gbaHD/GBAHD-Shield/static/wiki/168p_w_fuses.png

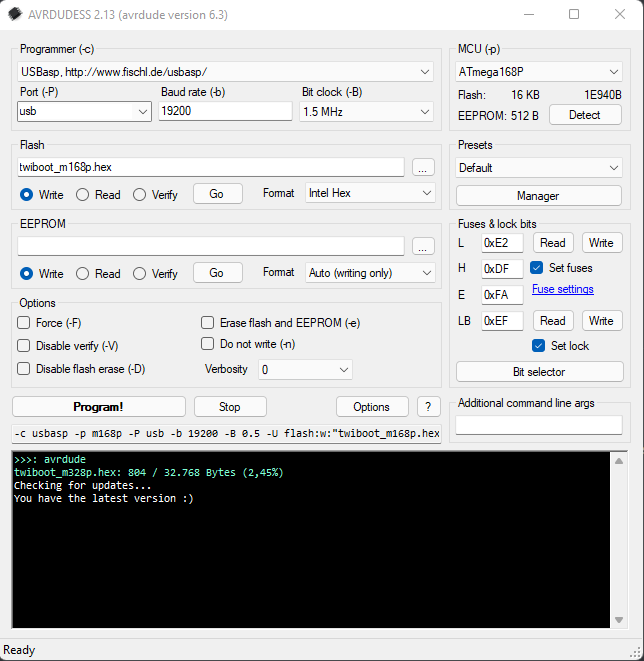
static/wiki/168p_w_fuses.png
