gbaHD/GBAHD-Shield/static/wiki/20210416_back.jpeg

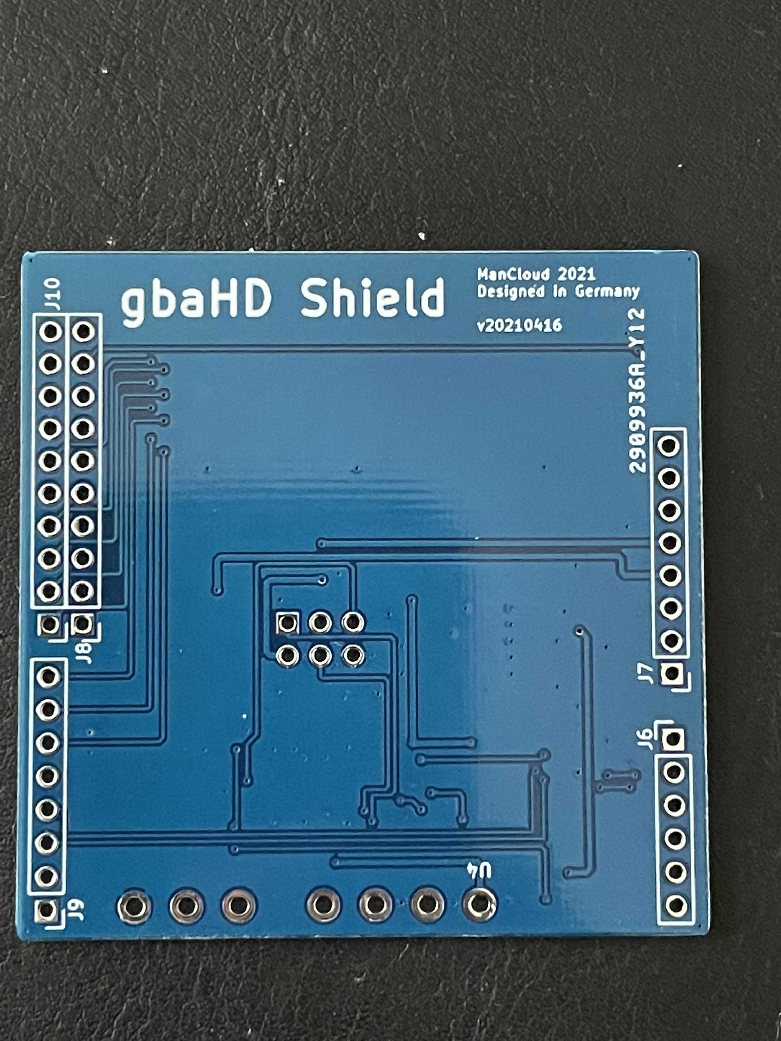
static/wiki/20210416_back.jpeg
