gbaHD/GBAHD-Shield/static/wiki/20210416_front.jpeg

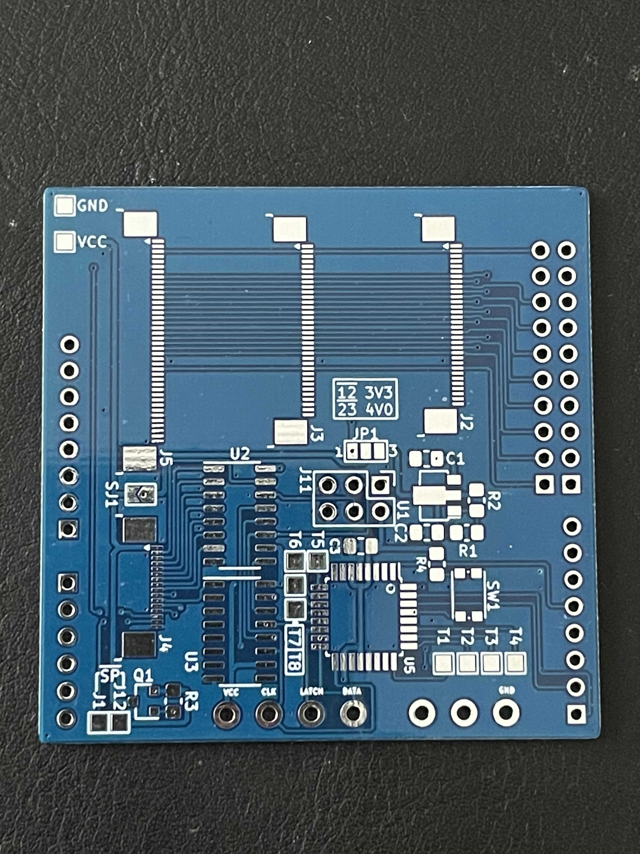
static/wiki/20210416_front.jpeg
