gbaHD/GBAHD-Shield/static/wiki/agb-cpu-03_power.jpg

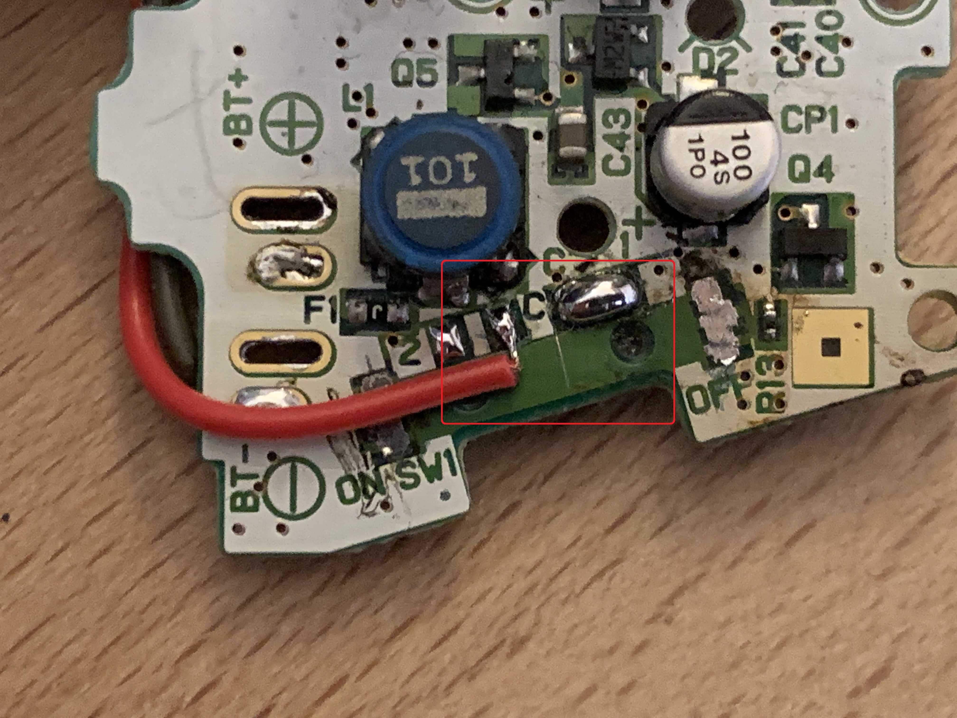
static/wiki/agb-cpu-03_power.jpg
