gbaHD/GBAHD-Shield/static/wiki/agb_cpu_03_clock-res.jpg

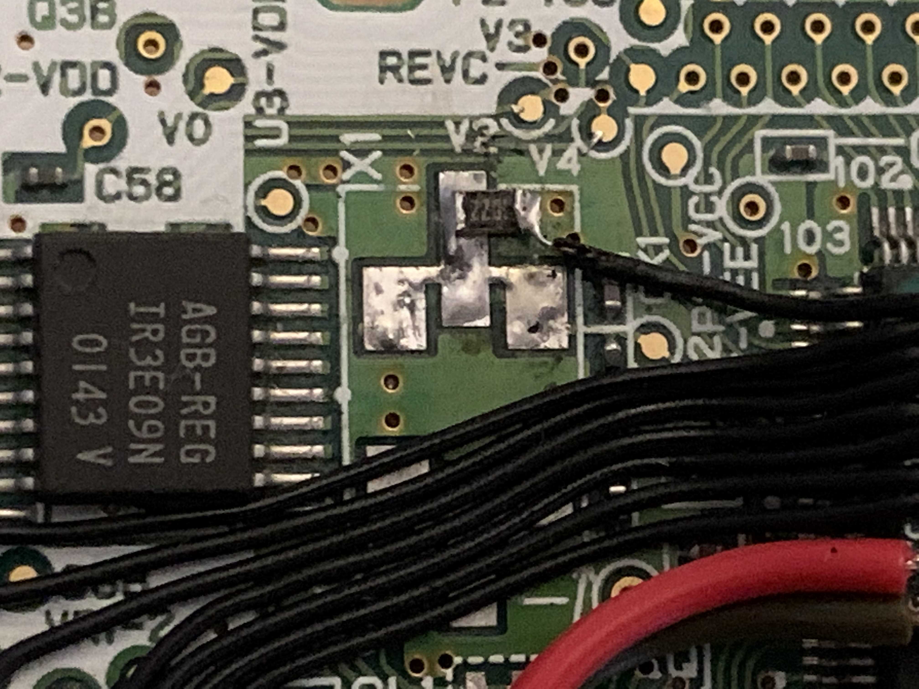
static/wiki/agb_cpu_03_clock-res.jpg
