gbaHD/GBAHD-Shield/static/wiki/arduino_nano_pins.jpg

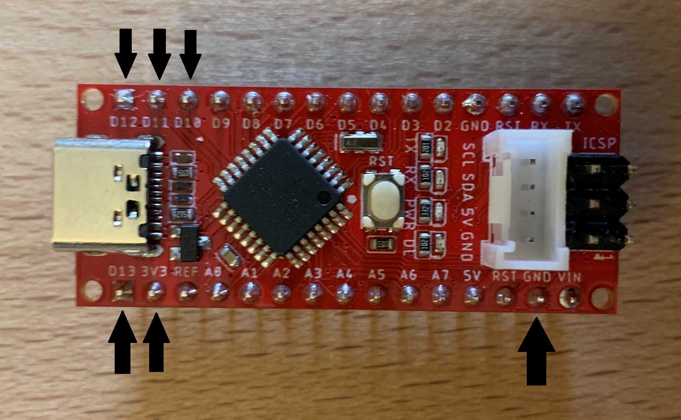
static/wiki/arduino_nano_pins.jpg
