gbaHD/GBAHD-Shield/static/wiki/arduinoide_isp_sketch2.jpg

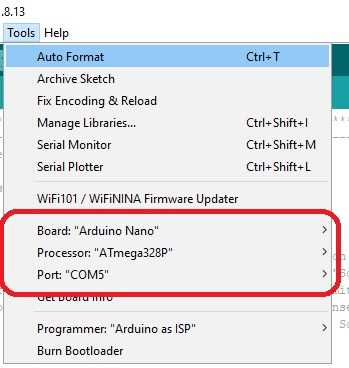
static/wiki/arduinoide_isp_sketch2.jpg
