gbaHD/GBAHD-Shield/static/wiki/arduinoide_isp_sketch.jpg

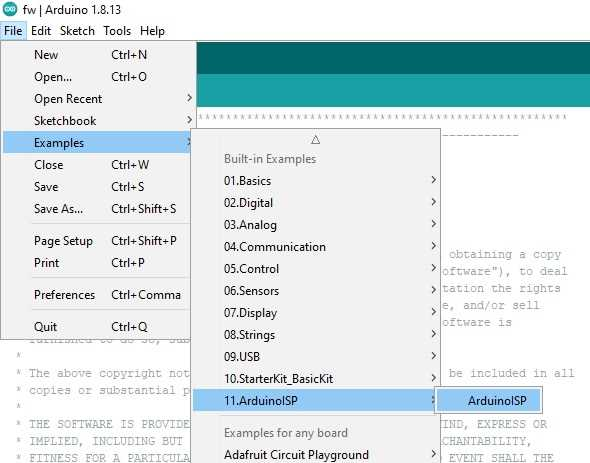
static/wiki/arduinoide_isp_sketch.jpg
