gbaHD/GBAHD-Shield/static/wiki/arduinoide_isp_sketch_upload.jpg

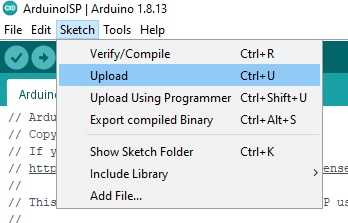
static/wiki/arduinoide_isp_sketch_upload.jpg
