gbaHD/GBAHD-Shield/static/wiki/arduinoide_shield.jpg

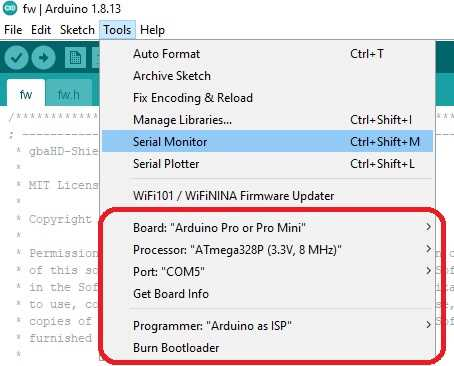
static/wiki/arduinoide_shield.jpg
