gbaHD/GBAHD-Shield/static/wiki/arduinoide_shield_upload_w_programmer.jpg

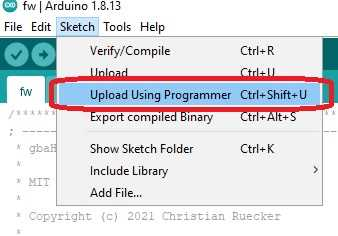
static/wiki/arduinoide_shield_upload_w_programmer.jpg
