gbaHD/GBAHD-Shield/static/wiki/arduinoideprefs.JPG

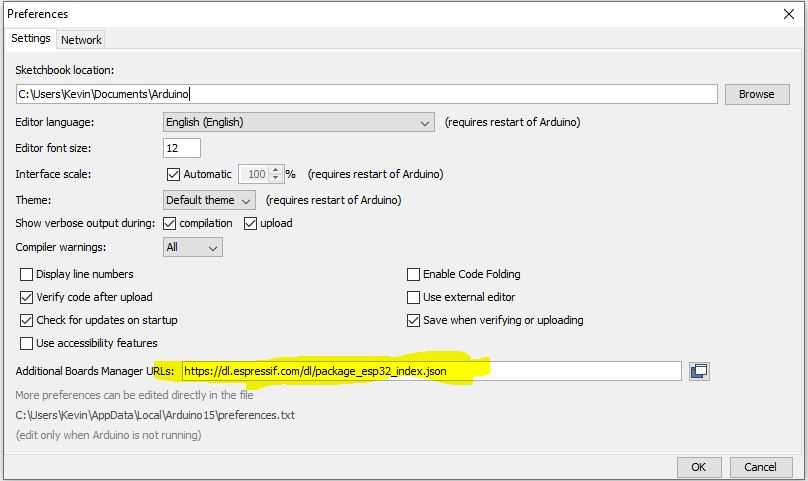
static/wiki/arduinoideprefs.JPG
