gbaHD/GBAHD-Shield/static/wiki/avrdude_fuses_w_website.JPG

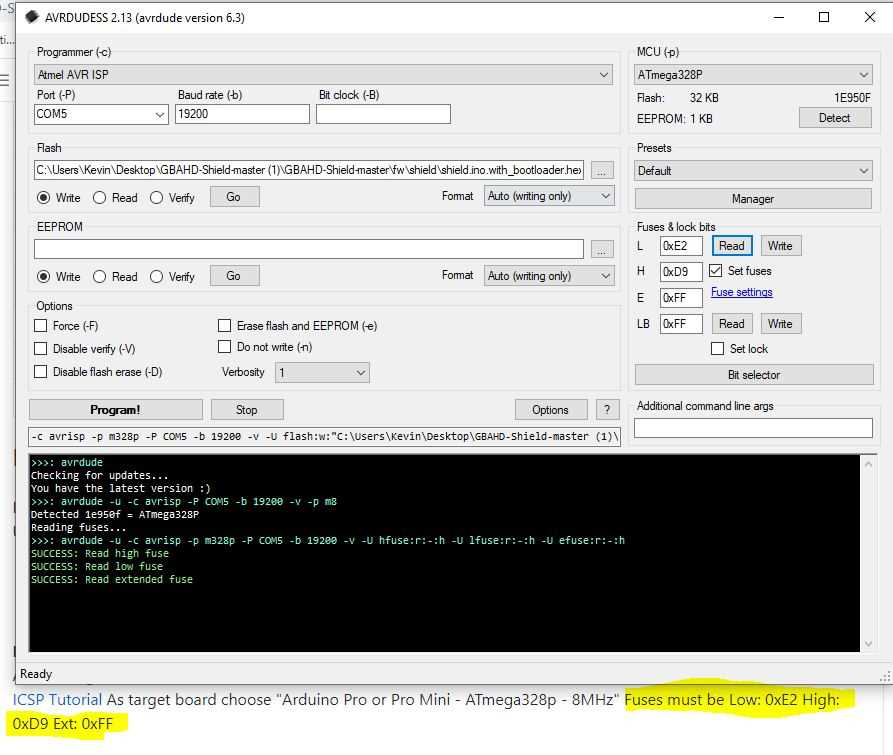
static/wiki/avrdude_fuses_w_website.JPG
