gbaHD/GBAHD-Shield/static/wiki/boardsmanager.JPG

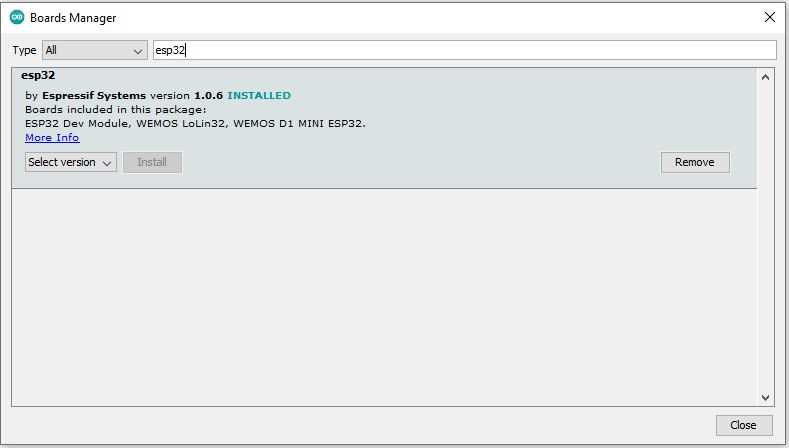
static/wiki/boardsmanager.JPG
