gbaHD/GBAHD-Shield/static/wiki/breadboard_programing.jpg

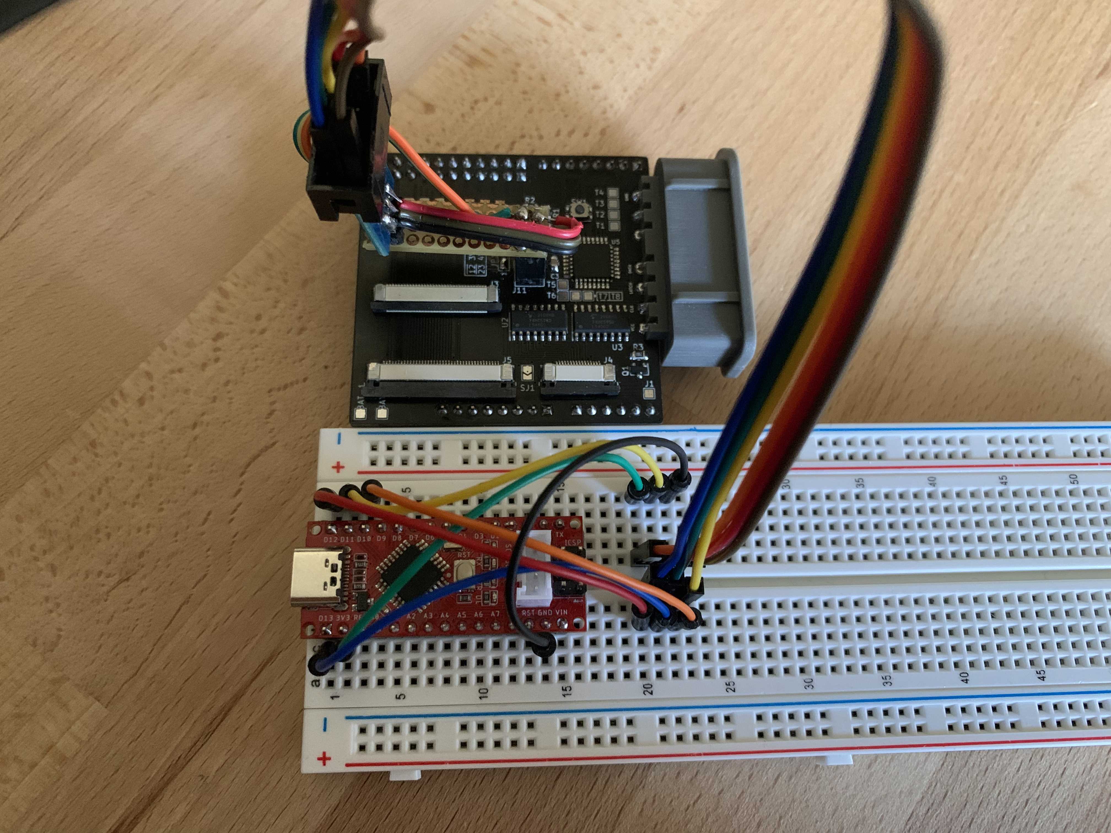
static/wiki/breadboard_programing.jpg
