gbaHD/GBAHD-Shield/static/wiki/case_ogba/35mm_jack.jpg

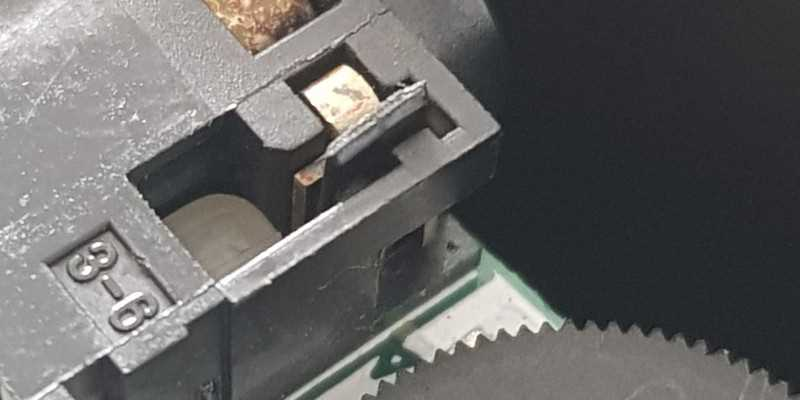
static/wiki/case_ogba/35mm_jack.jpg
