gbaHD/GBAHD-Shield/static/wiki/case_ogba/obga_top.jpg

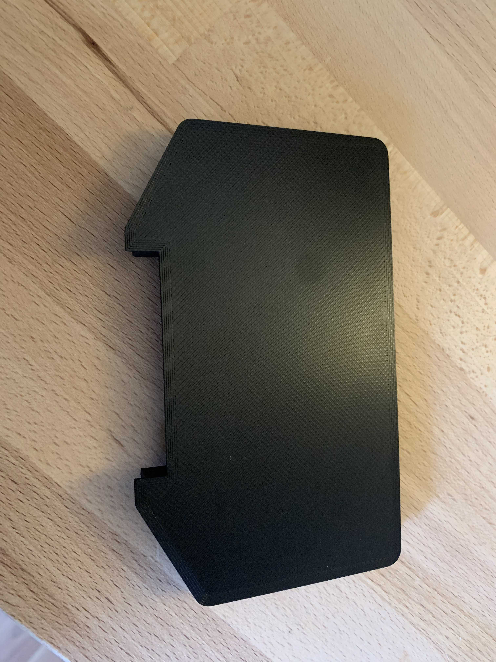
static/wiki/case_ogba/obga_top.jpg
