gbaHD/GBAHD-Shield/static/wiki/case_ogba/ogba_back.jpg

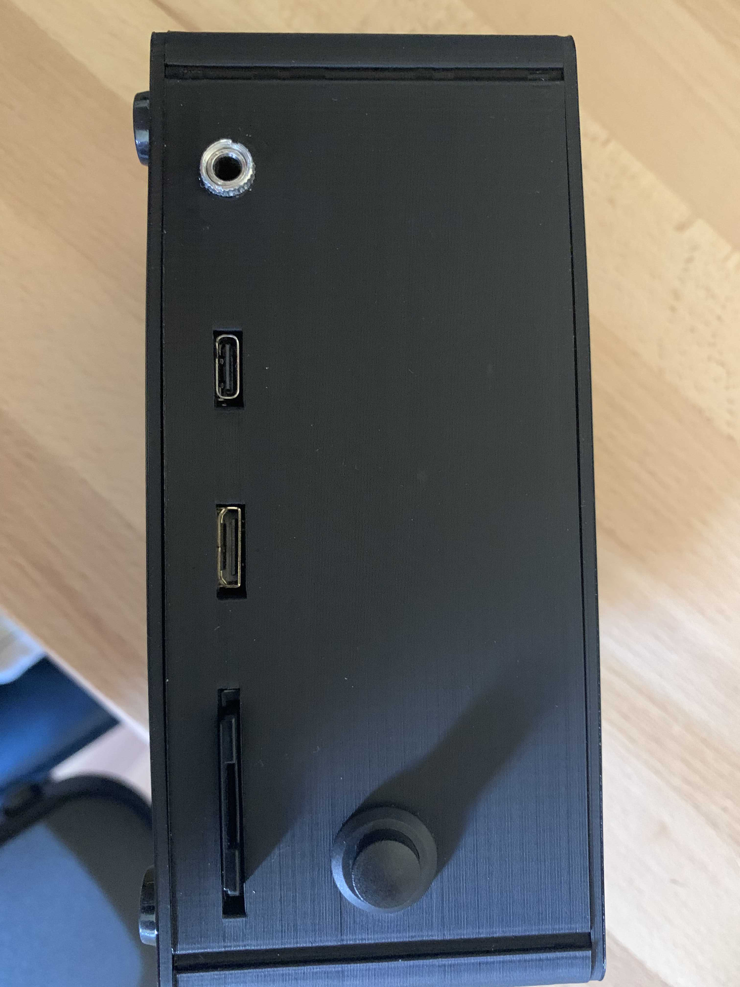
static/wiki/case_ogba/ogba_back.jpg
