gbaHD/GBAHD-Shield/static/wiki/case_ogba/ogba_bottom.jpg

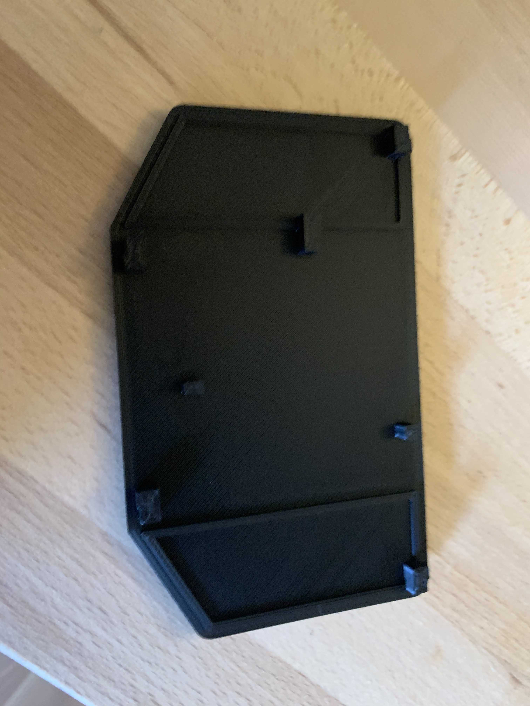
static/wiki/case_ogba/ogba_bottom.jpg
