gbaHD/GBAHD-Shield/static/wiki/case_ogba/ogba_bottom_finished.jpg

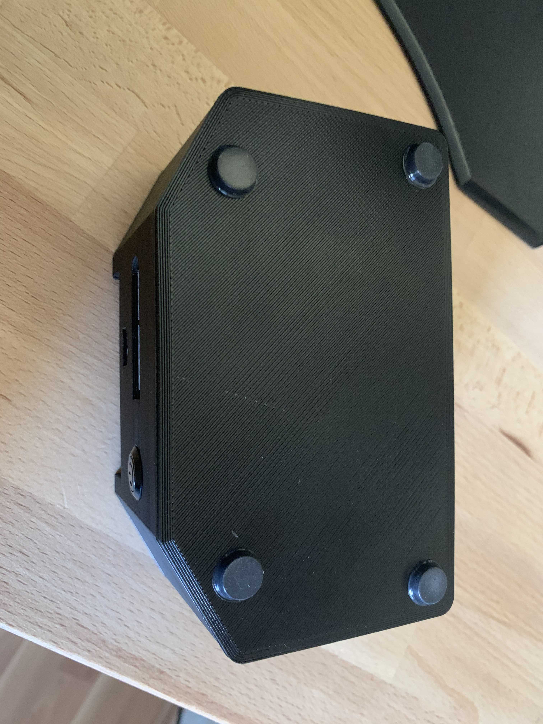
static/wiki/case_ogba/ogba_bottom_finished.jpg
