gbaHD/GBAHD-Shield/static/wiki/case_ogba/ogba_cartridgeflap.jpg

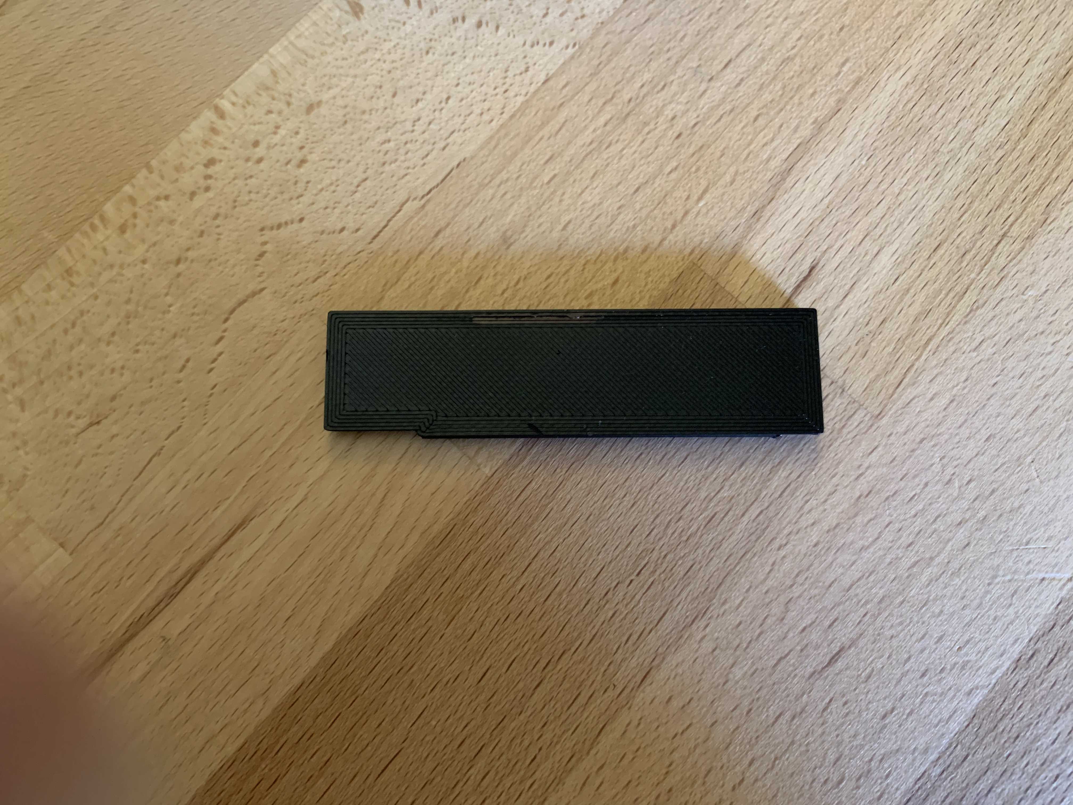
static/wiki/case_ogba/ogba_cartridgeflap.jpg
