gbaHD/GBAHD-Shield/static/wiki/case_ogba/ogba_case.jpg

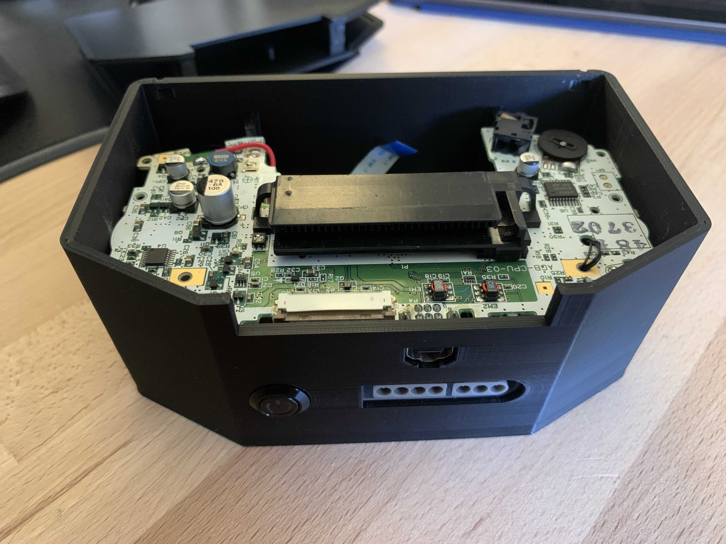
static/wiki/case_ogba/ogba_case.jpg
