gbaHD/GBAHD-Shield/static/wiki/case_ogba/ogba_case_angledspartan.jpg

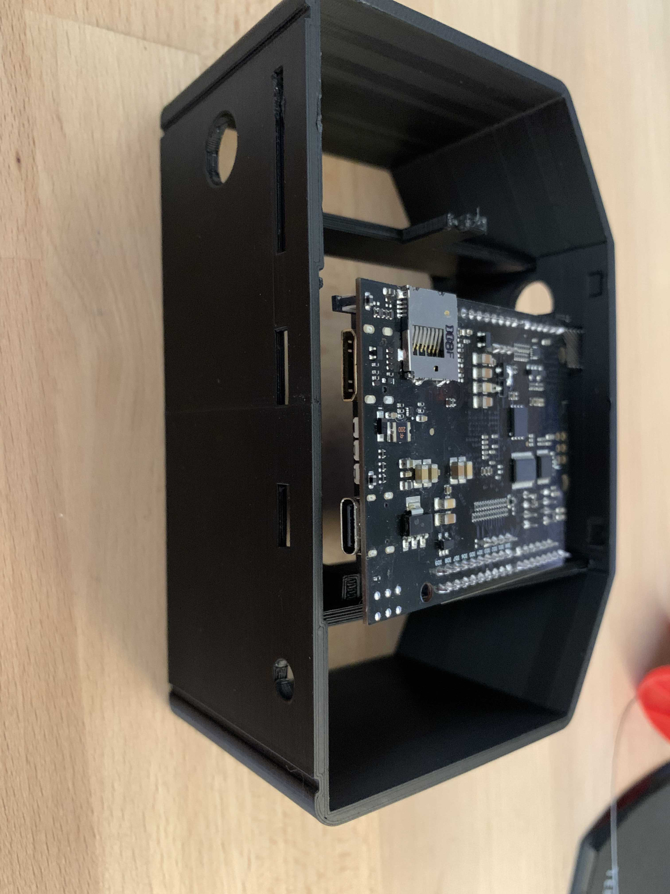
static/wiki/case_ogba/ogba_case_angledspartan.jpg
