gbaHD/GBAHD-Shield/static/wiki/case_ogba/ogba_case_bottom.jpg

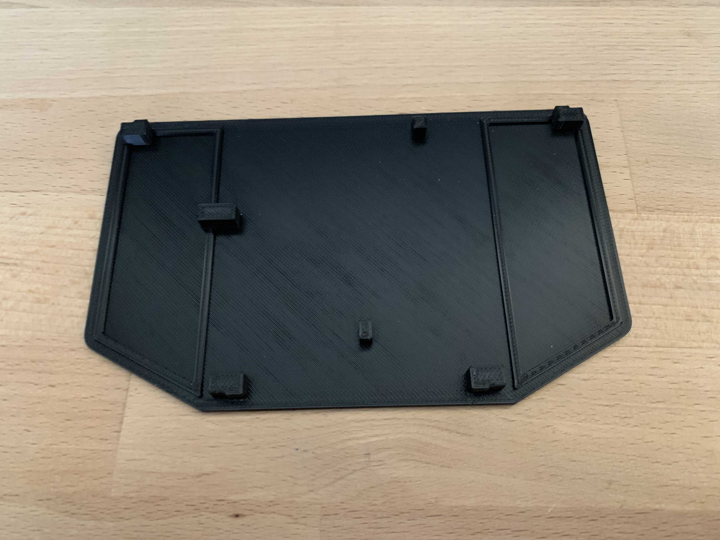
static/wiki/case_ogba/ogba_case_bottom.jpg
