gbaHD/GBAHD-Shield/static/wiki/case_ogba/ogba_case_cartflap.jpg

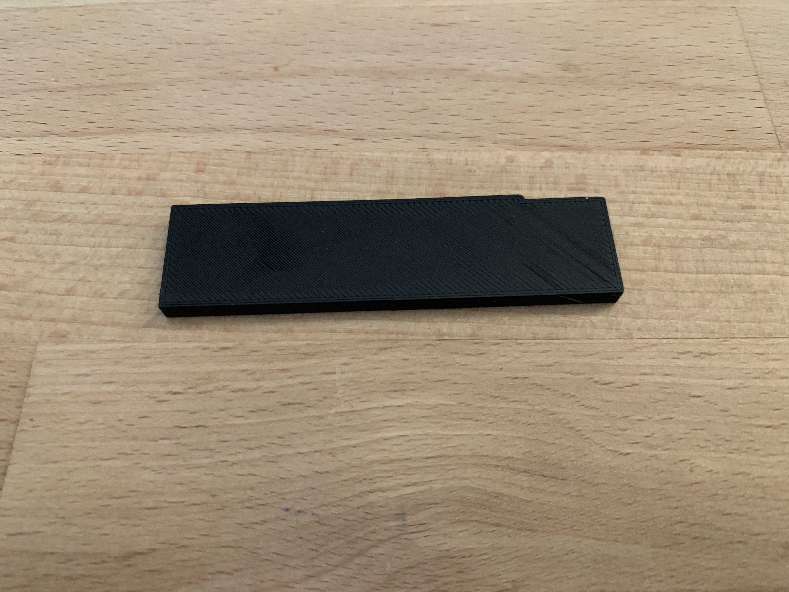
static/wiki/case_ogba/ogba_case_cartflap.jpg
