gbaHD/GBAHD-Shield/static/wiki/case_ogba/ogba_case_empty.jpg

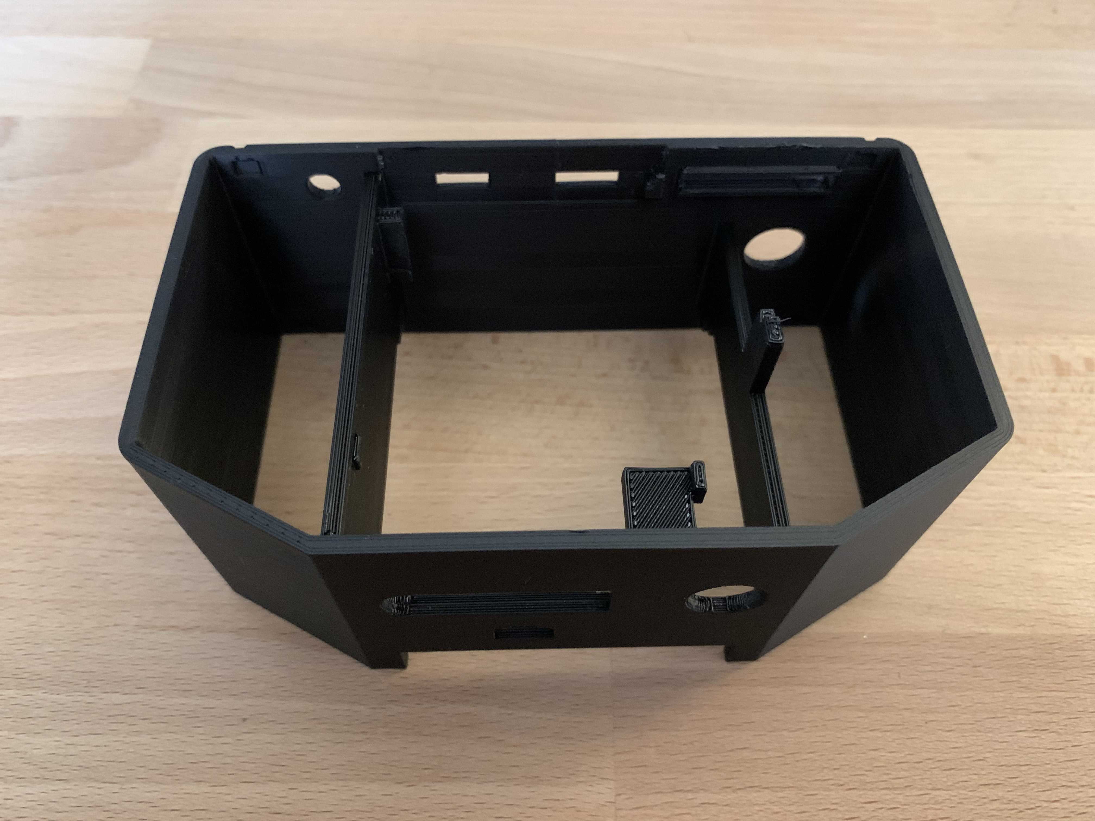
static/wiki/case_ogba/ogba_case_empty.jpg
