gbaHD/GBAHD-Shield/static/wiki/case_ogba/ogba_case_finished.jpg

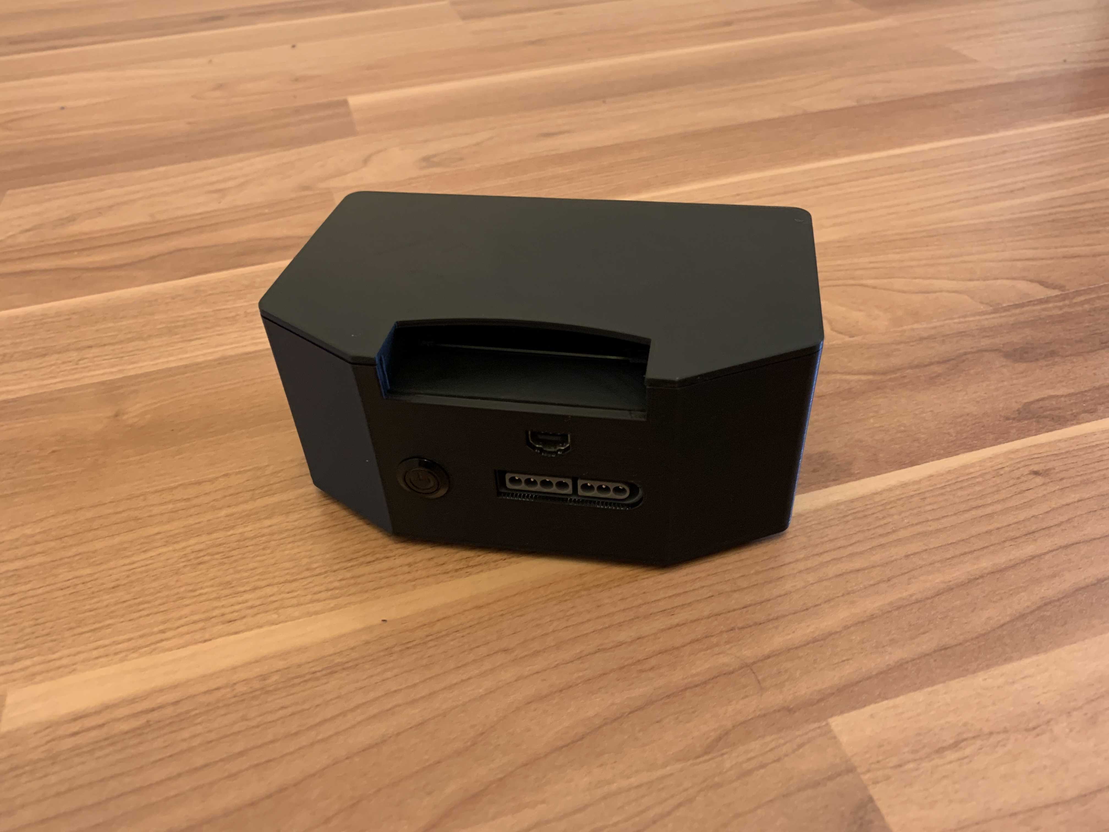
static/wiki/case_ogba/ogba_case_finished.jpg
