gbaHD/GBAHD-Shield/static/wiki/case_ogba/ogba_case_finished_wo_top2.jpg

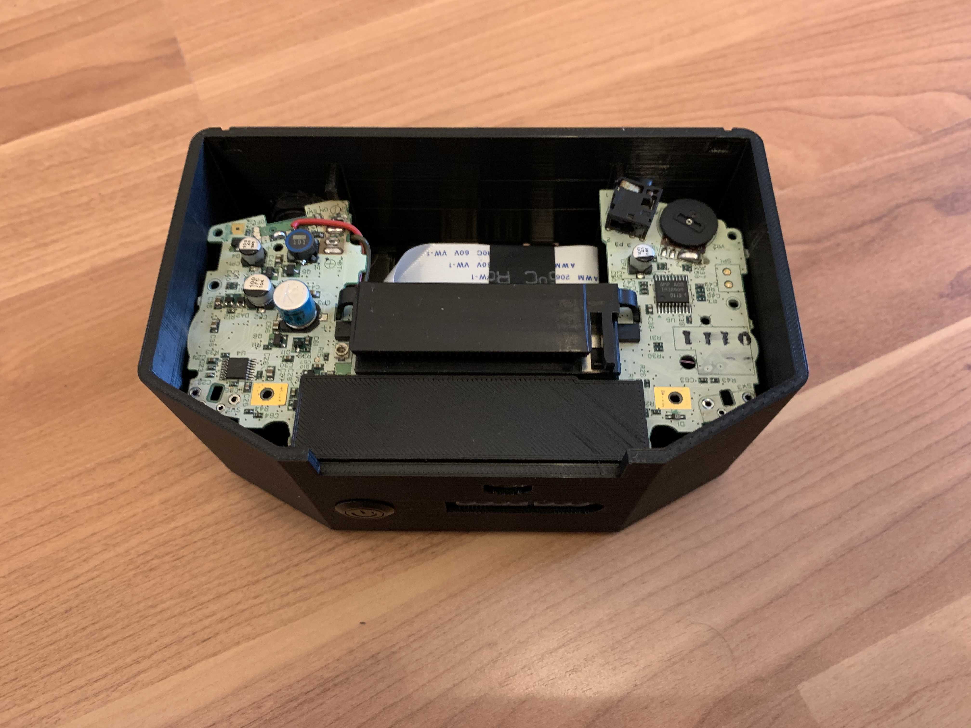
static/wiki/case_ogba/ogba_case_finished_wo_top2.jpg
