gbaHD/GBAHD-Shield/static/wiki/case_ogba/ogba_case_finished_wo_top.jpg

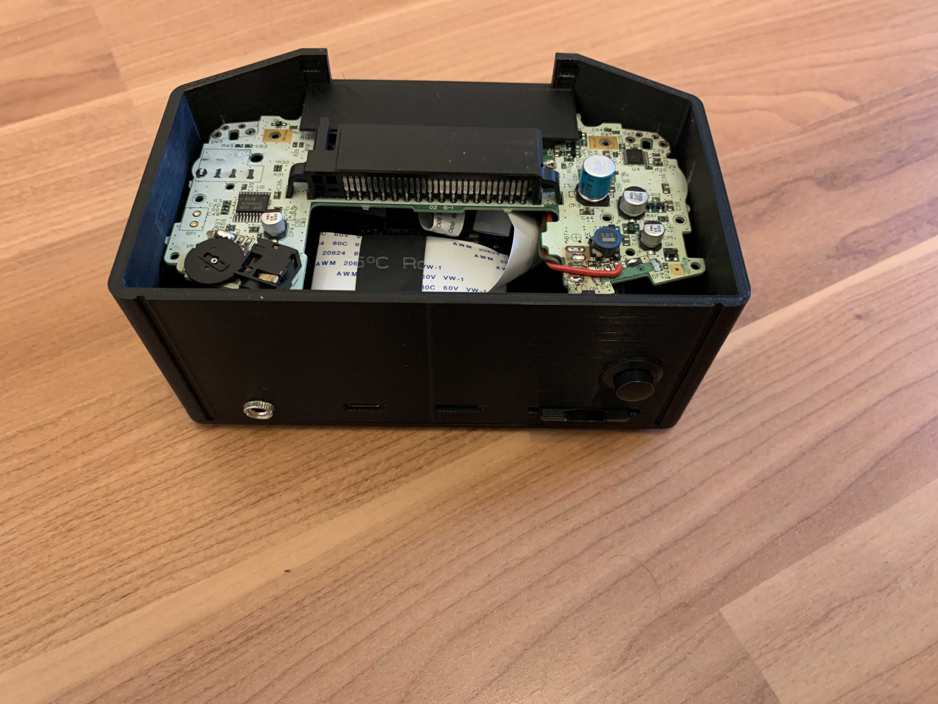
static/wiki/case_ogba/ogba_case_finished_wo_top.jpg
