gbaHD/GBAHD-Shield/static/wiki/case_ogba/ogba_case_gba_w_flex.jpg

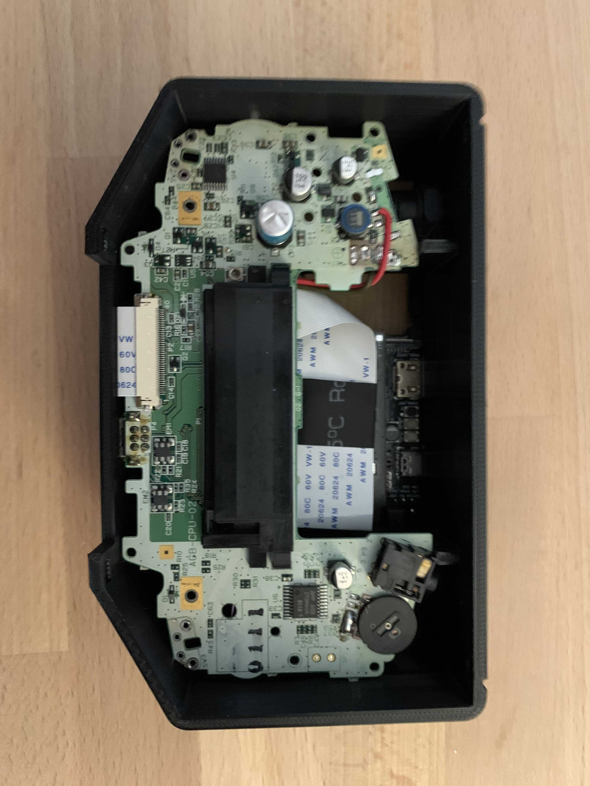
static/wiki/case_ogba/ogba_case_gba_w_flex.jpg
