gbaHD/GBAHD-Shield/static/wiki/case_ogba/ogba_case_gba_wired.jpg

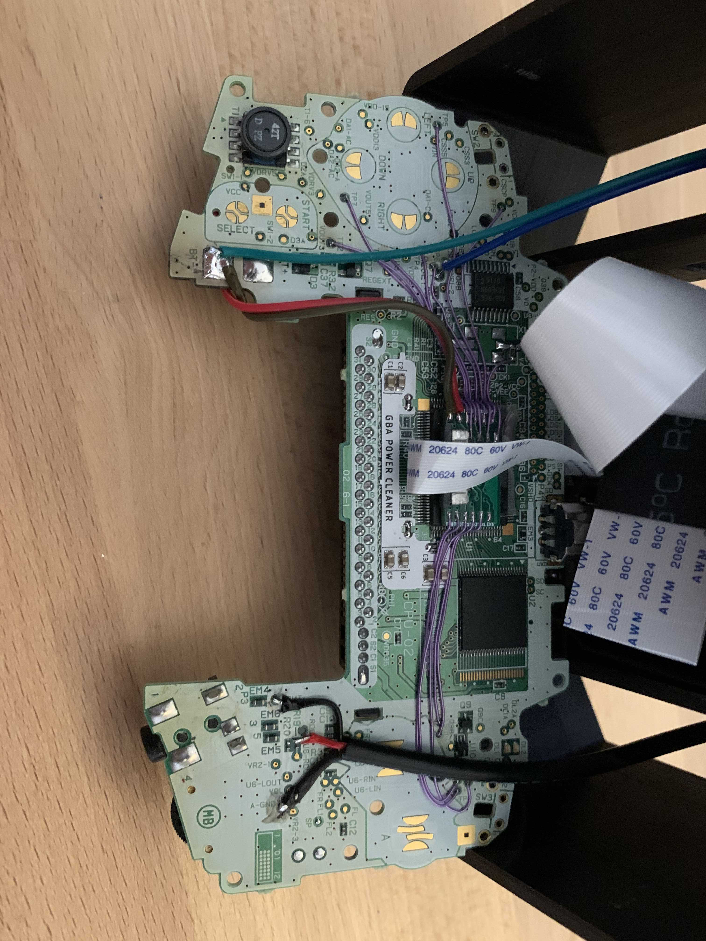
static/wiki/case_ogba/ogba_case_gba_wired.jpg
