gbaHD/GBAHD-Shield/static/wiki/case_ogba/ogba_case_spartan_in2.jpg

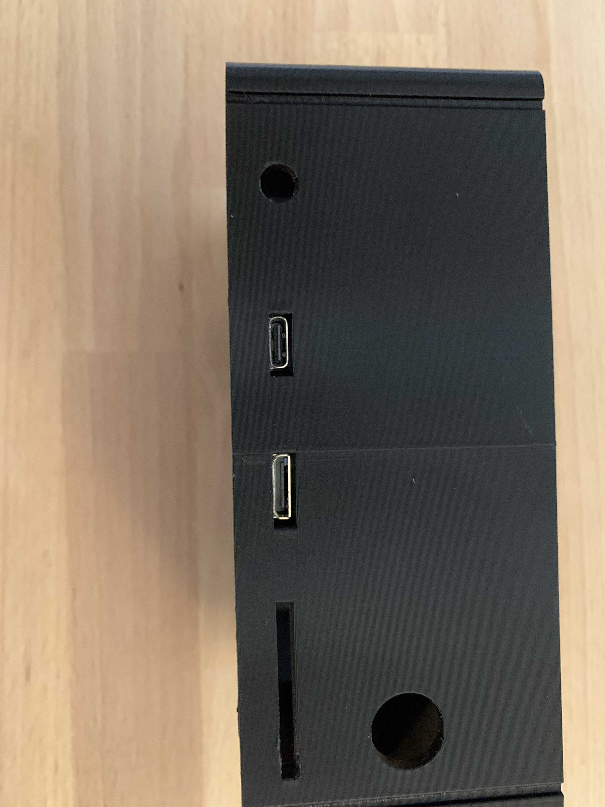
static/wiki/case_ogba/ogba_case_spartan_in2.jpg
