gbaHD/GBAHD-Shield/static/wiki/case_ogba/ogba_case_spartan_in.jpg

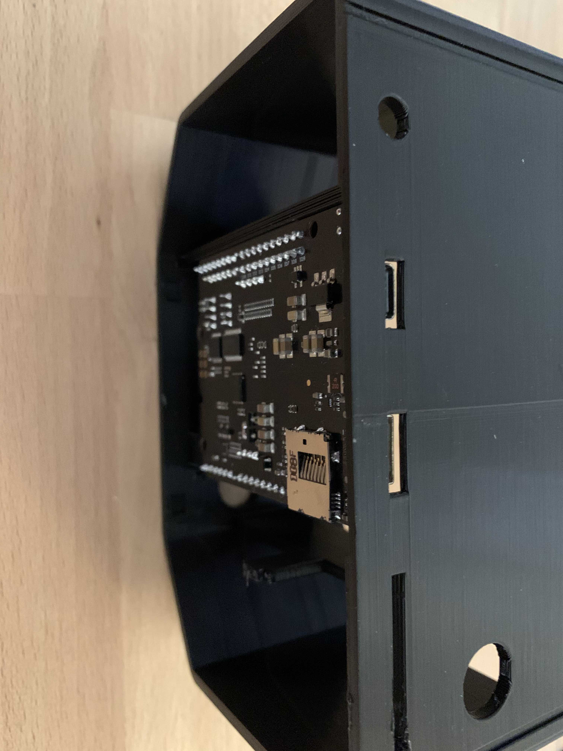
static/wiki/case_ogba/ogba_case_spartan_in.jpg
