gbaHD/GBAHD-Shield/static/wiki/case_ogba/ogba_case_spartan_switches.jpg

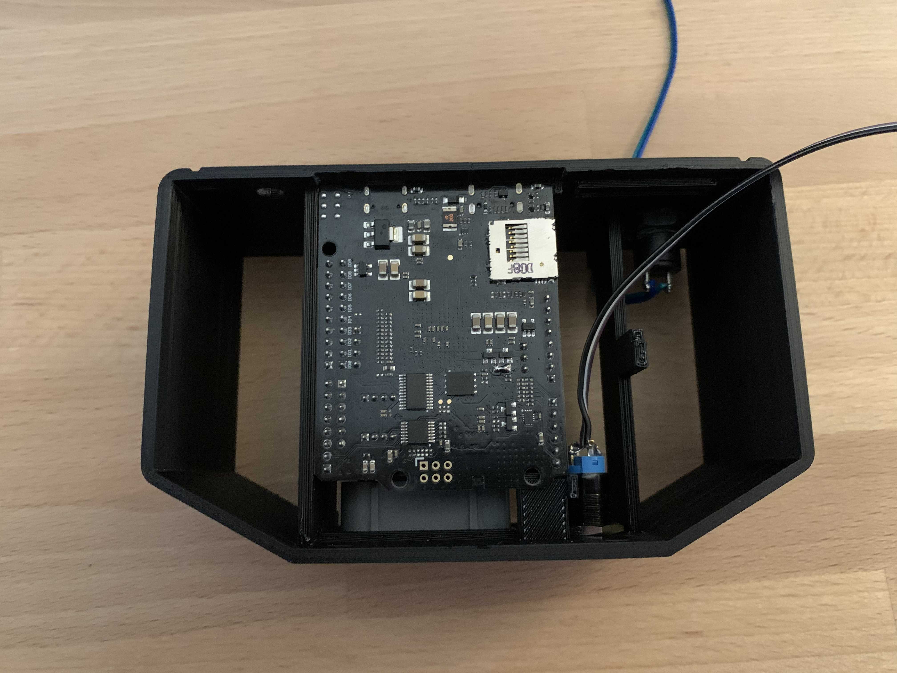
static/wiki/case_ogba/ogba_case_spartan_switches.jpg
