gbaHD/GBAHD-Shield/static/wiki/case_ogba/ogba_case_top.jpg

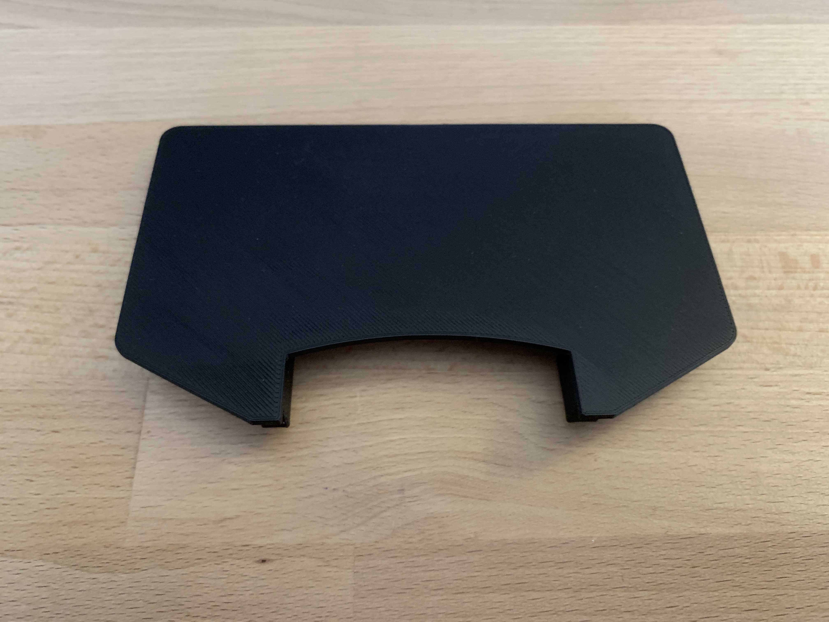
static/wiki/case_ogba/ogba_case_top.jpg
