gbaHD/GBAHD-Shield/static/wiki/case_ogba/ogba_finished-bottom.jpg

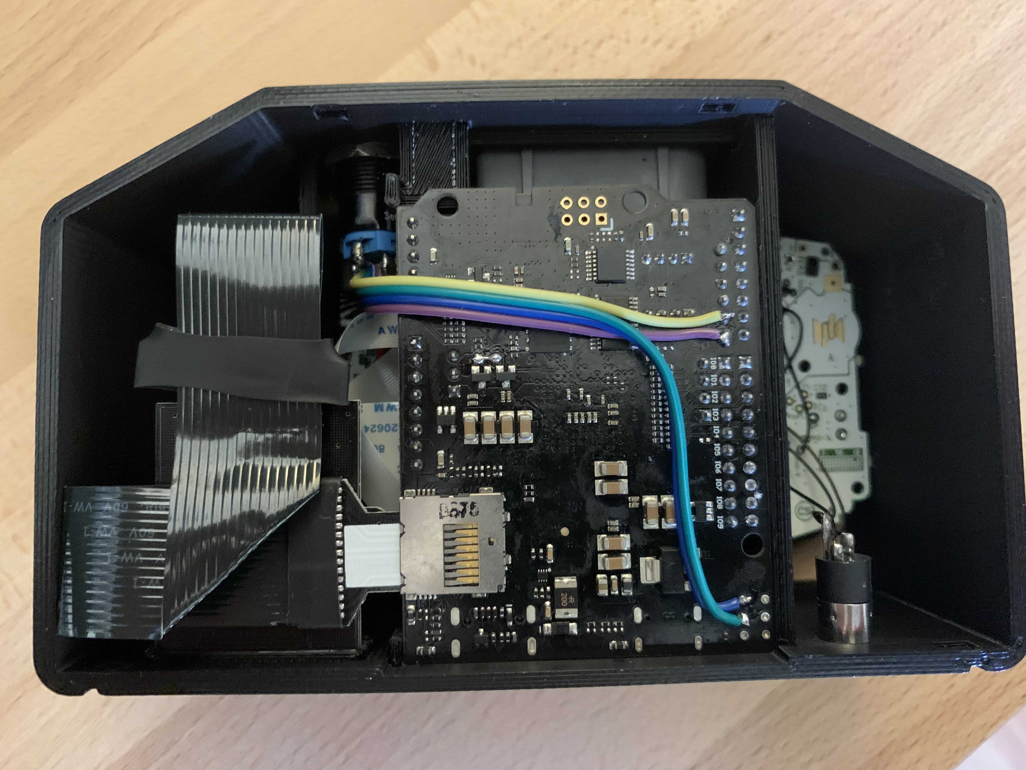
static/wiki/case_ogba/ogba_finished-bottom.jpg
