gbaHD/GBAHD-Shield/static/wiki/case_ogba/ogba_mainboard-seated.jpg

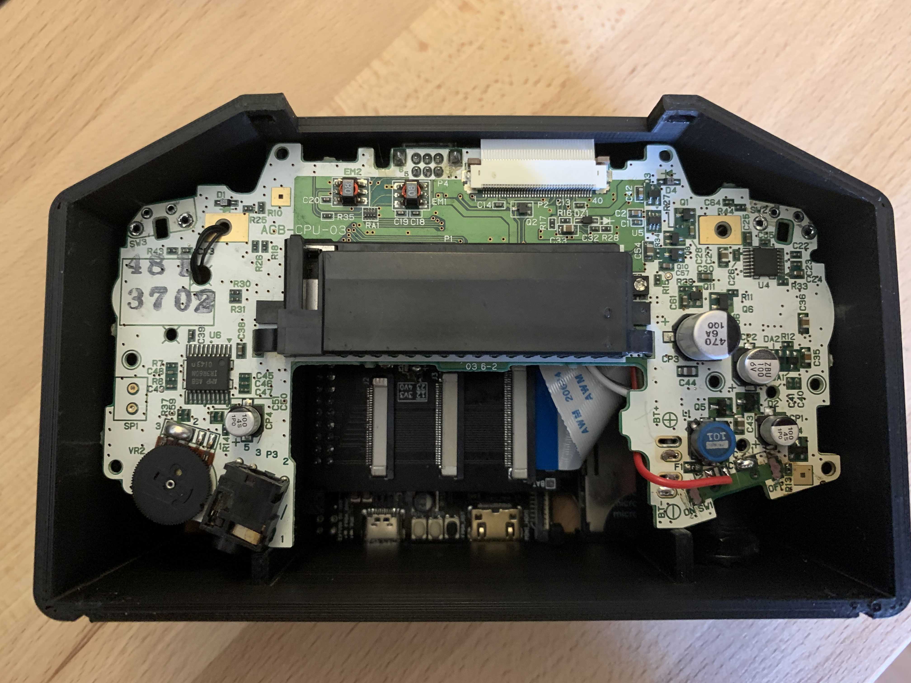
static/wiki/case_ogba/ogba_mainboard-seated.jpg
