gbaHD/GBAHD-Shield/static/wiki/case_ogba/ogba_mainboard.jpg

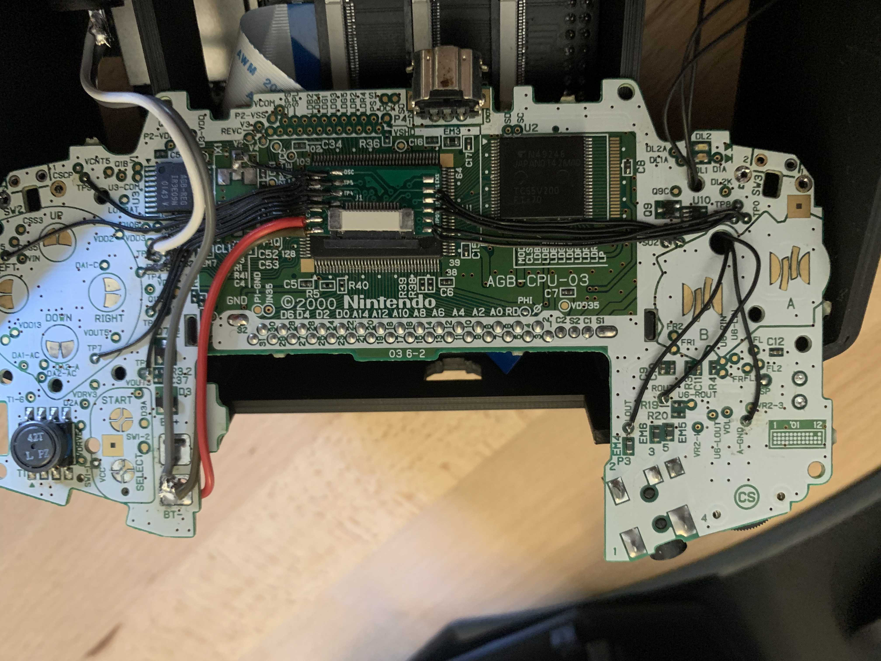
static/wiki/case_ogba/ogba_mainboard.jpg
