gbaHD/GBAHD-Shield/static/wiki/case_ogba/ogba_top_finished.jpg

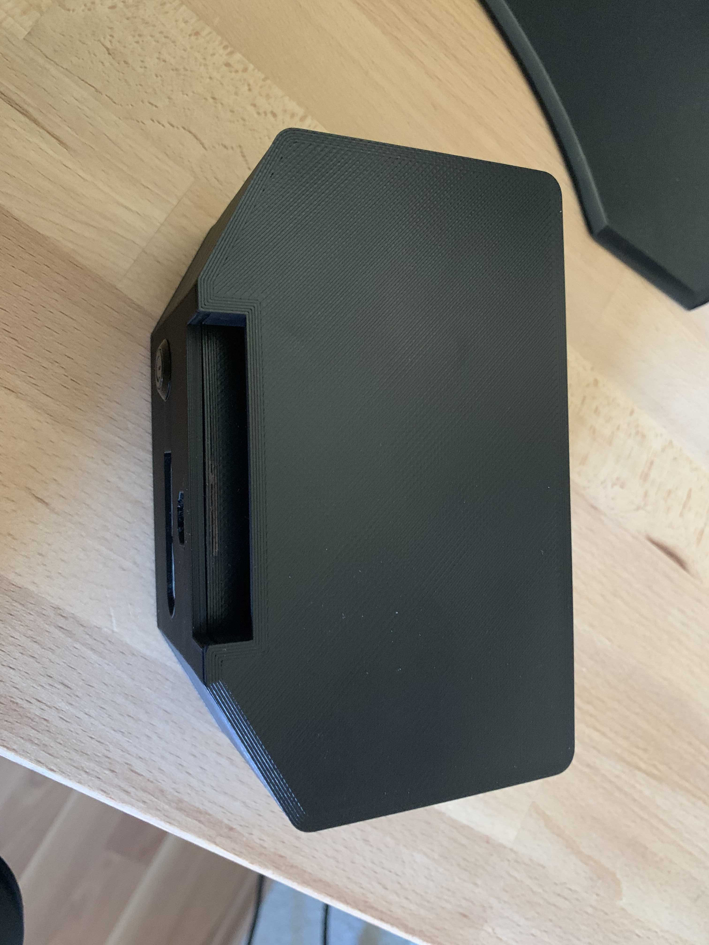
static/wiki/case_ogba/ogba_top_finished.jpg
