gbaHD/GBAHD-Shield/static/wiki/case_ogba/ogba_top_w_flap.jpg

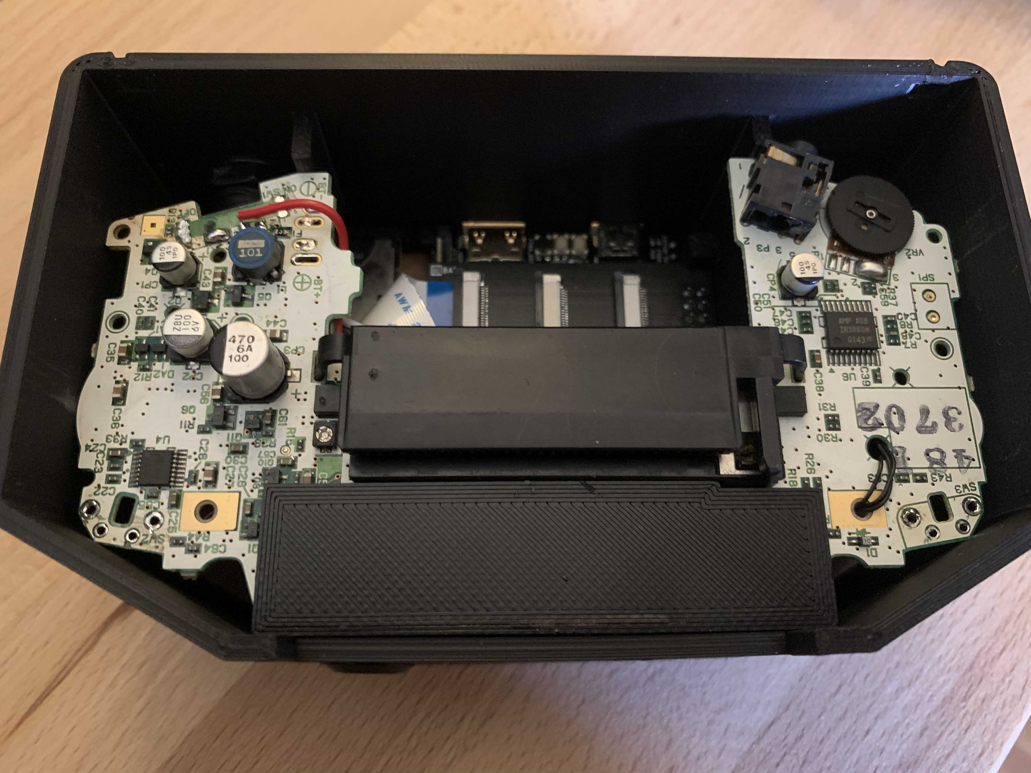
static/wiki/case_ogba/ogba_top_w_flap.jpg
