gbaHD/GBAHD-Shield/static/wiki/case_ogba/resetbutton.jpg

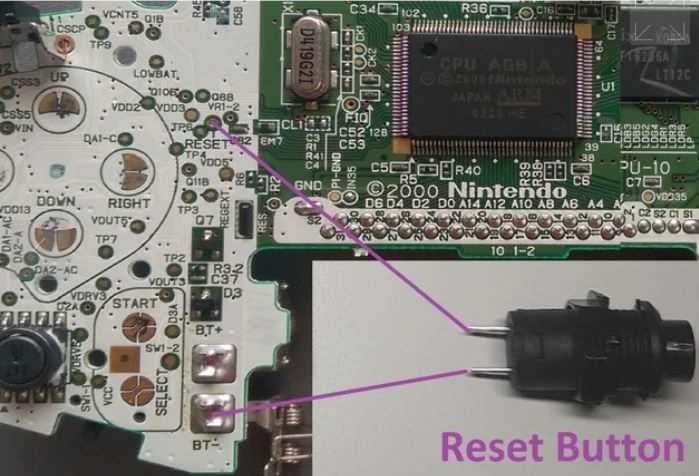
static/wiki/case_ogba/resetbutton.jpg
