gbaHD/GBAHD-Shield/static/wiki/case_ogba/sd-card-fold.jpg

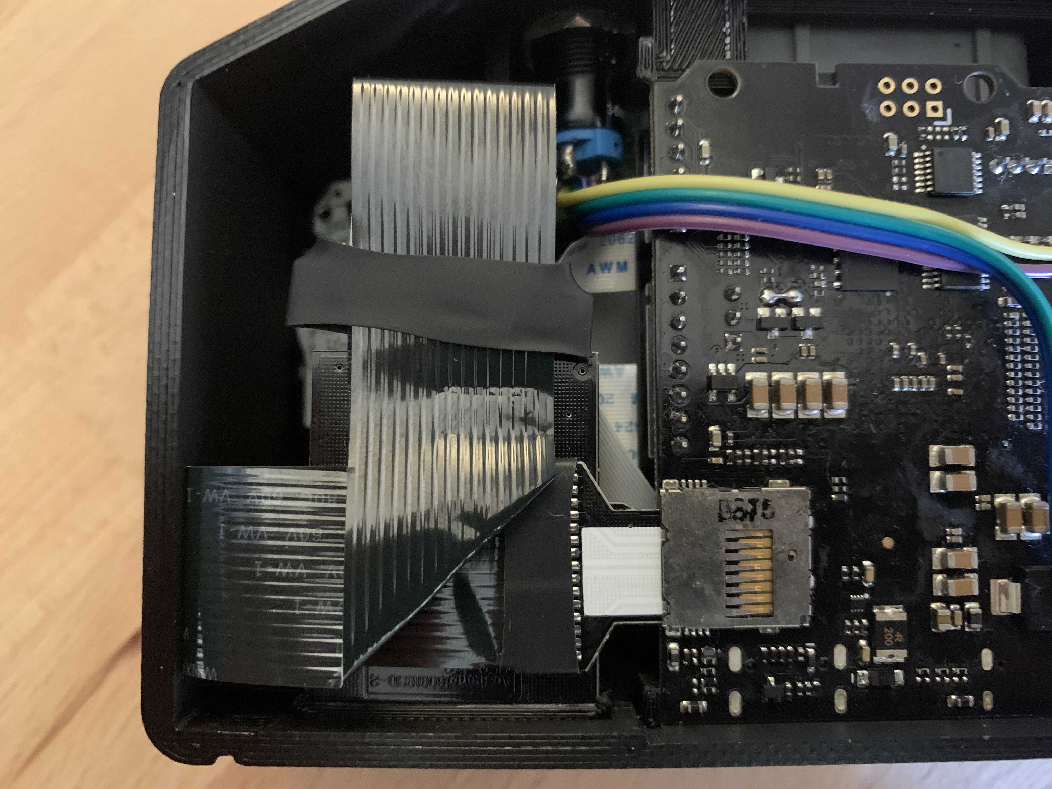
static/wiki/case_ogba/sd-card-fold.jpg
