gbaHD/GBAHD-Shield/static/wiki/case_ogba/sd-card.jpg

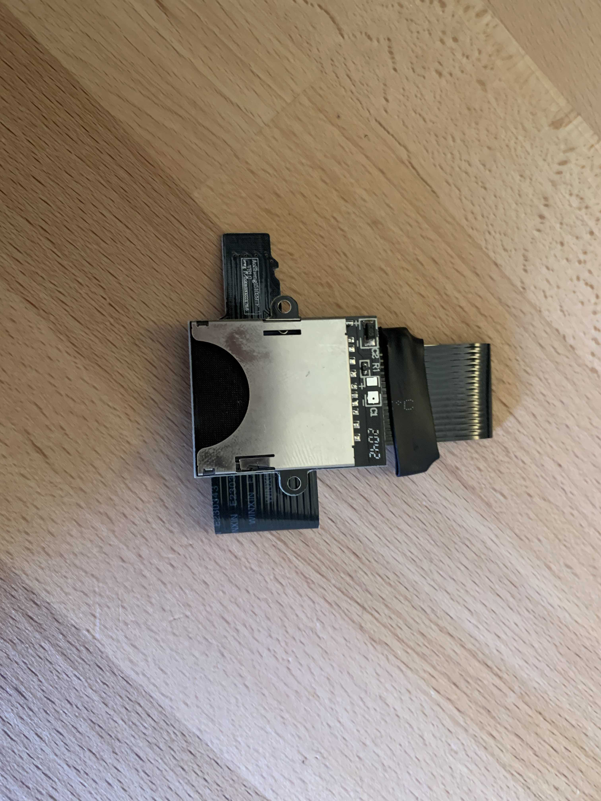
static/wiki/case_ogba/sd-card.jpg
