gbaHD/GBAHD-Shield/static/wiki/case_sp/case0_flap.jpg

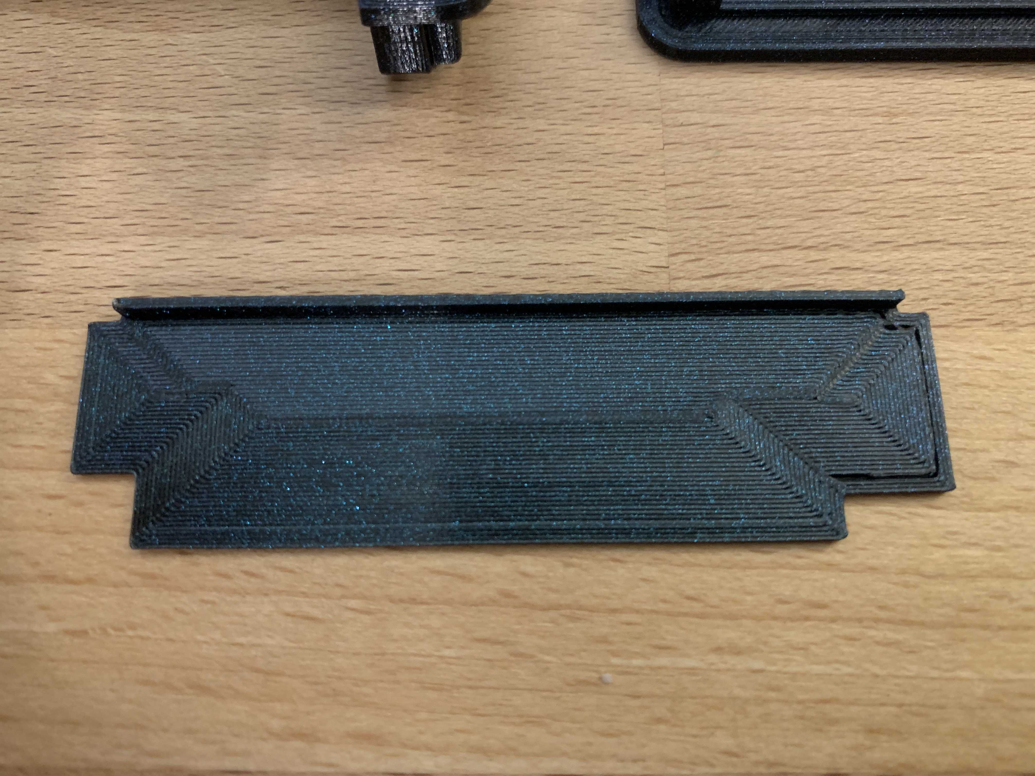
static/wiki/case_sp/case0_flap.jpg
