gbaHD/GBAHD-Shield/static/wiki/case_sp/case0_top.jpg

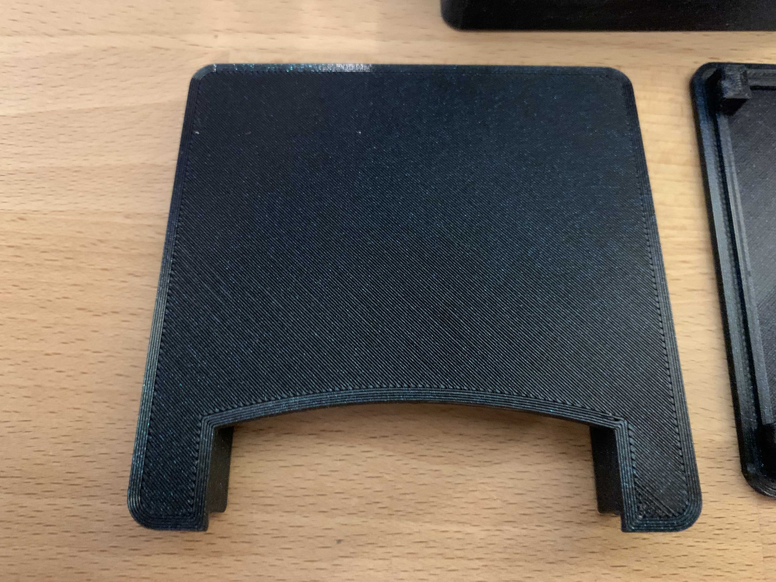
static/wiki/case_sp/case0_top.jpg
