gbaHD/GBAHD-Shield/static/wiki/case_sp/case_finished_back.jpg

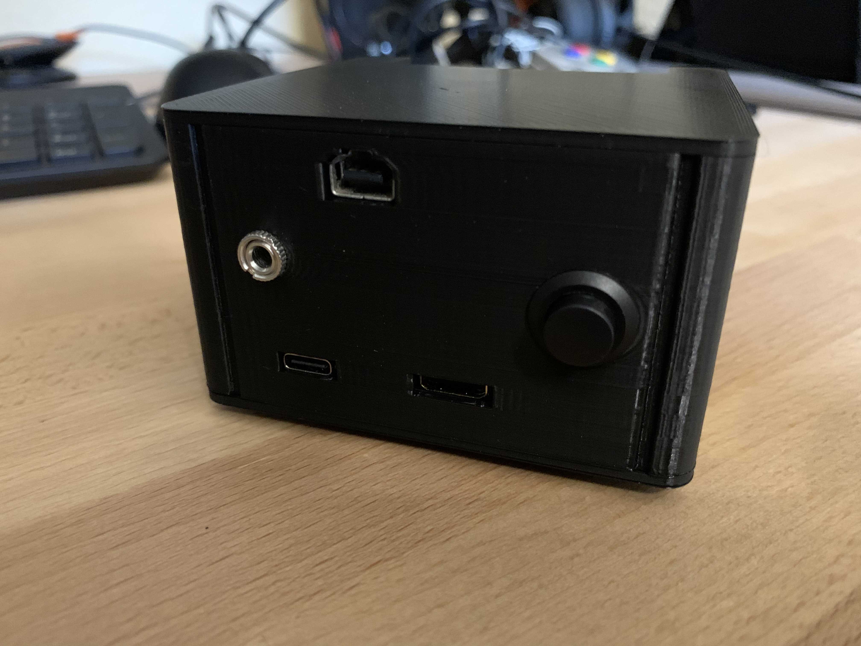
static/wiki/case_sp/case_finished_back.jpg
