gbaHD/GBAHD-Shield/static/wiki/case_sp/case_finished_bottim.jpg

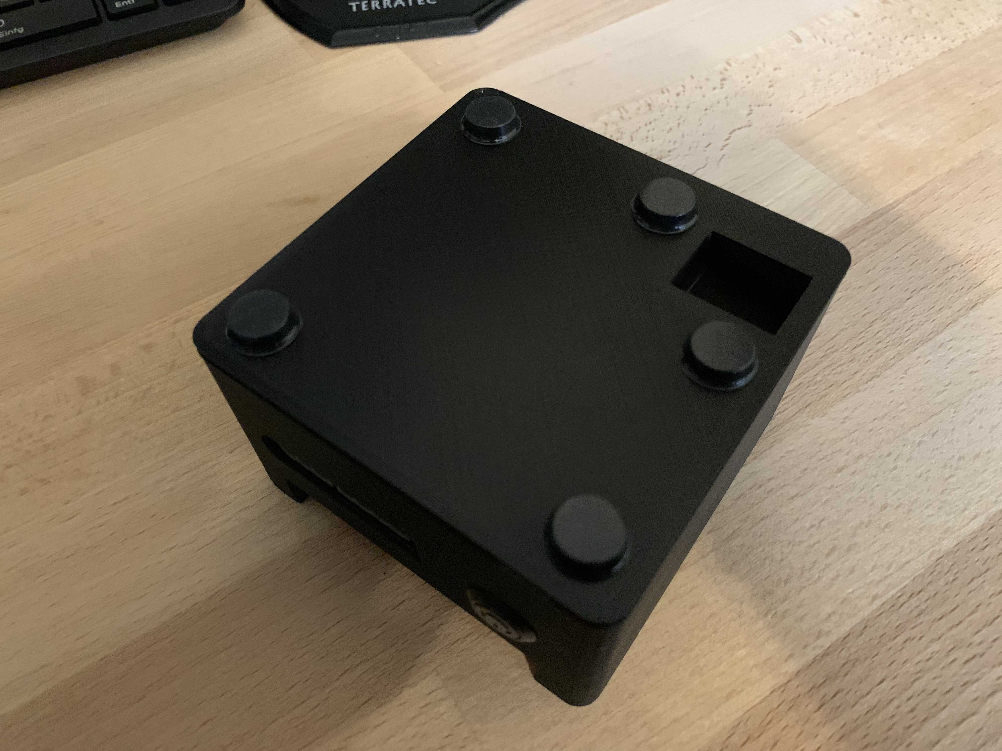
static/wiki/case_sp/case_finished_bottim.jpg
