gbaHD/GBAHD-Shield/static/wiki/case_sp/case_finished_top.jpg

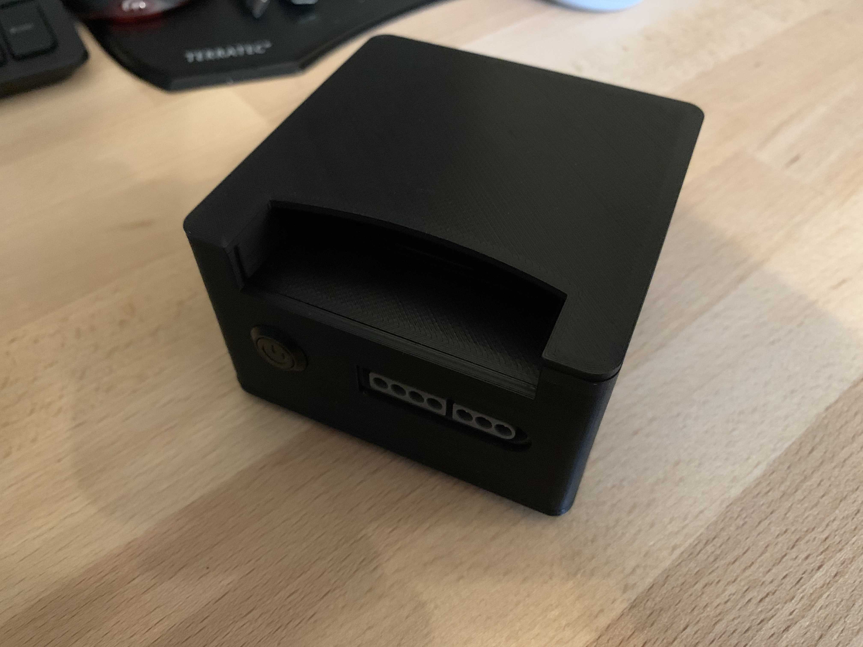
static/wiki/case_sp/case_finished_top.jpg
