gbaHD/GBAHD-Shield/static/wiki/case_sp/case_flap.jpg

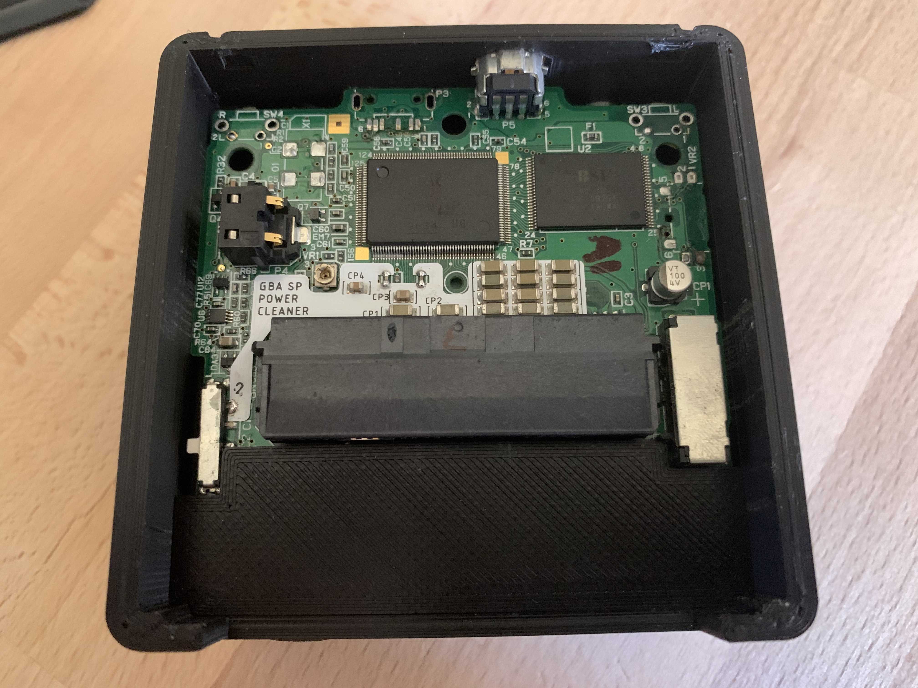
static/wiki/case_sp/case_flap.jpg
