gbaHD/GBAHD-Shield/static/wiki/case_sp/case_flexcabled.jpg

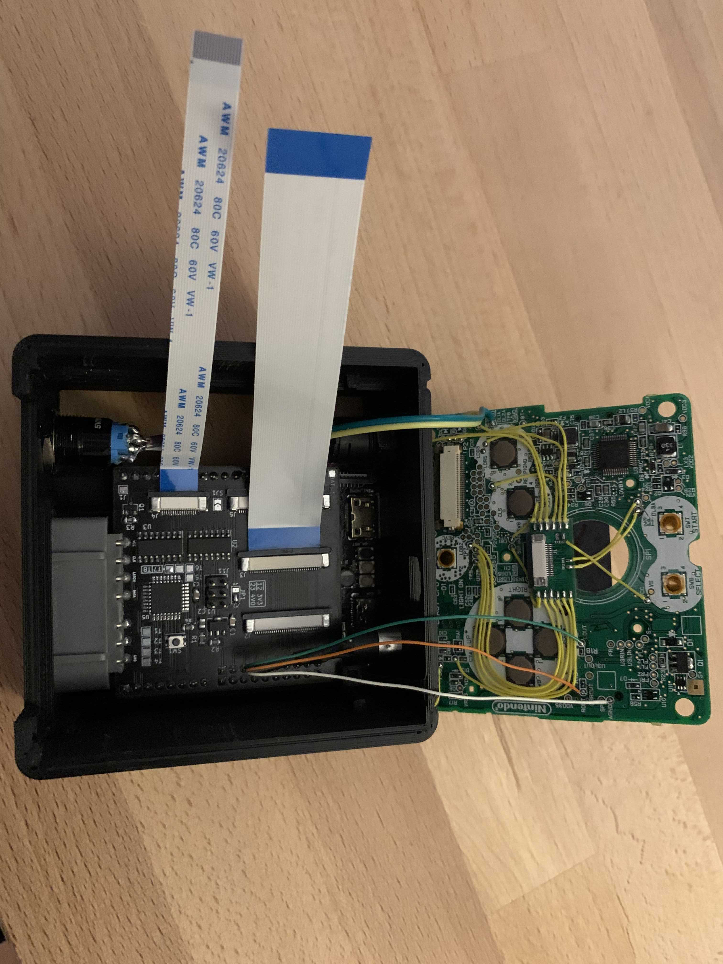
static/wiki/case_sp/case_flexcabled.jpg
