gbaHD/GBAHD-Shield/static/wiki/case_sp/case_shield2.jpg

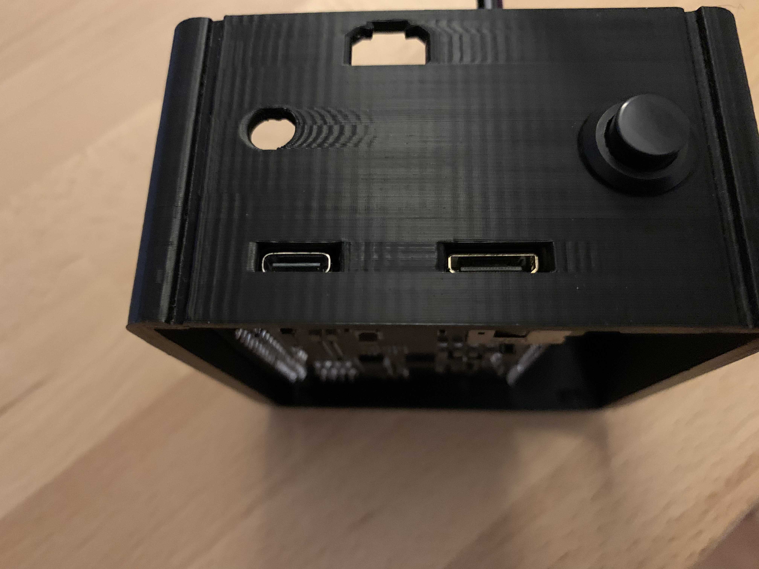
static/wiki/case_sp/case_shield2.jpg
