gbaHD/GBAHD-Shield/static/wiki/case_sp/case_shield3.jpg

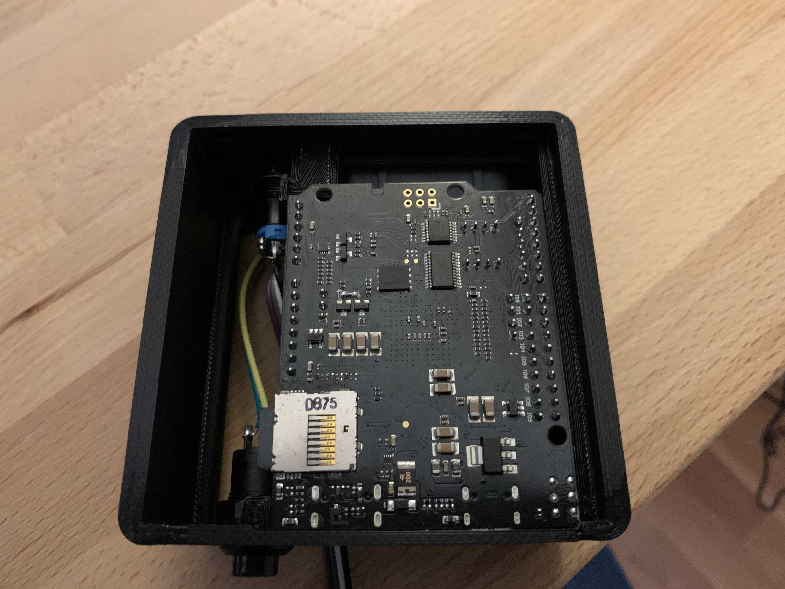
static/wiki/case_sp/case_shield3.jpg
