gbaHD/GBAHD-Shield/static/wiki/case_sp/case_shield4.jpg

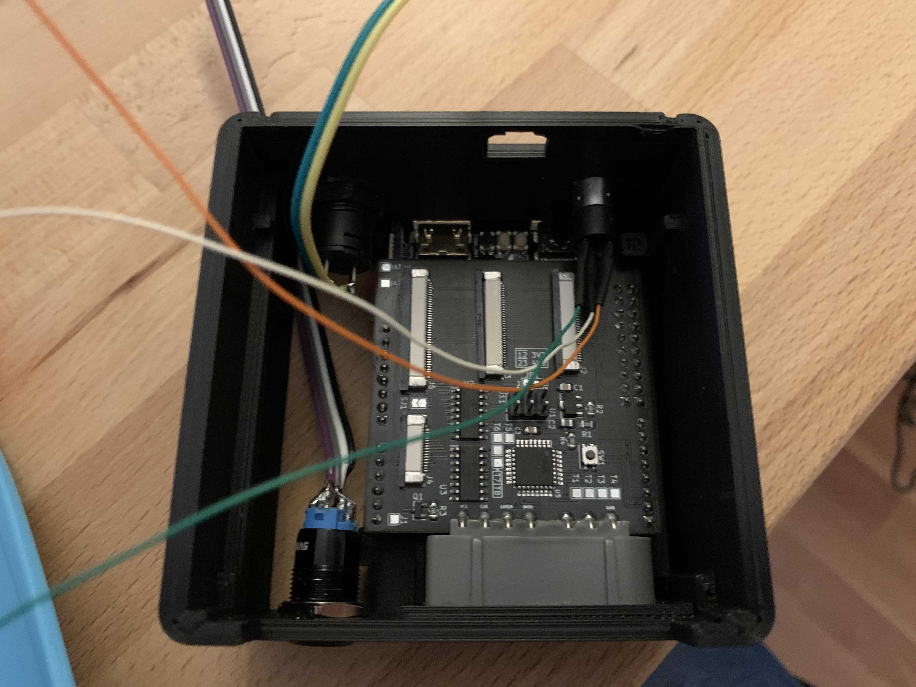
static/wiki/case_sp/case_shield4.jpg
