gbaHD/GBAHD-Shield/static/wiki/case_sp/case_shield_0.jpg

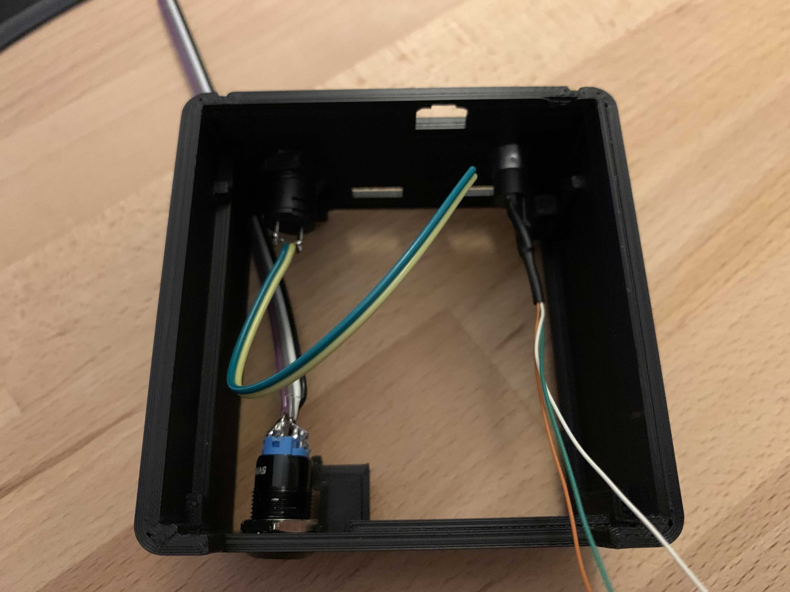
static/wiki/case_sp/case_shield_0.jpg
