gbaHD/GBAHD-Shield/static/wiki/case_sp/case_shield_1.jpg

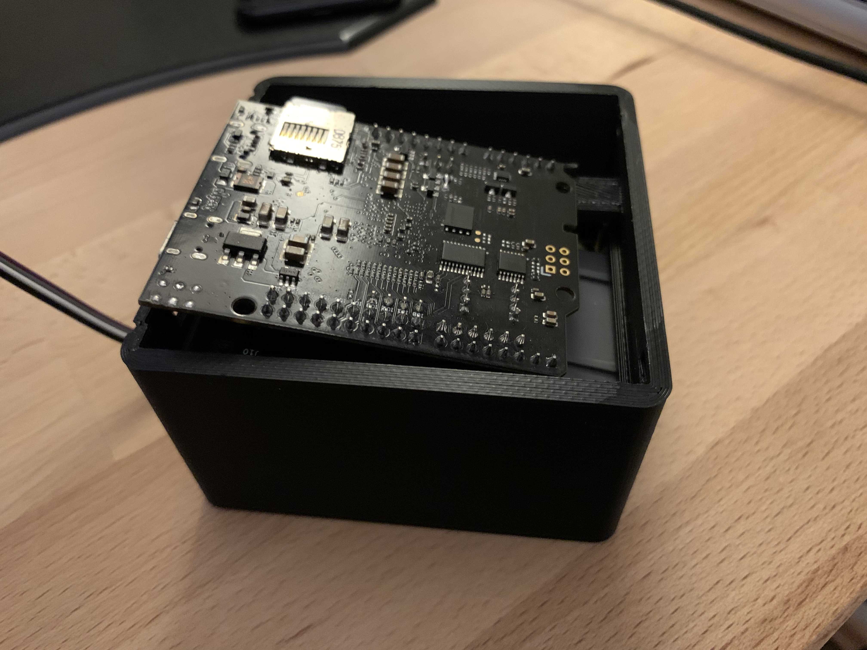
static/wiki/case_sp/case_shield_1.jpg
