gbaHD/GBAHD-Shield/static/wiki/case_sp/case_sp_seated.jpg

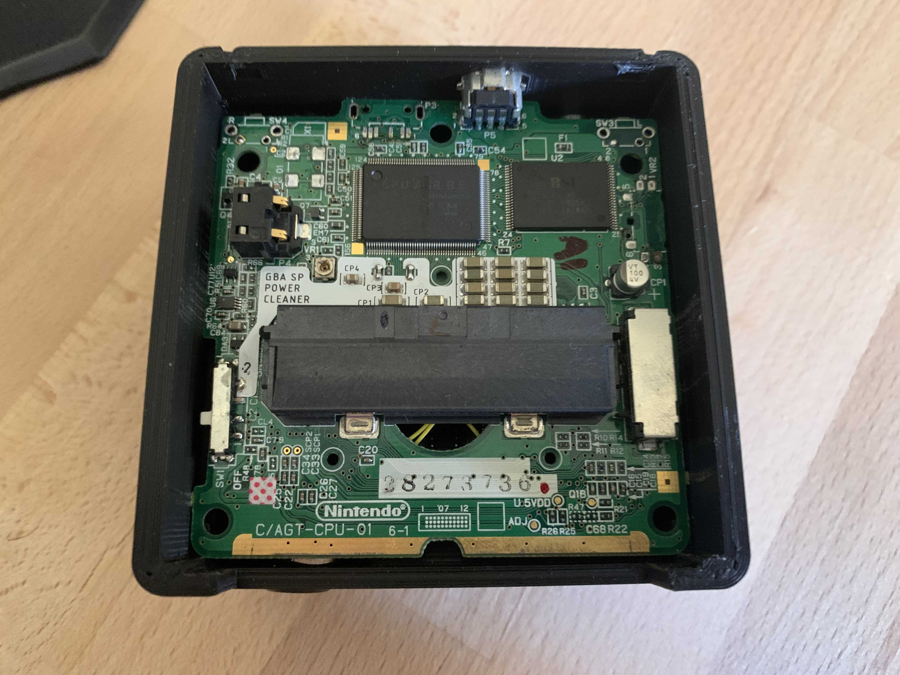
static/wiki/case_sp/case_sp_seated.jpg
