gbaHD/GBAHD-Shield/static/wiki/case_sp/p35-gnd-audio.jpg

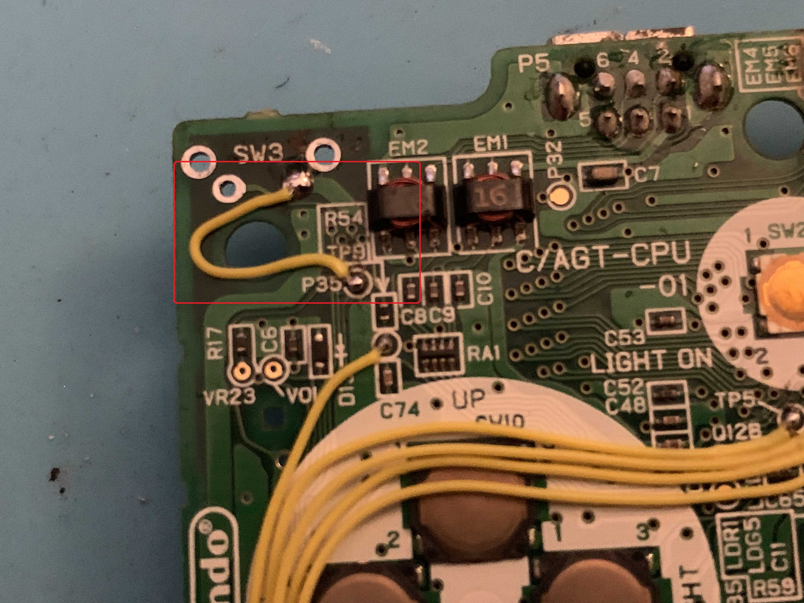
static/wiki/case_sp/p35-gnd-audio.jpg
