gbaHD/GBAHD-Shield/static/wiki/case_sp/sp_audio35.jpg

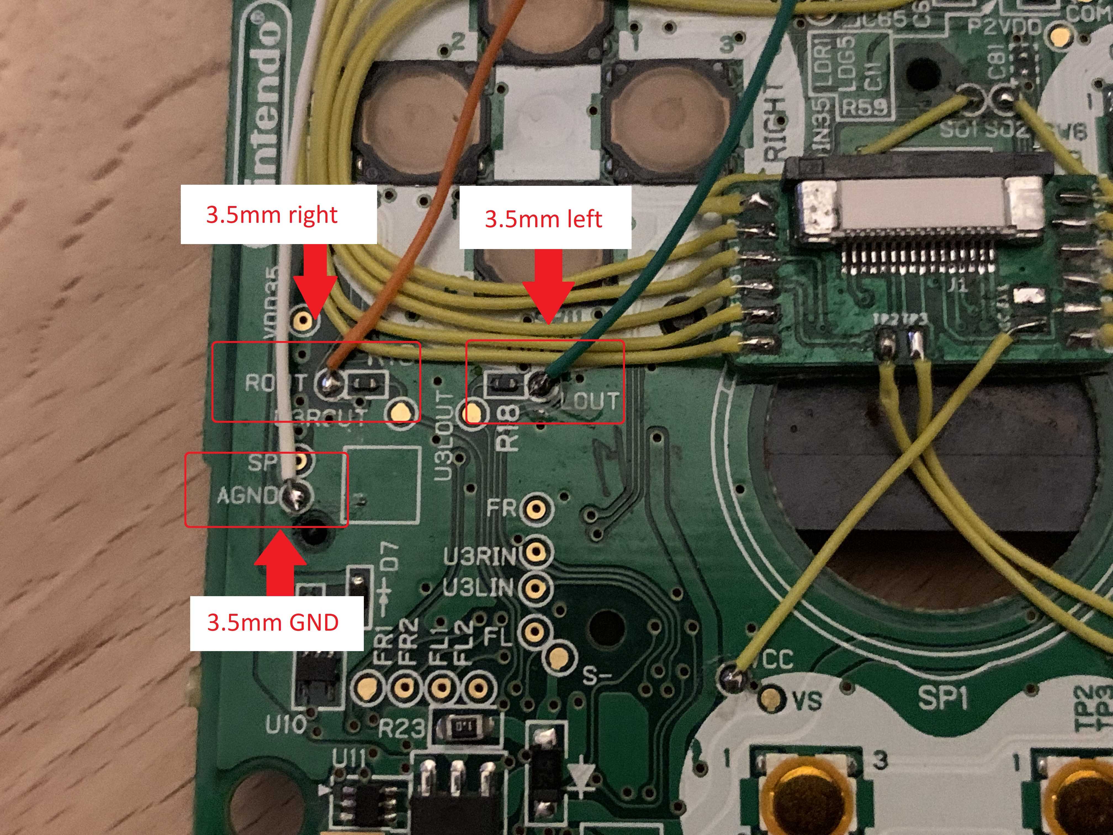
static/wiki/case_sp/sp_audio35.jpg
