gbaHD/GBAHD-Shield/static/wiki/case_sp/sp_charging-port-removed.jpg

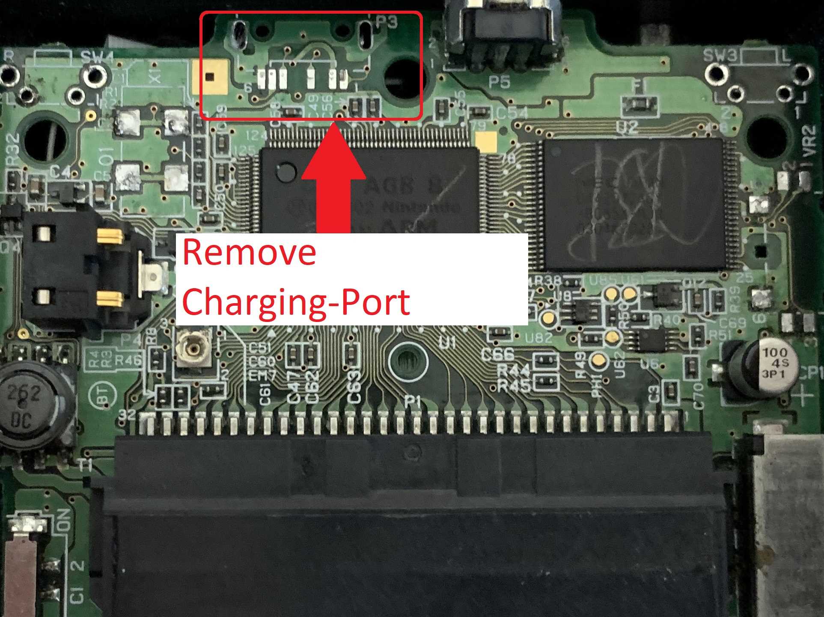
static/wiki/case_sp/sp_charging-port-removed.jpg
