gbaHD/GBAHD-Shield/static/wiki/case_sp/sp_power-cleaner.jpg

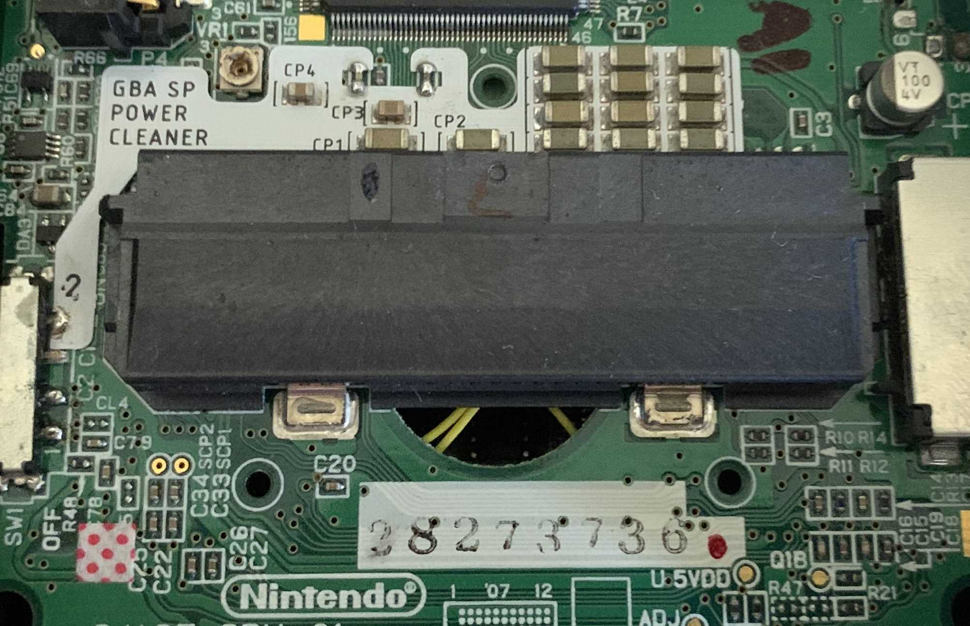
static/wiki/case_sp/sp_power-cleaner.jpg
