gbaHD/GBAHD-Shield/static/wiki/case_sp/sp_volumeslider_removed.jpg

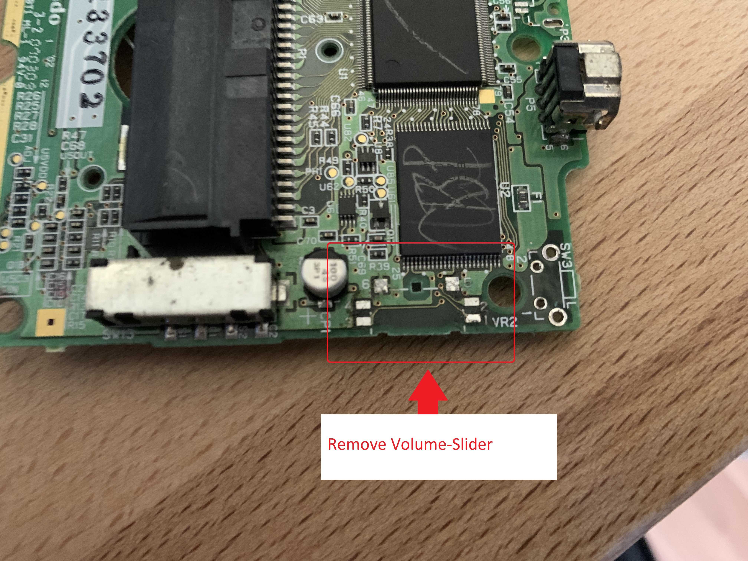
static/wiki/case_sp/sp_volumeslider_removed.jpg
