gbaHD/GBAHD-Shield/static/wiki/case_sp/spartan_wires_switch.jpg

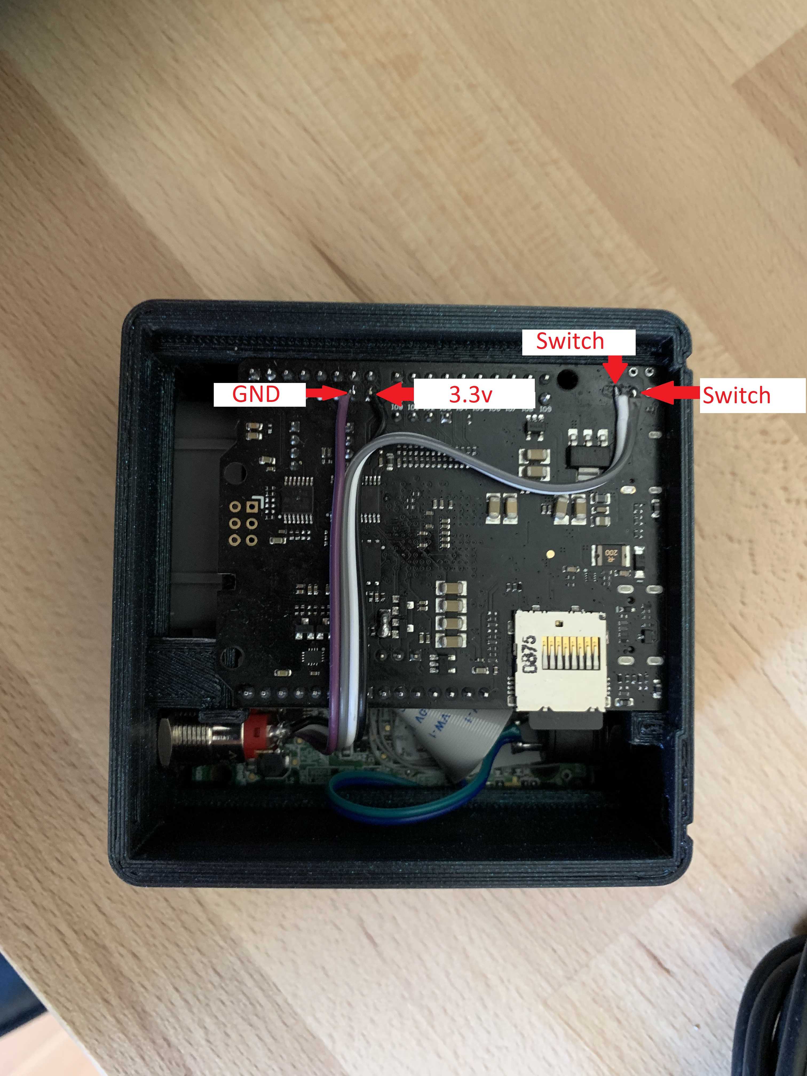
static/wiki/case_sp/spartan_wires_switch.jpg
