gbaHD/GBAHD-Shield/static/wiki/case_sp/switch-reset.jpg

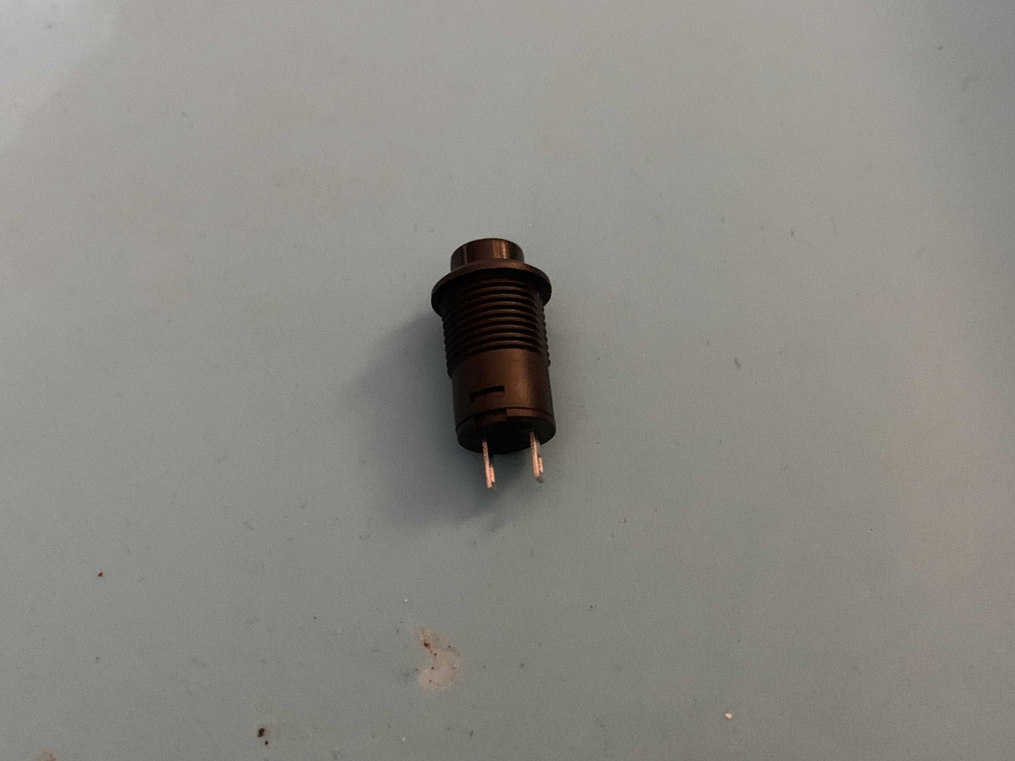
static/wiki/case_sp/switch-reset.jpg
