gbaHD/GBAHD-Shield/static/wiki/case_sp/switch_connections.jpg

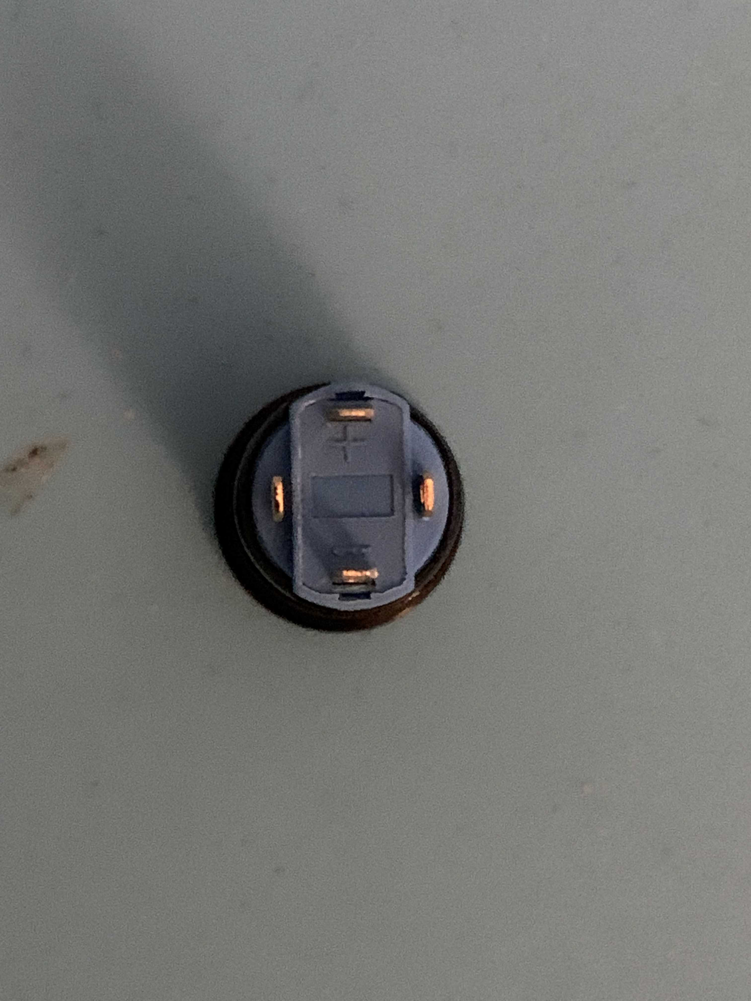
static/wiki/case_sp/switch_connections.jpg
