gbaHD/GBAHD-Shield/static/wiki/case_sp/switch_led.jpg

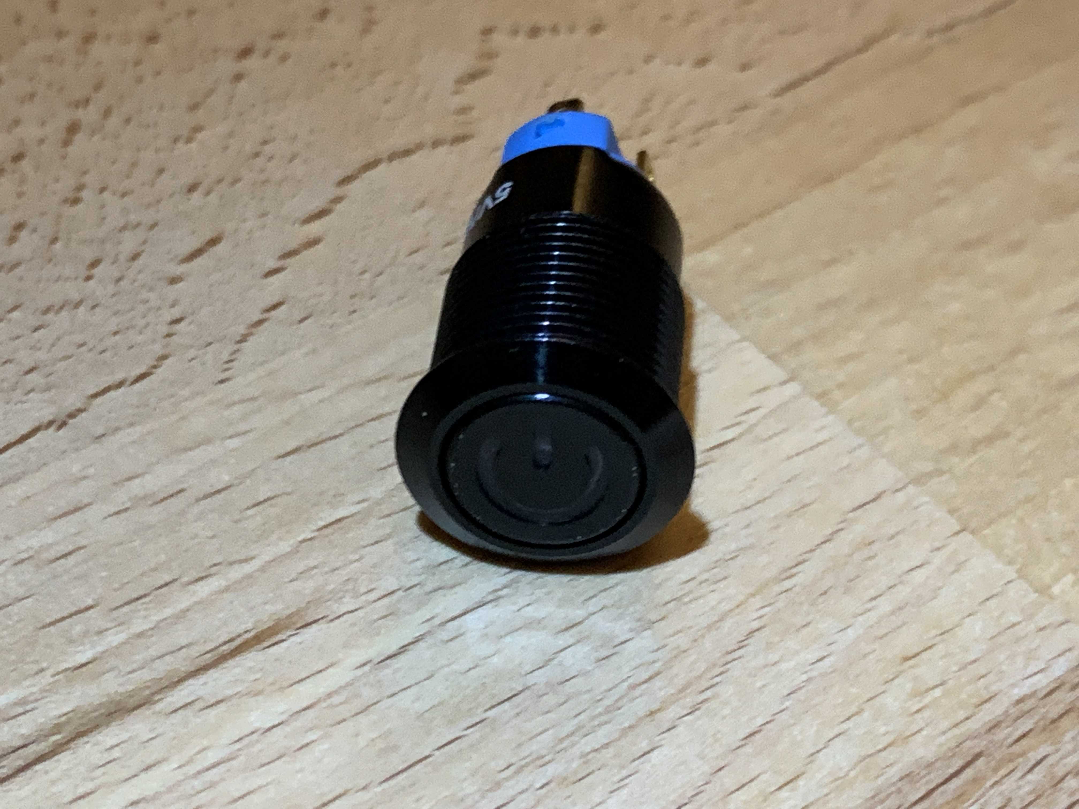
static/wiki/case_sp/switch_led.jpg
