gbaHD/GBAHD-Shield/static/wiki/cases/ogba/obga-case_2.jpg

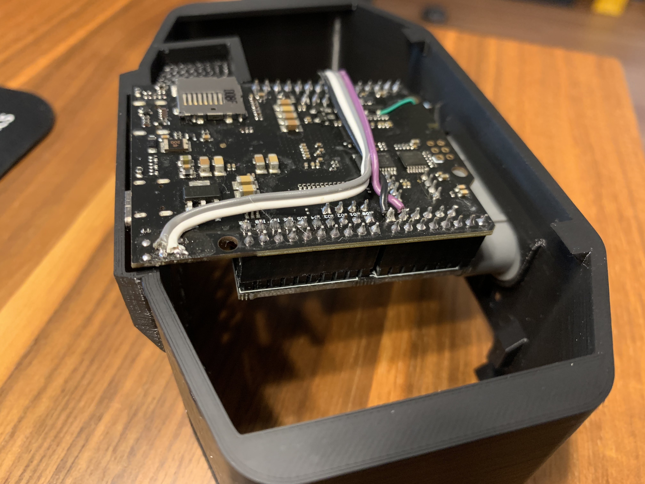
static/wiki/cases/ogba/obga-case_2.jpg
