gbaHD/GBAHD-Shield/static/wiki/cases/ogba/obga-case_3.jpg

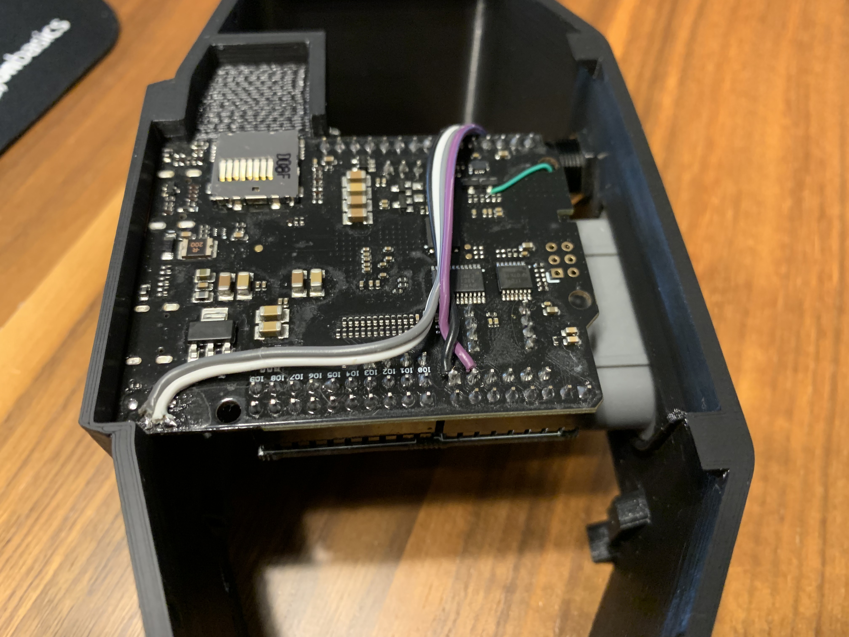
static/wiki/cases/ogba/obga-case_3.jpg
