gbaHD/GBAHD-Shield/static/wiki/cases/ogba/obga-case_4.jpg

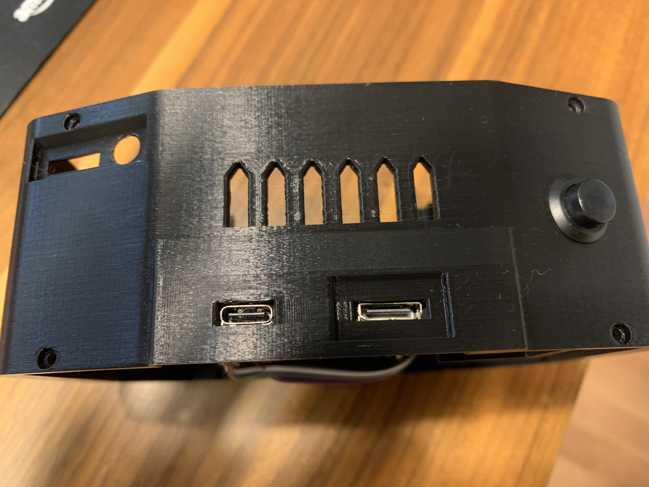
static/wiki/cases/ogba/obga-case_4.jpg
