gbaHD/GBAHD-Shield/static/wiki/cases/ogba/obga-case_5.jpg

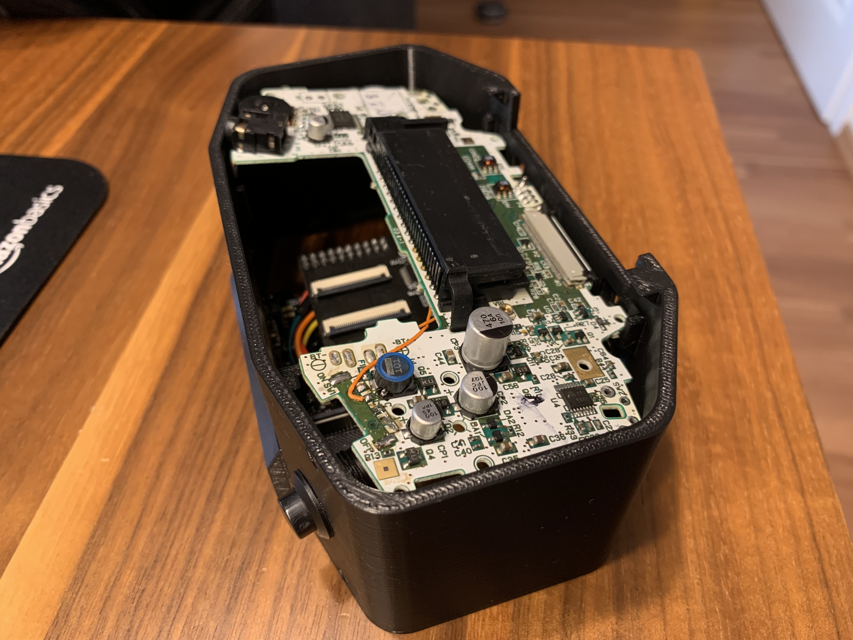
static/wiki/cases/ogba/obga-case_5.jpg
