gbaHD/GBAHD-Shield/static/wiki/cases/ogba/obga-case_6.jpg

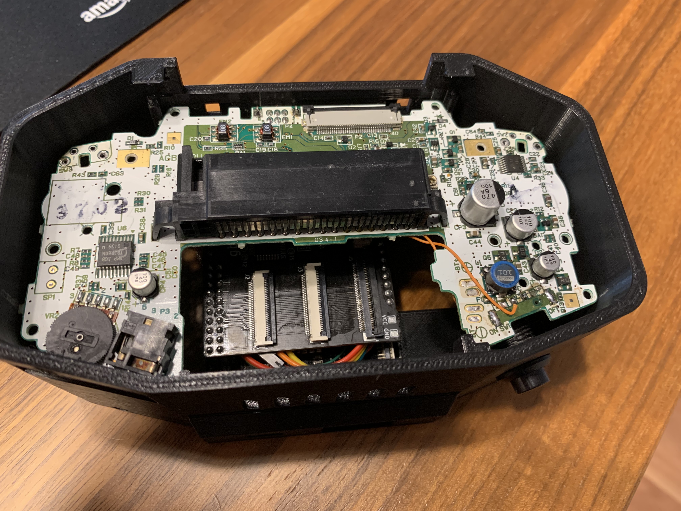
static/wiki/cases/ogba/obga-case_6.jpg
