gbaHD/GBAHD-Shield/static/wiki/cases/ogba/obga-case_7.jpg

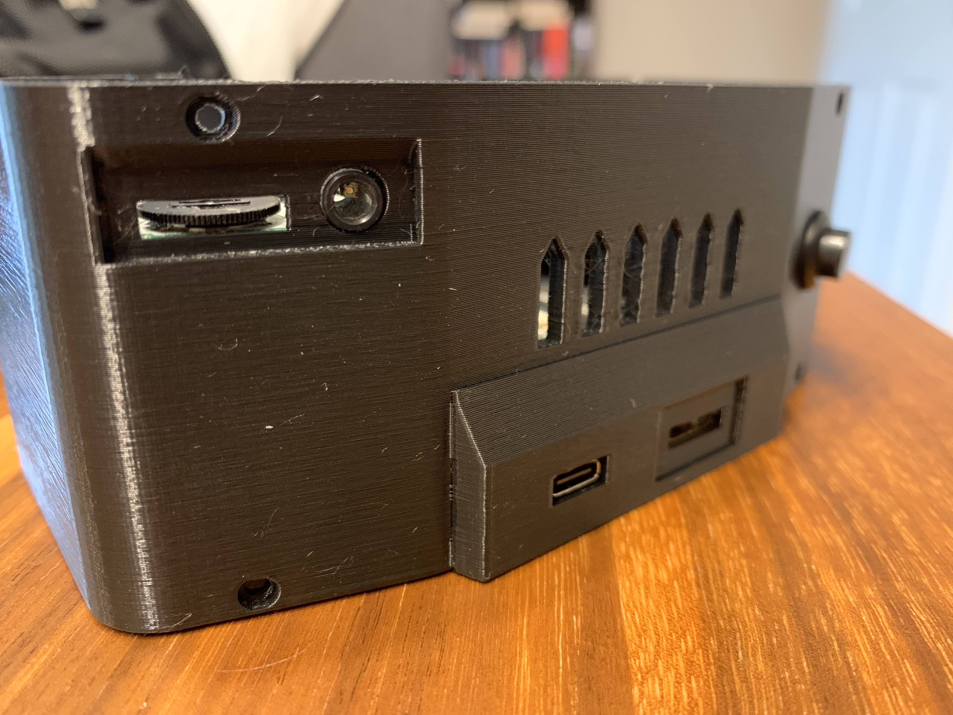
static/wiki/cases/ogba/obga-case_7.jpg
