gbaHD/GBAHD-Shield/static/wiki/cases/ogba/obga-case_8.jpg

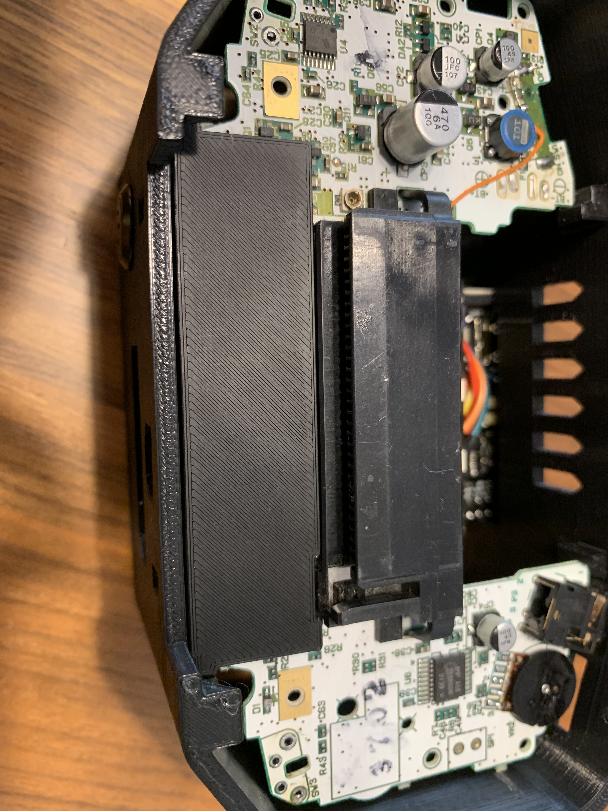
static/wiki/cases/ogba/obga-case_8.jpg
