gbaHD/GBAHD-Shield/static/wiki/cases/ogba/obga-case_9.jpg

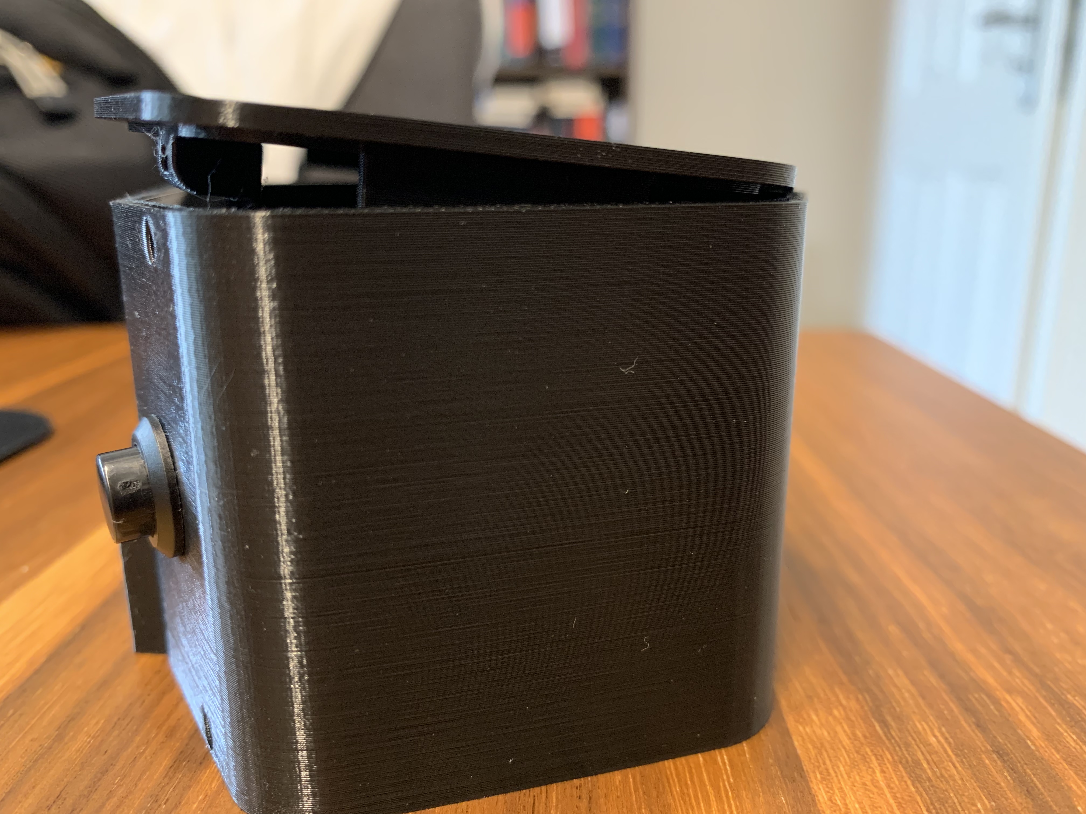
static/wiki/cases/ogba/obga-case_9.jpg
