gbaHD/GBAHD-Shield/static/wiki/cases/ogba/obga-case_10.jpg

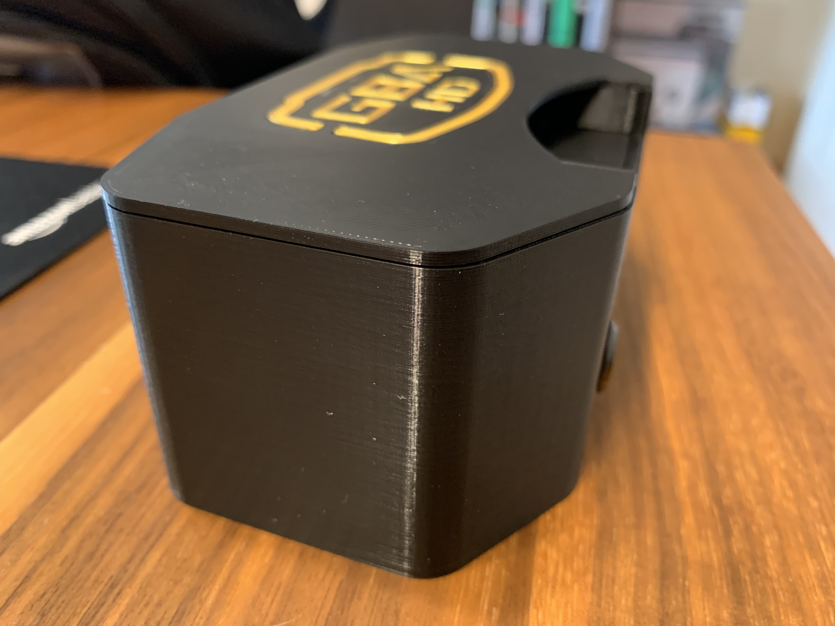
static/wiki/cases/ogba/obga-case_10.jpg
