gbaHD/GBAHD-Shield/static/wiki/cases/ogba/obga-case_11.jpg

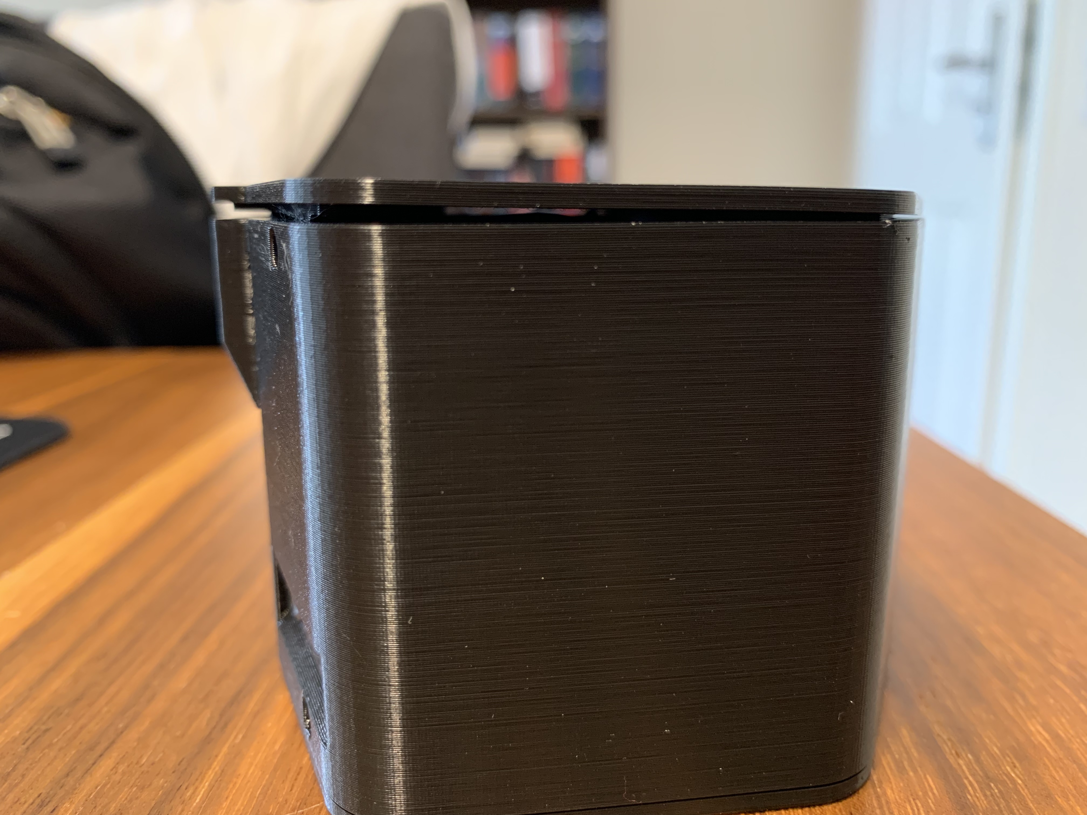
static/wiki/cases/ogba/obga-case_11.jpg
