gbaHD/GBAHD-Shield/static/wiki/cases/sp/sp-case_1.jpg

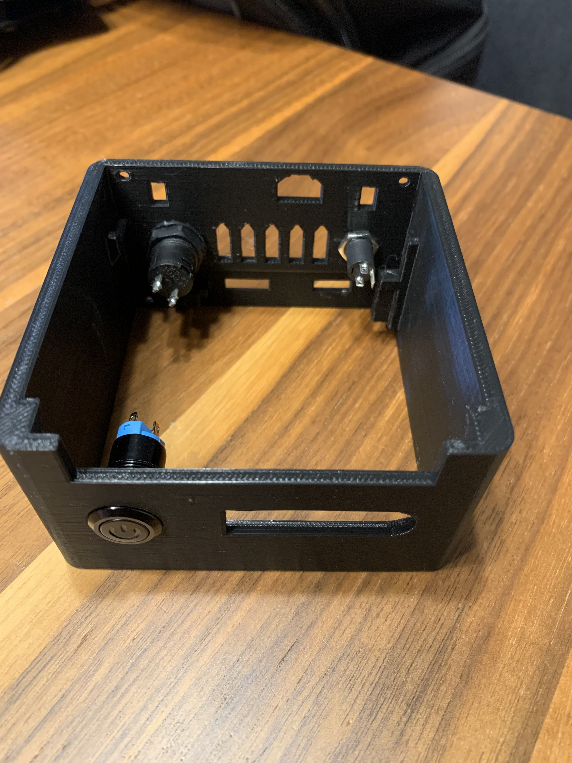
static/wiki/cases/sp/sp-case_1.jpg
