gbaHD/GBAHD-Shield/static/wiki/cases/sp/sp-case_1_2.jpg

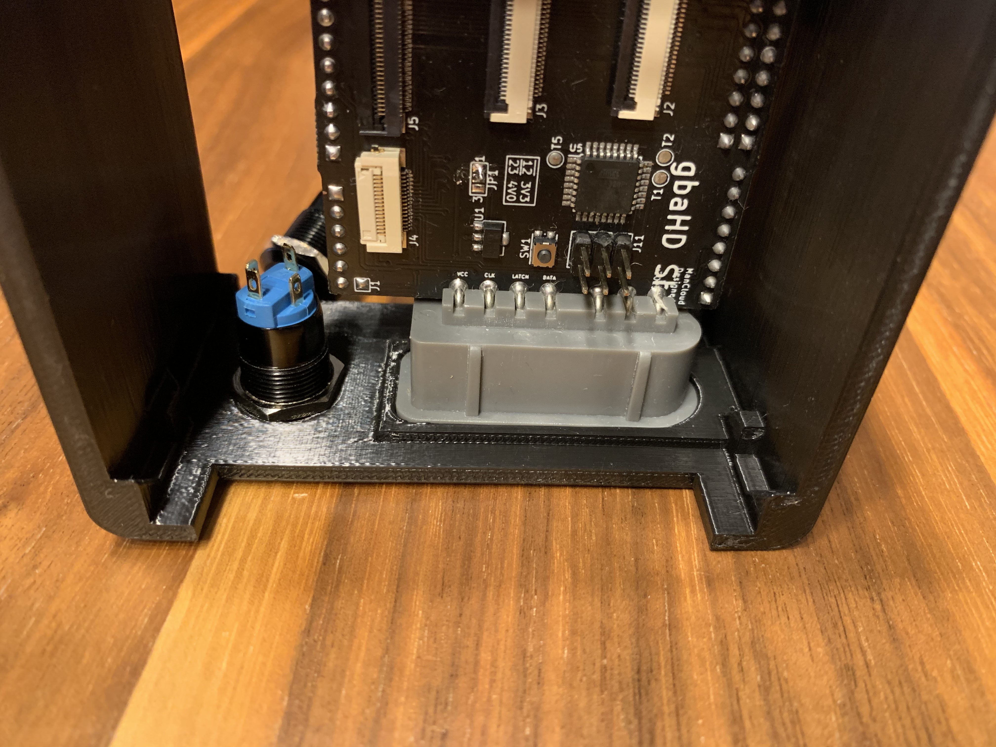
static/wiki/cases/sp/sp-case_1_2.jpg
