gbaHD/GBAHD-Shield/static/wiki/cases/sp/sp-case_2.jpg

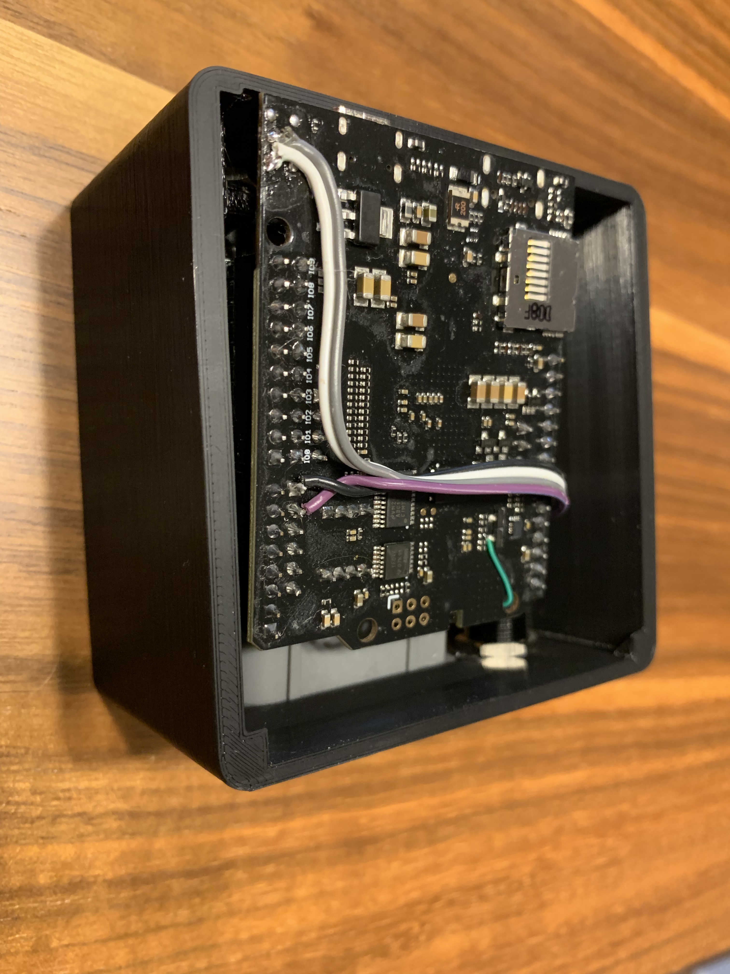
static/wiki/cases/sp/sp-case_2.jpg
