gbaHD/GBAHD-Shield/static/wiki/cases/sp/sp-case_3.jpg

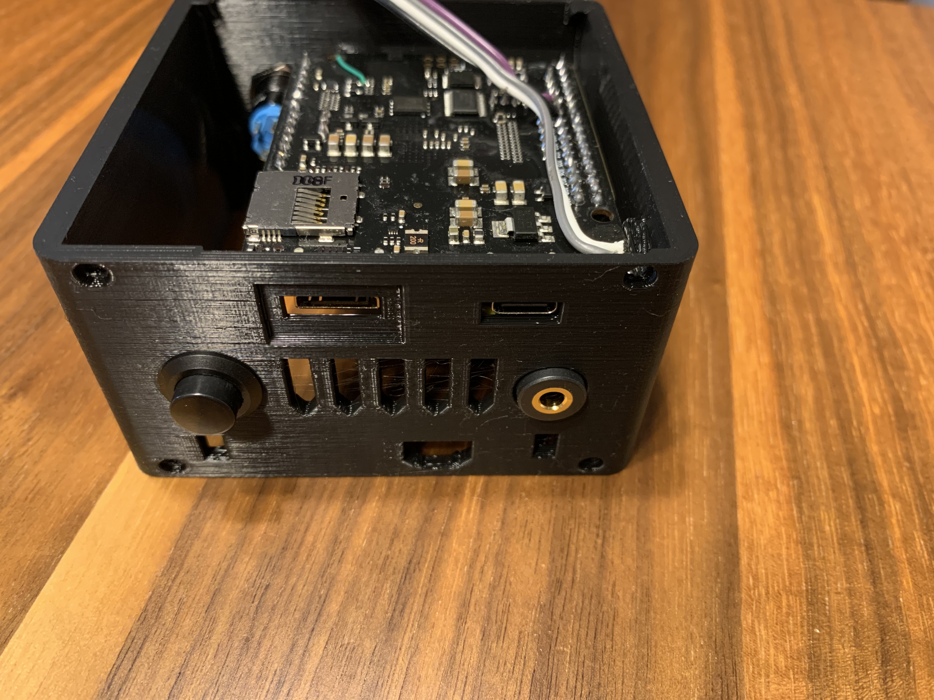
static/wiki/cases/sp/sp-case_3.jpg
