gbaHD/GBAHD-Shield/static/wiki/cases/sp/sp-case_4.jpg

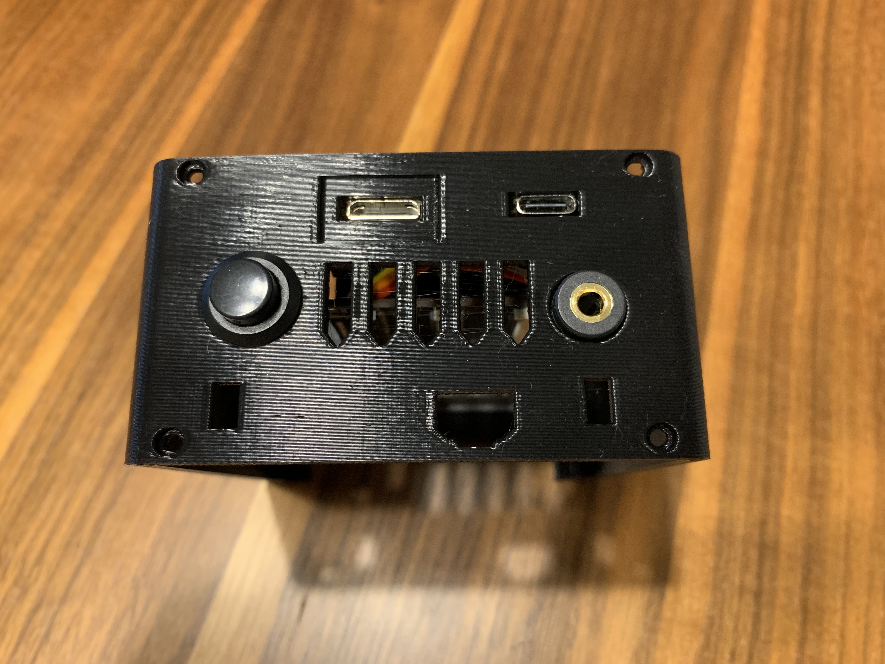
static/wiki/cases/sp/sp-case_4.jpg
