gbaHD/GBAHD-Shield/static/wiki/cases/sp/sp-case_6.jpg

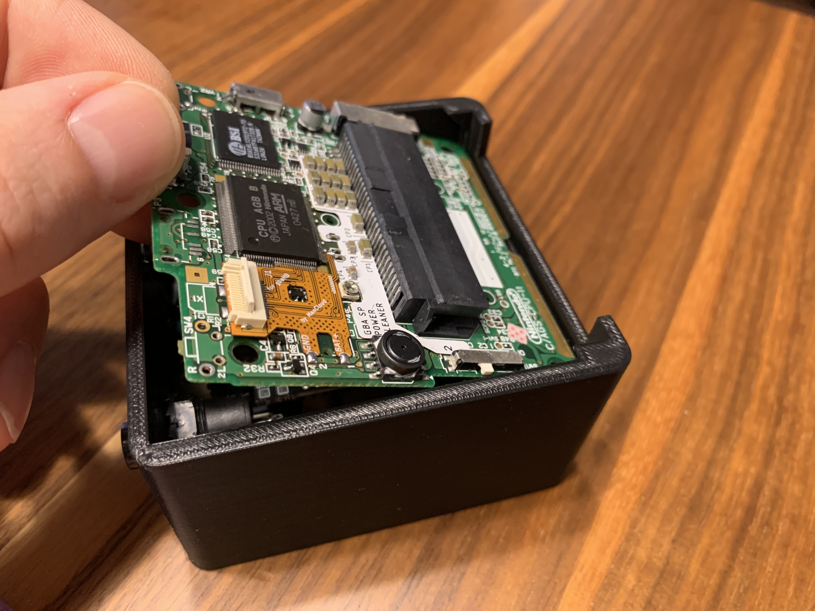
static/wiki/cases/sp/sp-case_6.jpg
