gbaHD/GBAHD-Shield/static/wiki/cases/sp/sp-case_7.jpg

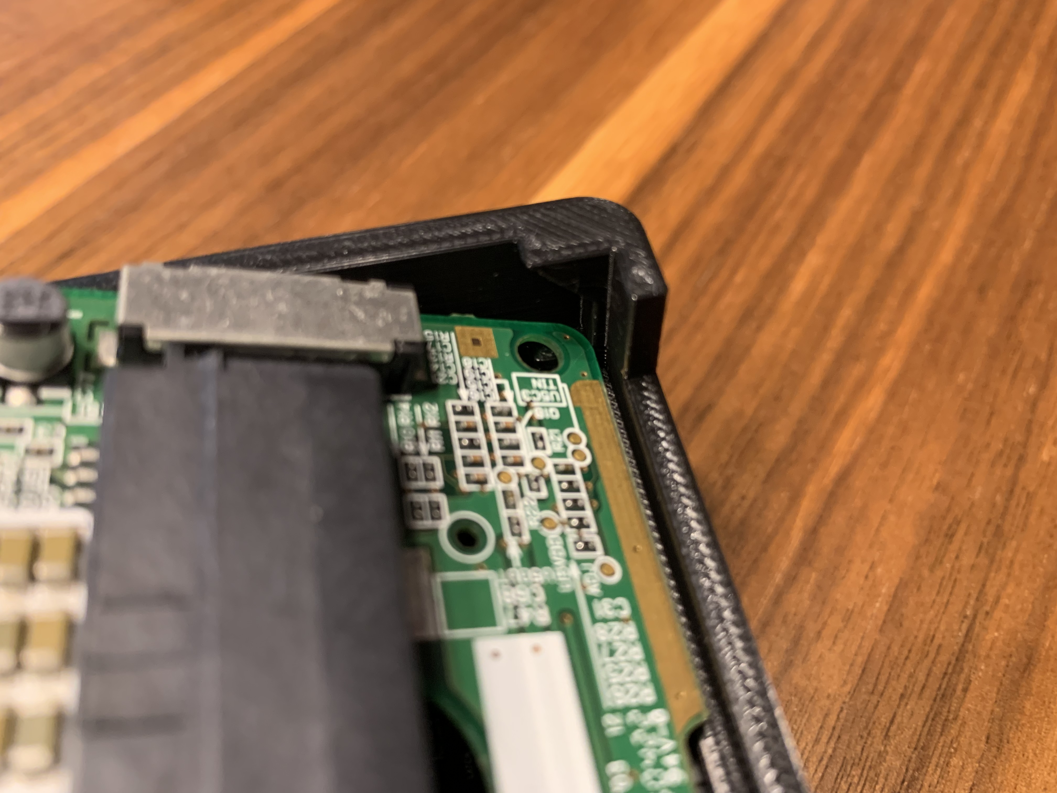
static/wiki/cases/sp/sp-case_7.jpg
