gbaHD/GBAHD-Shield/static/wiki/cases/sp/sp-case_8.jpg

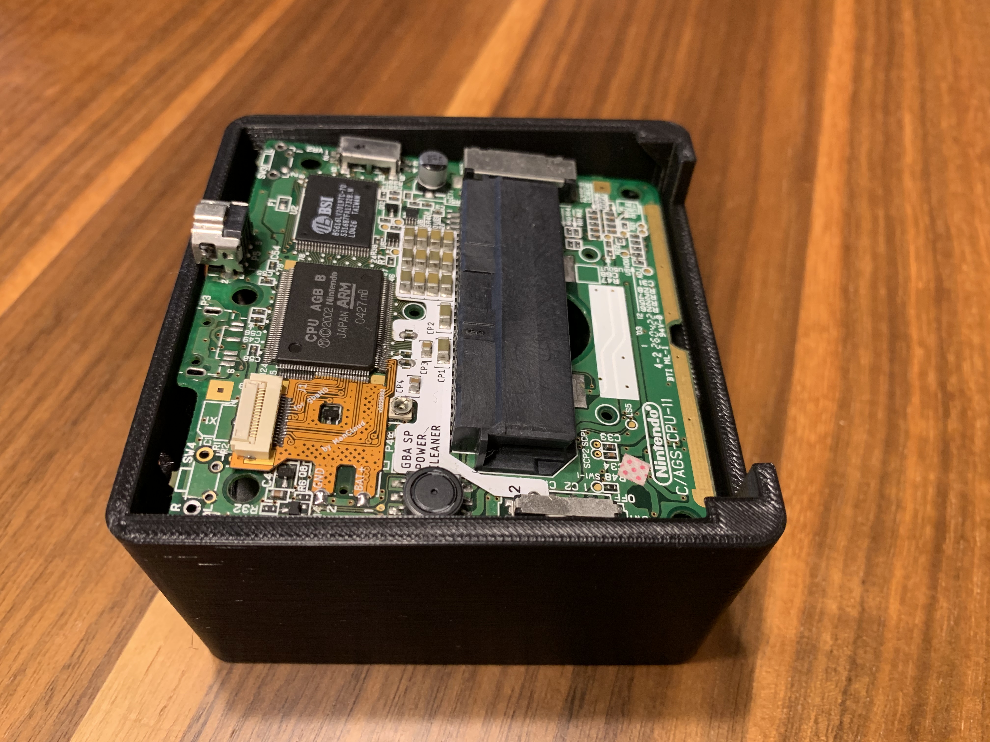
static/wiki/cases/sp/sp-case_8.jpg
