gbaHD/GBAHD-Shield/static/wiki/cases/sp/sp-case_9.jpg

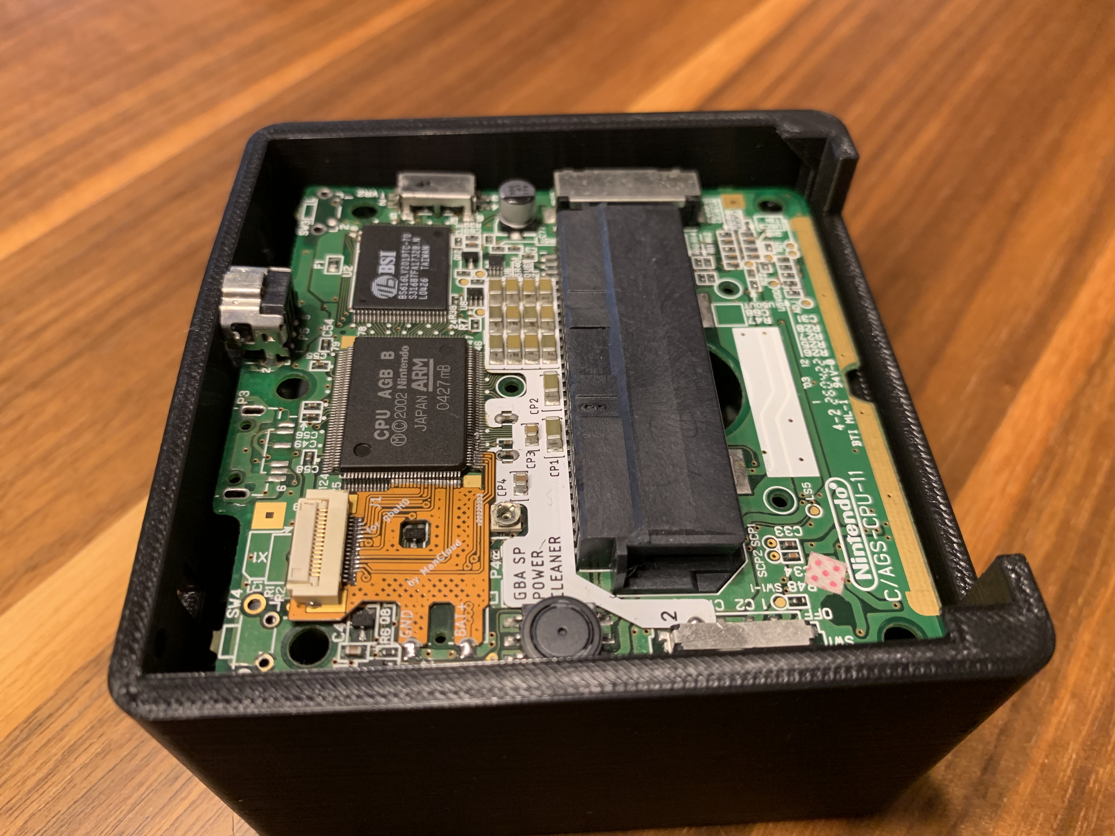
static/wiki/cases/sp/sp-case_9.jpg
