gbaHD/GBAHD-Shield/static/wiki/cases/sp/sp-case_10.jpg

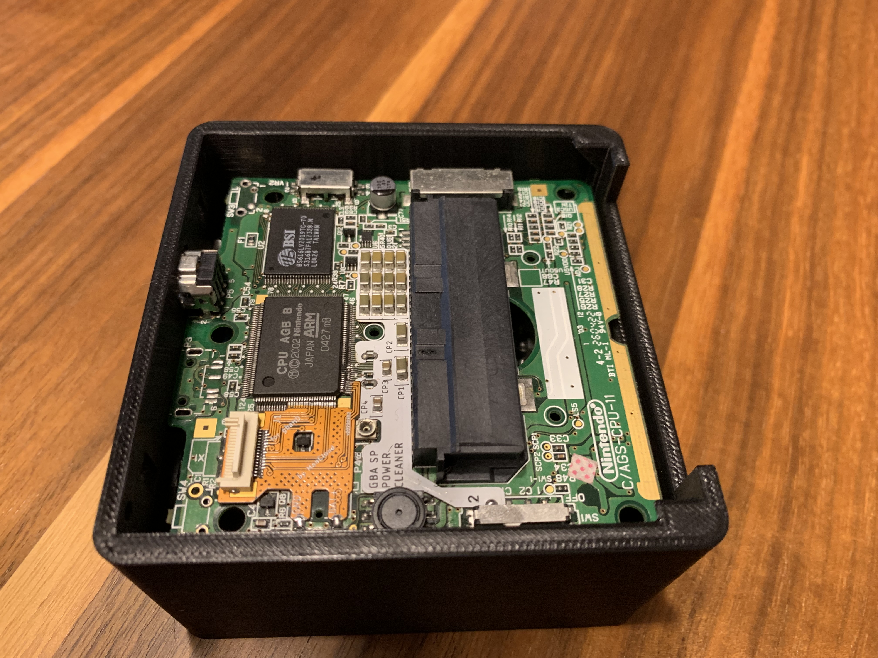
static/wiki/cases/sp/sp-case_10.jpg
