gbaHD/GBAHD-Shield/static/wiki/cases/sp/sp-case_11.jpg

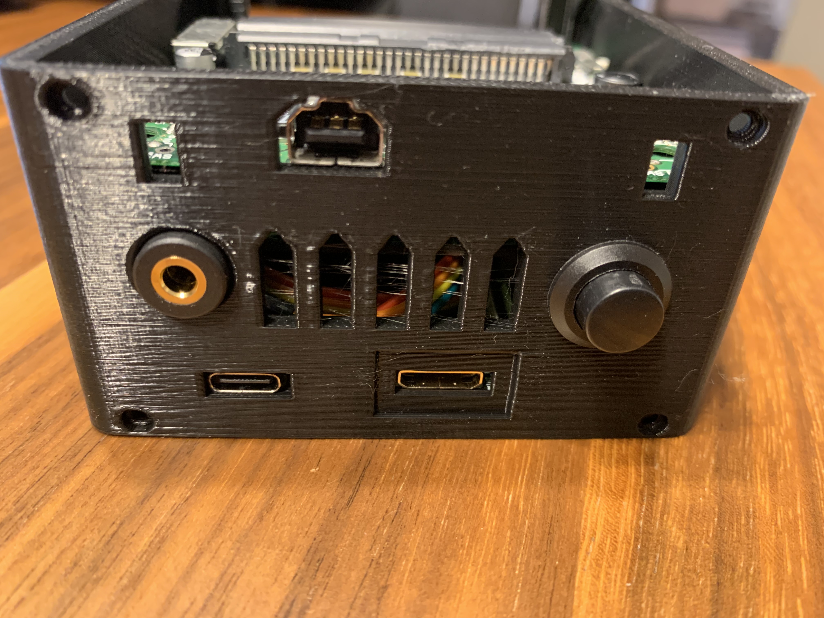
static/wiki/cases/sp/sp-case_11.jpg
