gbaHD/GBAHD-Shield/static/wiki/cases/sp/sp-case_12.jpg

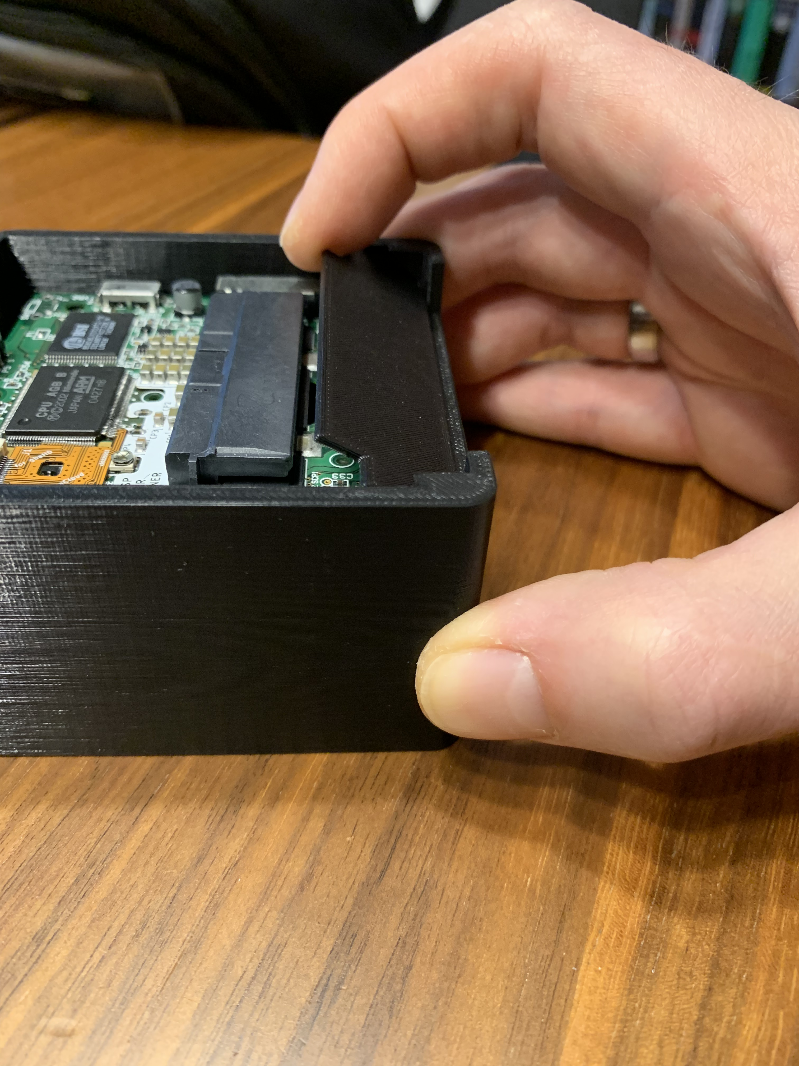
static/wiki/cases/sp/sp-case_12.jpg
