gbaHD/GBAHD-Shield/static/wiki/cases/sp/sp-case_13.jpg

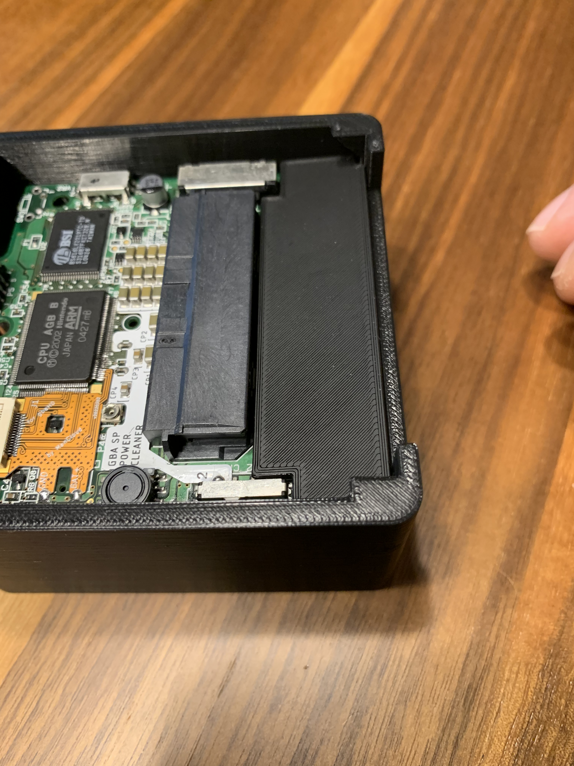
static/wiki/cases/sp/sp-case_13.jpg
