gbaHD/GBAHD-Shield/static/wiki/cases/sp/sp-case_14.jpg

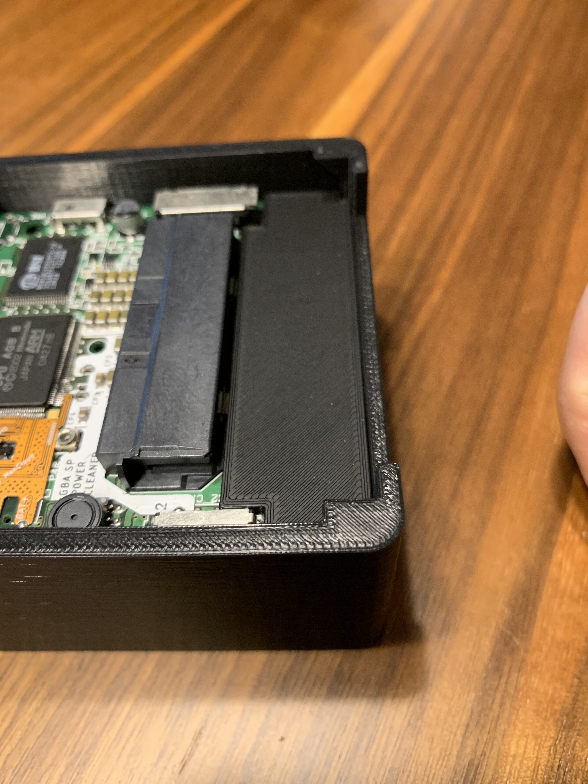
static/wiki/cases/sp/sp-case_14.jpg
