gbaHD/GBAHD-Shield/static/wiki/cases/sp/sp-case_15.jpg

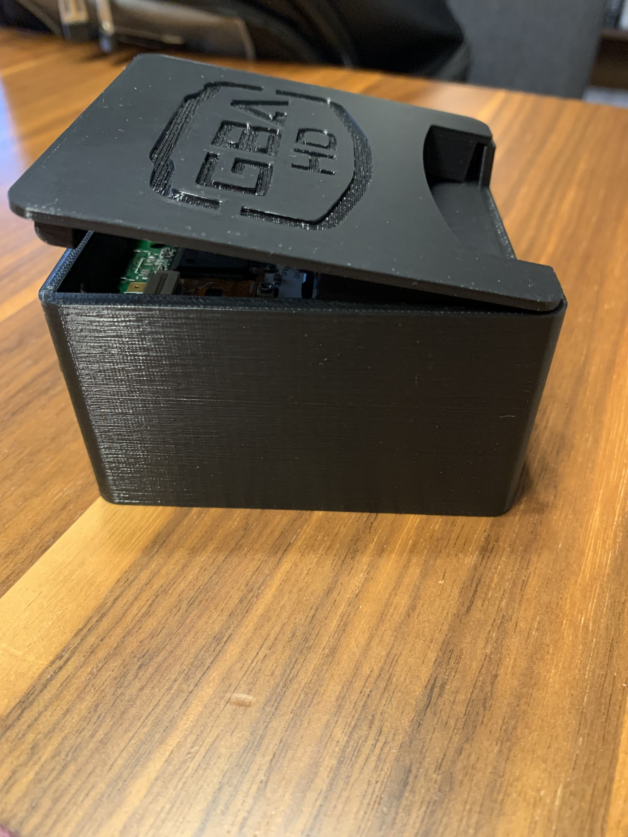
static/wiki/cases/sp/sp-case_15.jpg
