gbaHD/GBAHD-Shield/static/wiki/cases/sp/sp-case_16.jpg

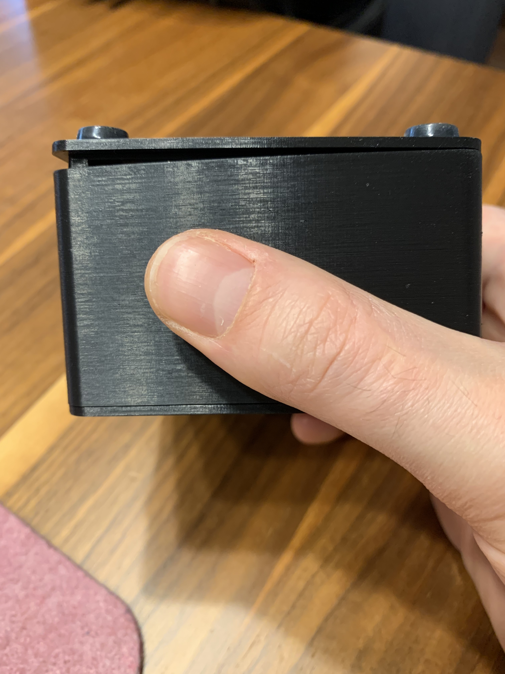
static/wiki/cases/sp/sp-case_16.jpg
