gbaHD/GBAHD-Shield/static/wiki/cases/sp/sp-case_17.jpg

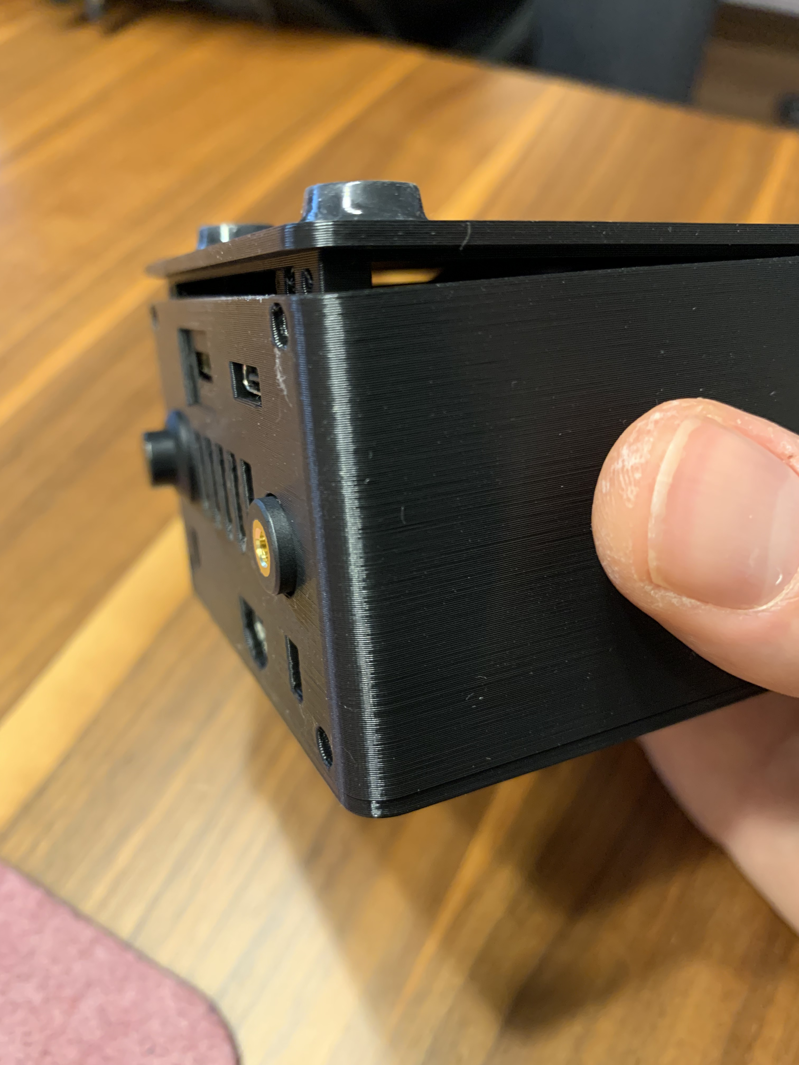
static/wiki/cases/sp/sp-case_17.jpg
