gbaHD/GBAHD-Shield/static/wiki/cases/sp/sp-case_18.jpg

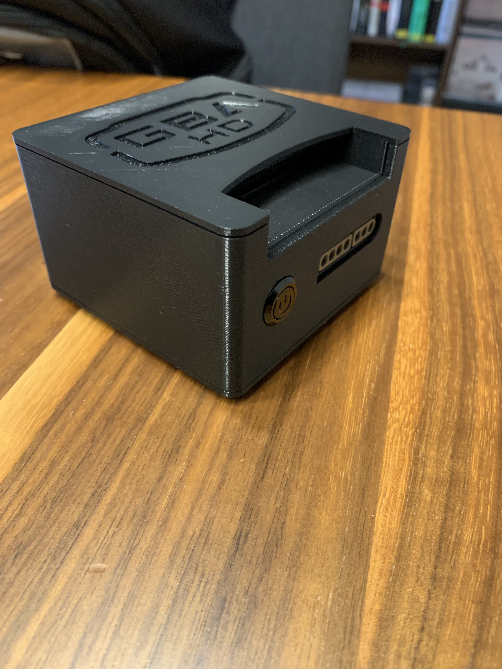
static/wiki/cases/sp/sp-case_18.jpg
