gbaHD/GBAHD-Shield/static/wiki/cp2101-programmer.jpg

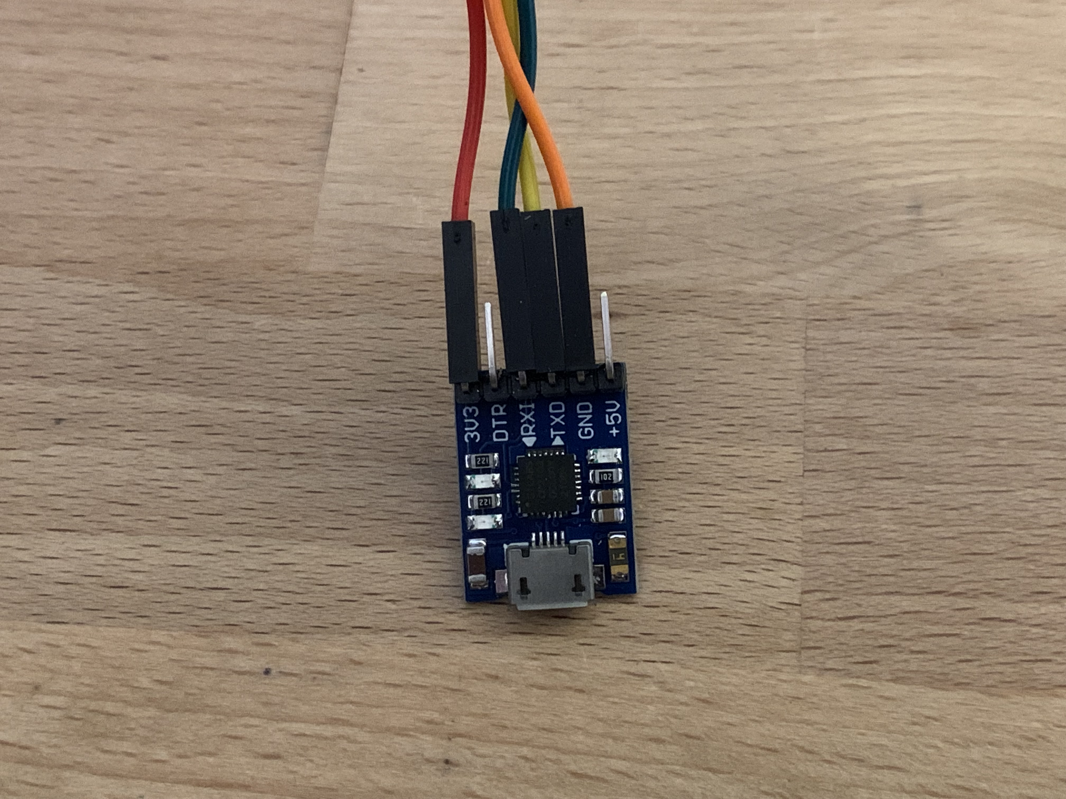
static/wiki/cp2101-programmer.jpg
