gbaHD/GBAHD-Shield/static/wiki/cp2102_RXD.png

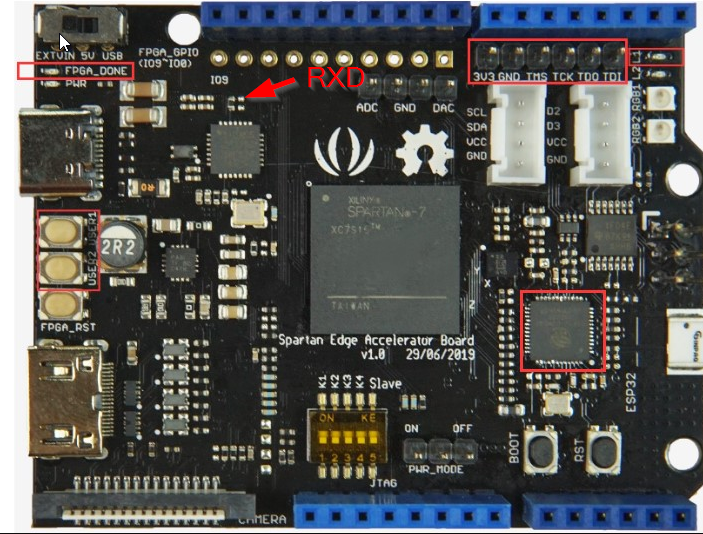
static/wiki/cp2102_RXD.png
