gbaHD/GBAHD-Shield/static/wiki/cp2102_TXD.png

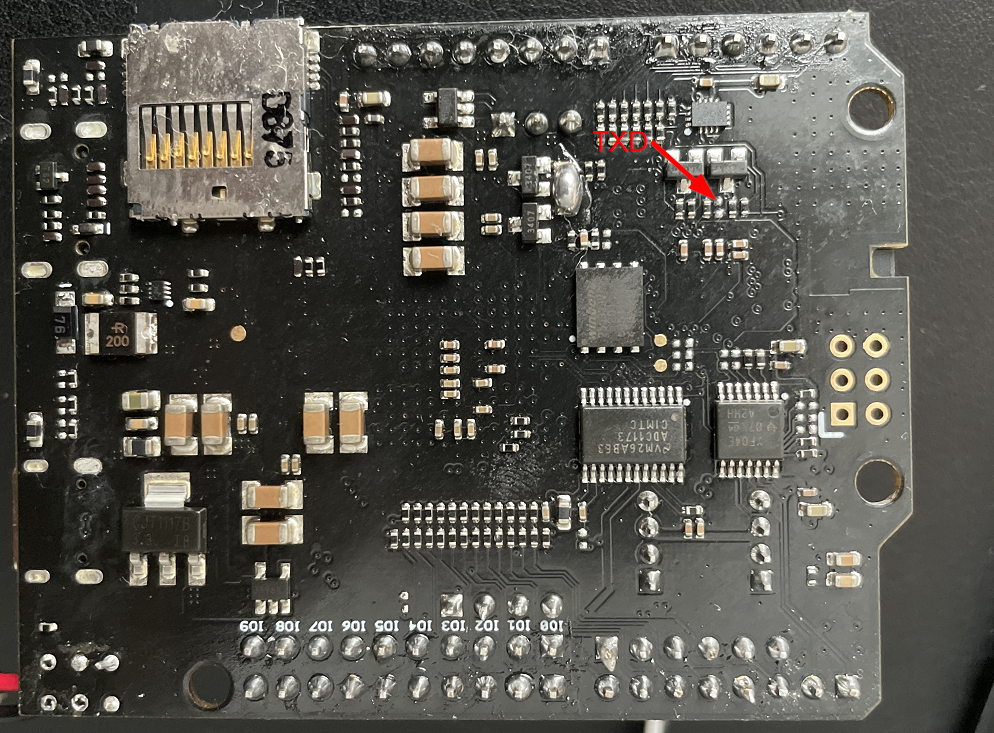
static/wiki/cp2102_TXD.png
