gbaHD/GBAHD-Shield/static/wiki/defaultbitstream.JPG

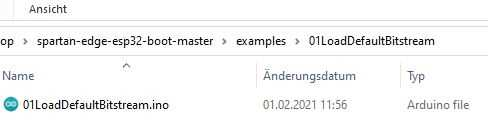
static/wiki/defaultbitstream.JPG
