gbaHD/GBAHD-Shield/static/wiki/devicemanager.png

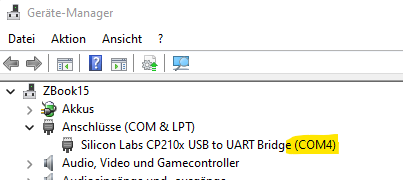
static/wiki/devicemanager.png
