gbaHD/GBAHD-Shield/static/wiki/esp32arduino.JPG

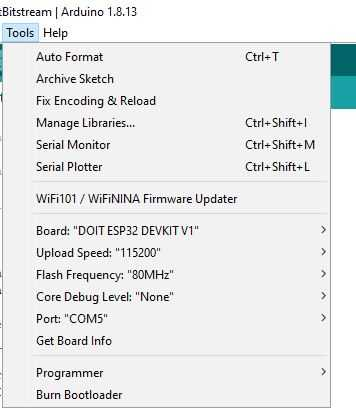
static/wiki/esp32arduino.JPG
