gbaHD/GBAHD-Shield/static/wiki/esptool-upload.png

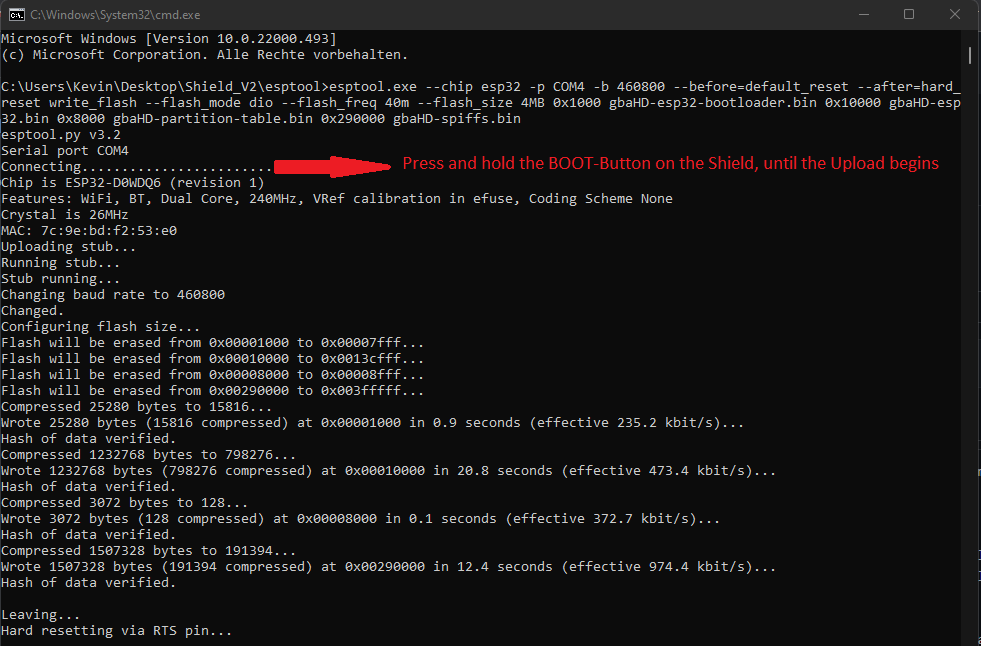
static/wiki/esptool-upload.png
