gbaHD/GBAHD-Shield/static/wiki/esptool-windows1.png

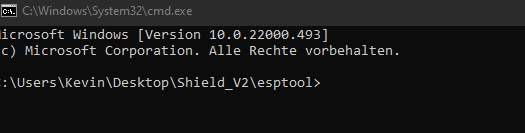
static/wiki/esptool-windows1.png
