gbaHD/GBAHD-Shield/static/wiki/esptool-windows.png

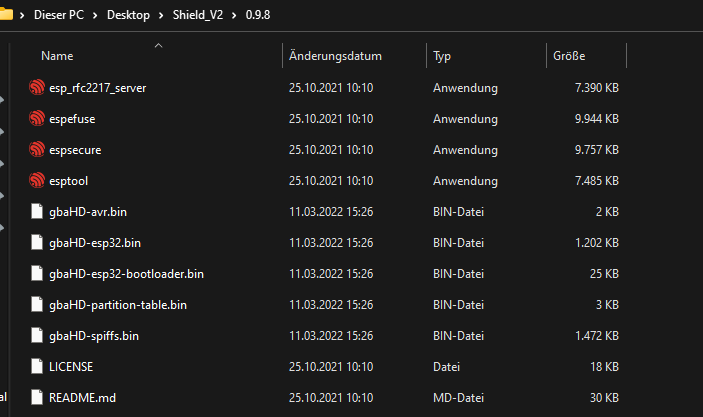
static/wiki/esptool-windows.png
