gbaHD/GBAHD-Shield/static/wiki/GBA_HD_2.jpg

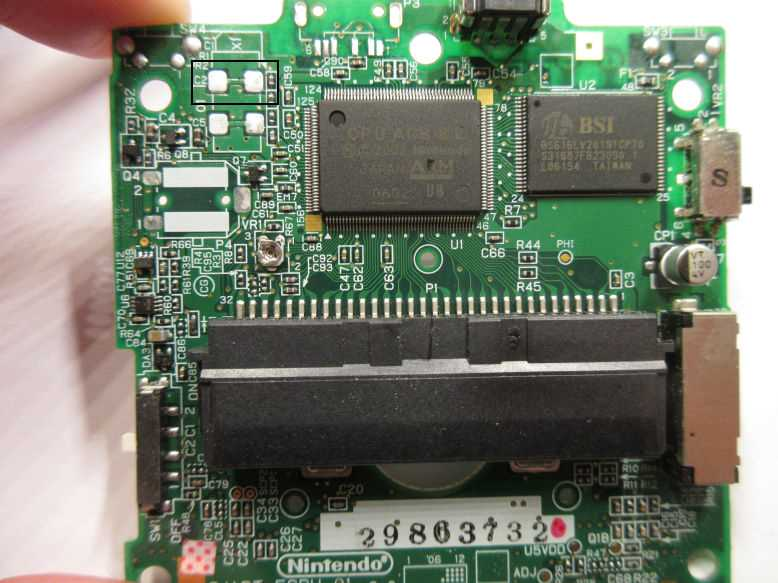
static/wiki/GBA_HD_2.jpg
