gbaHD/GBAHD-Shield/static/wiki/gbahd_io_1.png

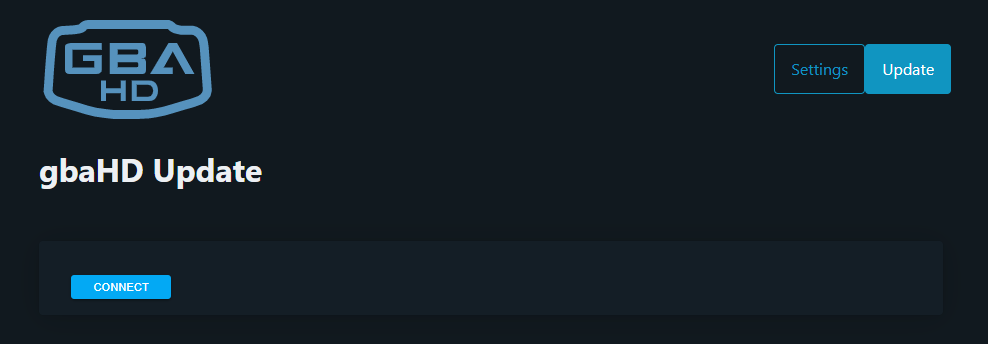
static/wiki/gbahd_io_1.png
