gbaHD/GBAHD-Shield/static/wiki/gbahd_io_3.png

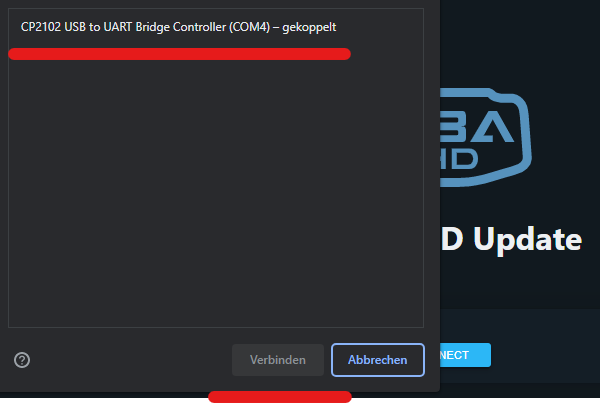
static/wiki/gbahd_io_3.png
