gbaHD/GBAHD-Shield/static/wiki/gbahd_io_4.png

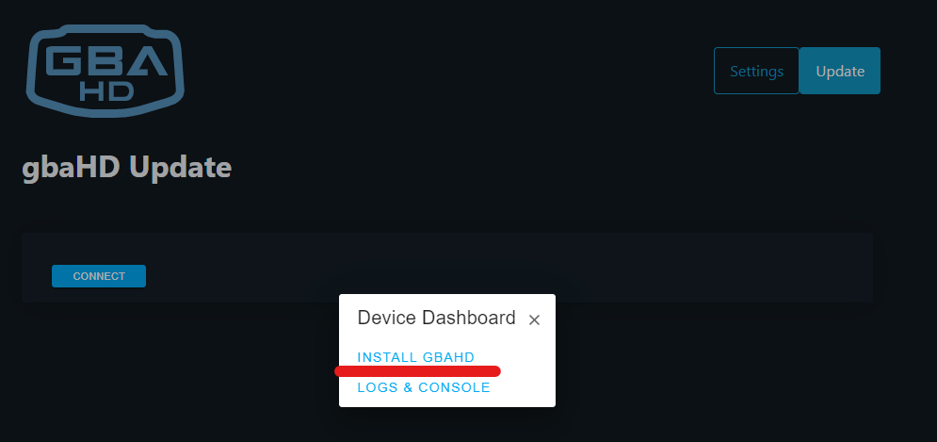
static/wiki/gbahd_io_4.png
