gbaHD/GBAHD-Shield/static/wiki/gbahd_io_5.png

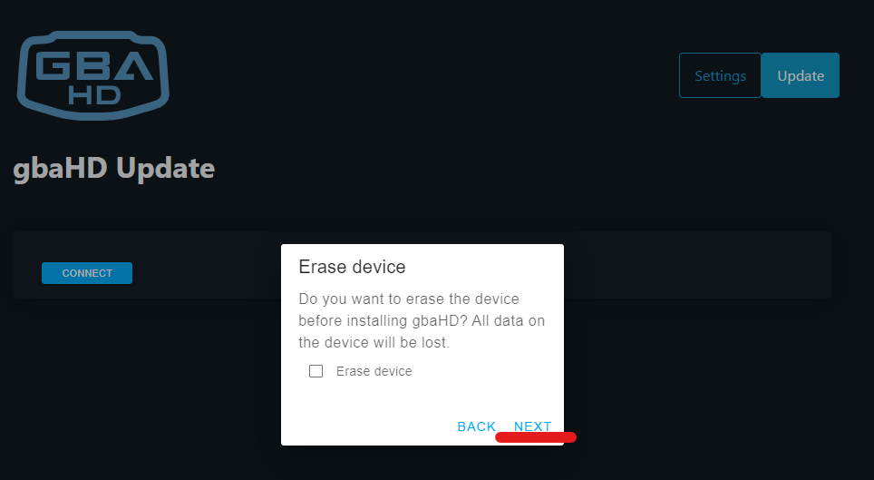
static/wiki/gbahd_io_5.png
