gbaHD/GBAHD-Shield/static/wiki/gbahd_io_6.png

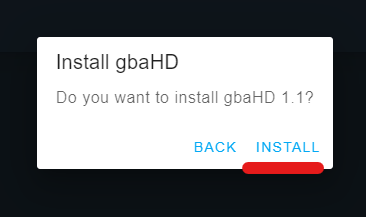
static/wiki/gbahd_io_6.png
