gbaHD/GBAHD-Shield/static/wiki/gbahd_io_7.png

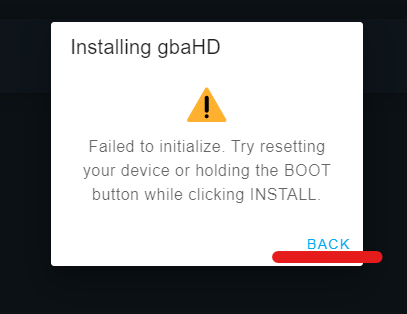
static/wiki/gbahd_io_7.png
