gbaHD/GBAHD-Shield/static/wiki/gbahd_io_8.png

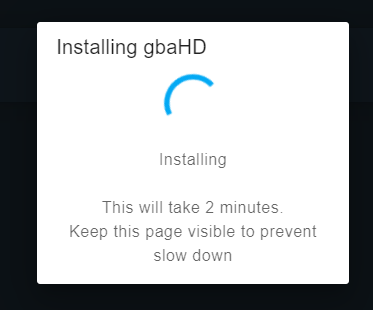
static/wiki/gbahd_io_8.png
