gbaHD/GBAHD-Shield/static/wiki/gbahd_io_9.png

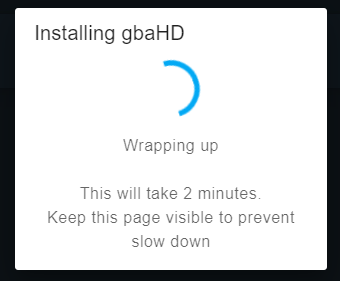
static/wiki/gbahd_io_9.png
