gbaHD/GBAHD-Shield/static/wiki/gbahd_io_10.png

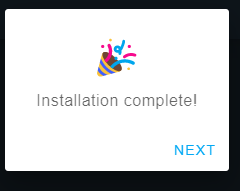
static/wiki/gbahd_io_10.png
