gbaHD/GBAHD-Shield/static/wiki/gbahd_webui_log.png

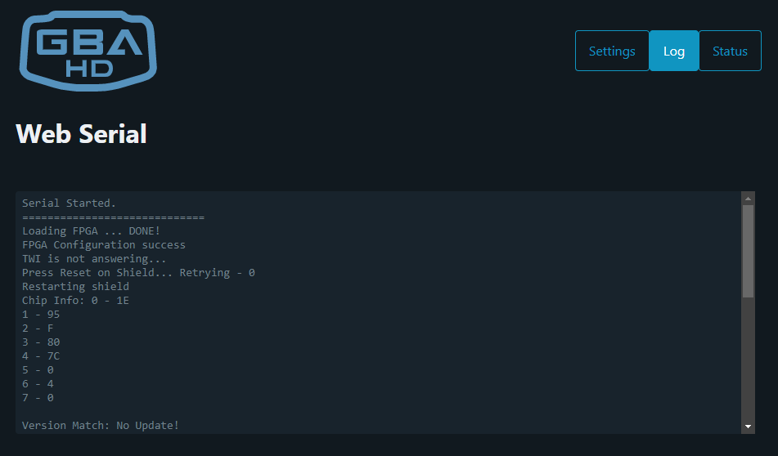
static/wiki/gbahd_webui_log.png
