gbaHD/GBAHD-Shield/static/wiki/gbahd_webui_settings.png

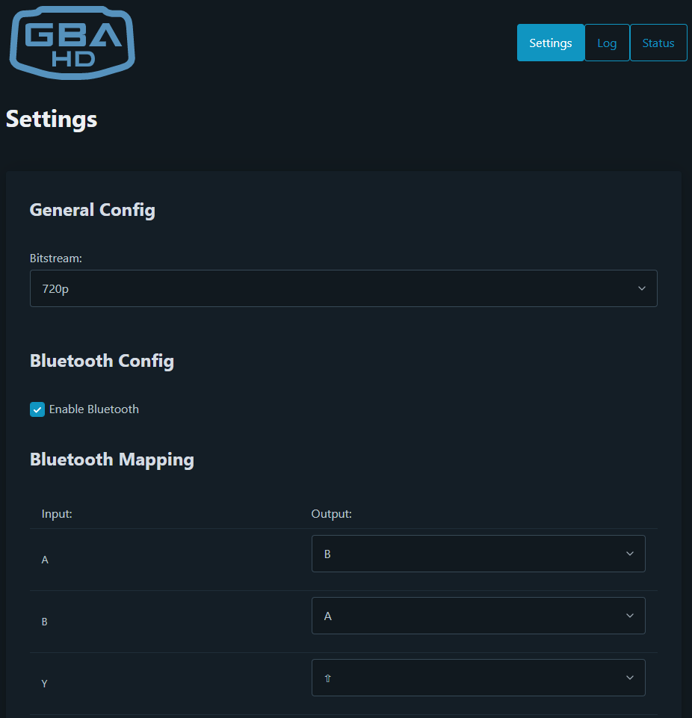
static/wiki/gbahd_webui_settings.png
