gbaHD/GBAHD-Shield/static/wiki/gbahd_webui_startpage.png

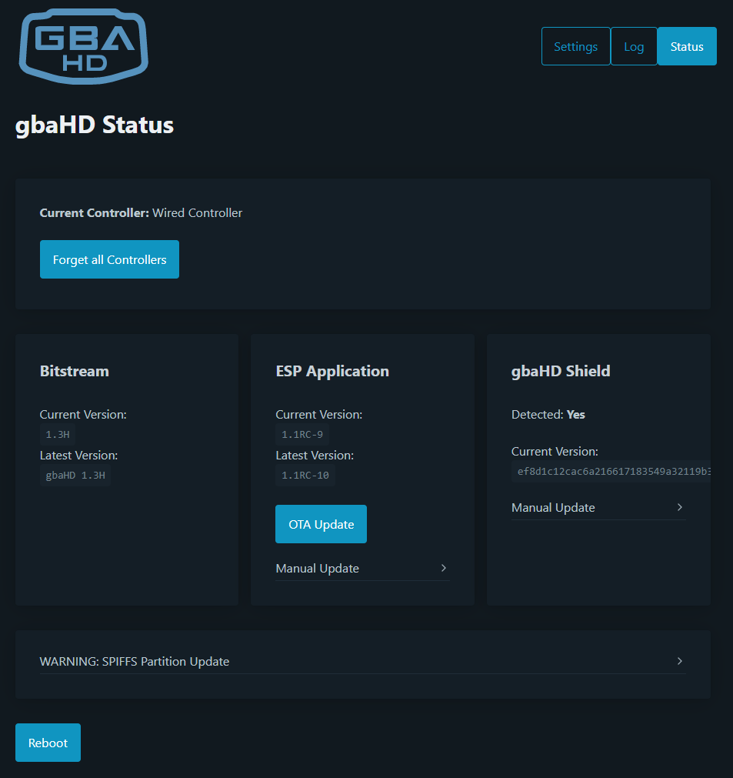
static/wiki/gbahd_webui_startpage.png
