gbaHD/GBAHD-Shield/static/wiki/jlcpcb1.JPG

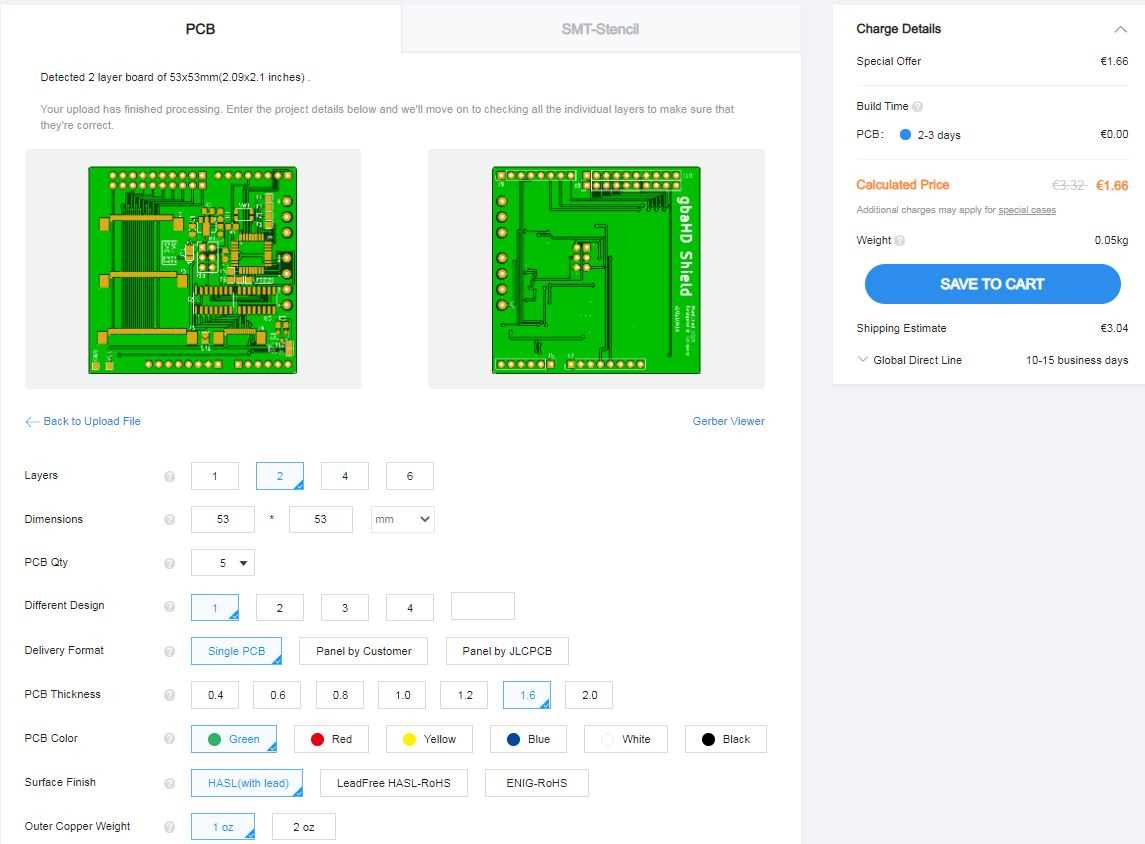
static/wiki/jlcpcb1.JPG
