gbaHD/GBAHD-Shield/static/wiki/jlcpcb.JPG

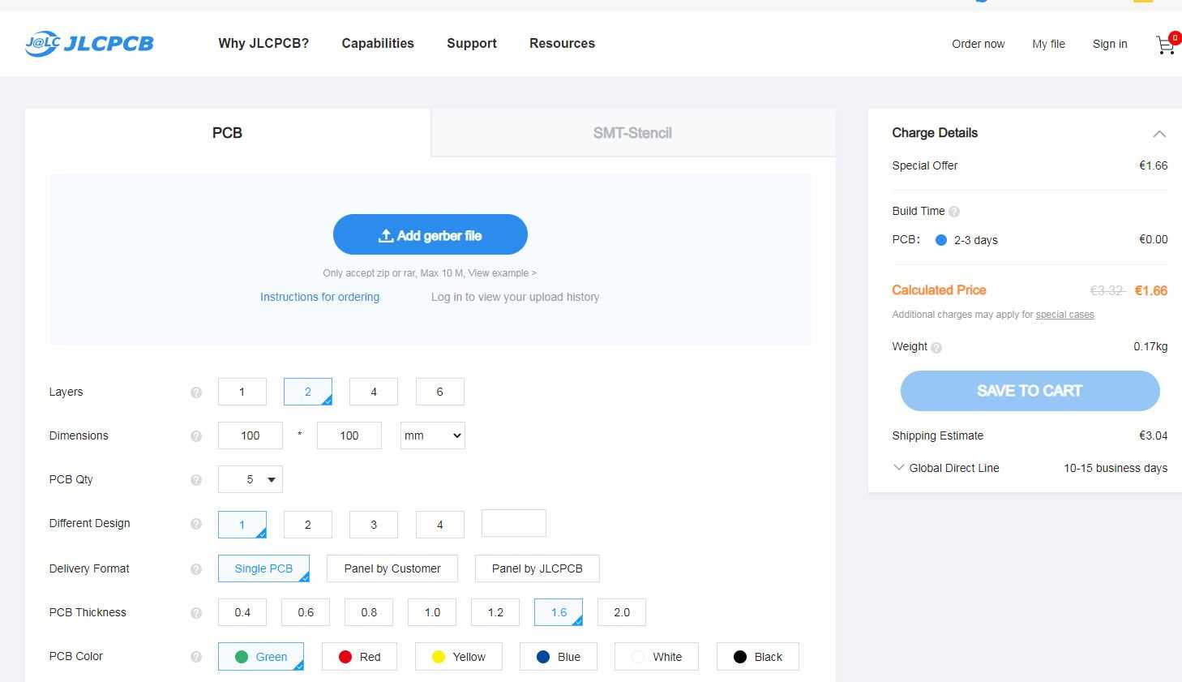
static/wiki/jlcpcb.JPG
