gbaHD/GBAHD-Shield/static/wiki/obga_hookup_closeup.jpg

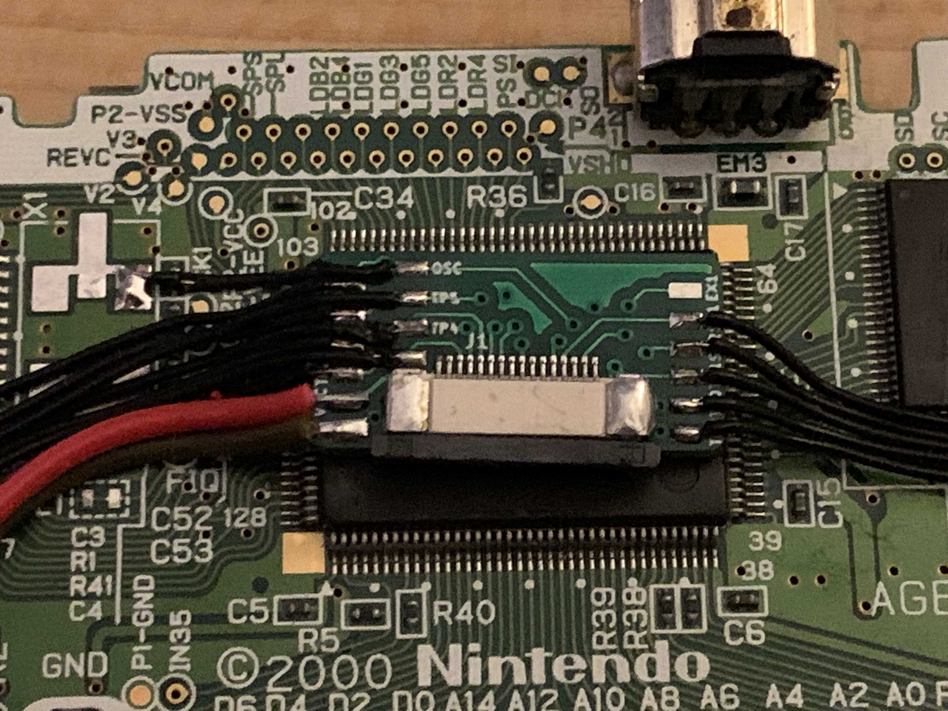
static/wiki/obga_hookup_closeup.jpg
