gbaHD/GBAHD-Shield/static/wiki/ogba-flex_16pin.JPG

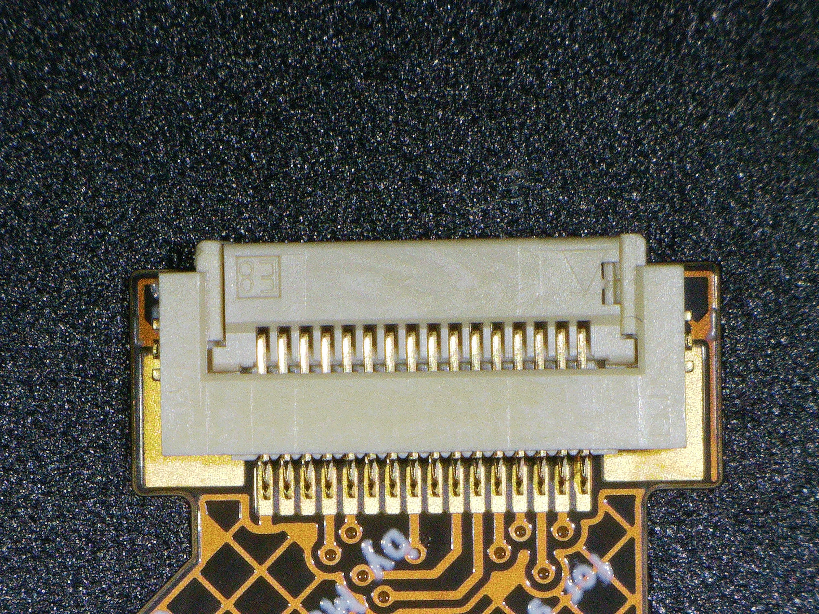
static/wiki/ogba-flex_16pin.JPG
