gbaHD/GBAHD-Shield/static/wiki/ogba_fixed-power.jpg

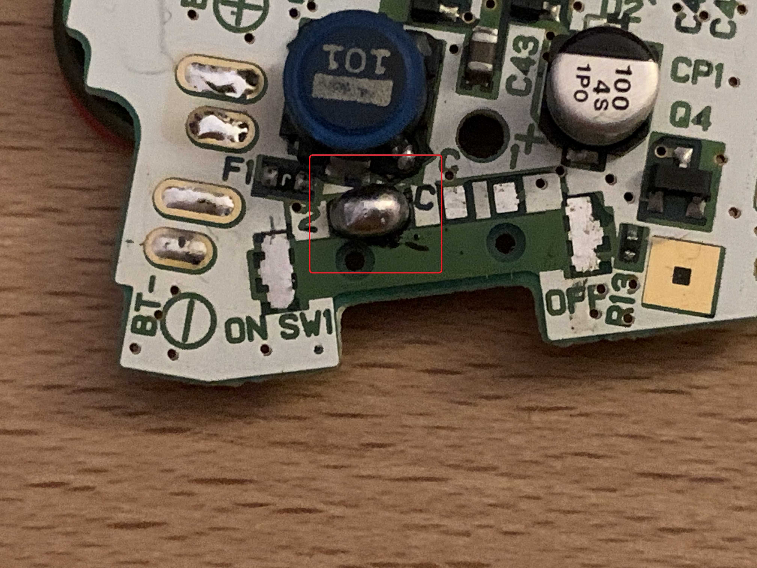
static/wiki/ogba_fixed-power.jpg
