gbaHD/GBAHD-Shield/static/wiki/ogba_flex-ori.jpg

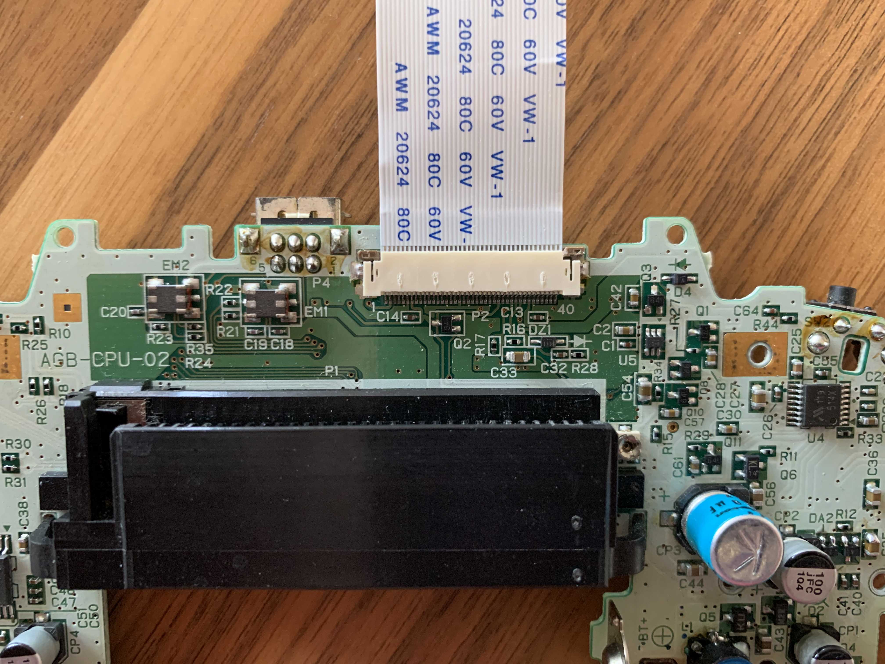
static/wiki/ogba_flex-ori.jpg
