gbaHD/GBAHD-Shield/static/wiki/ogba_flex_aligned.JPG

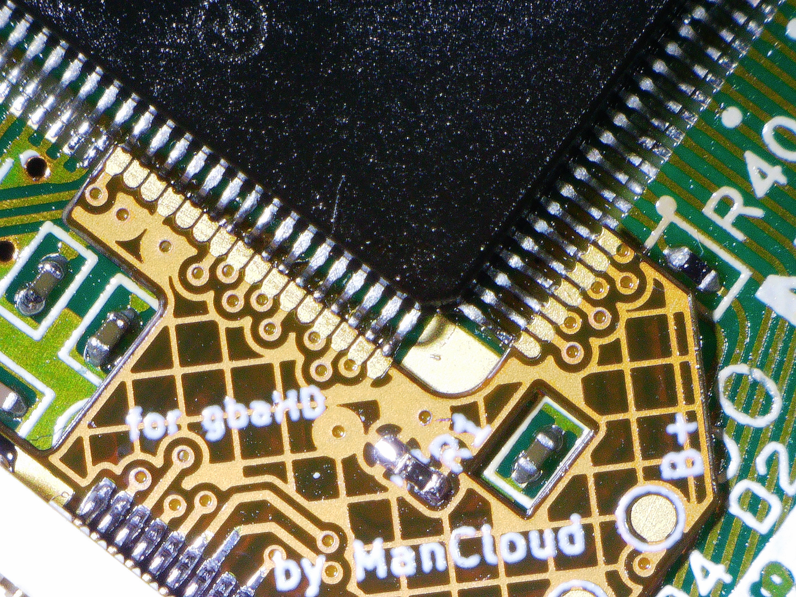
static/wiki/ogba_flex_aligned.JPG
