gbaHD/GBAHD-Shield/static/wiki/ogba_resistor_bat.JPG

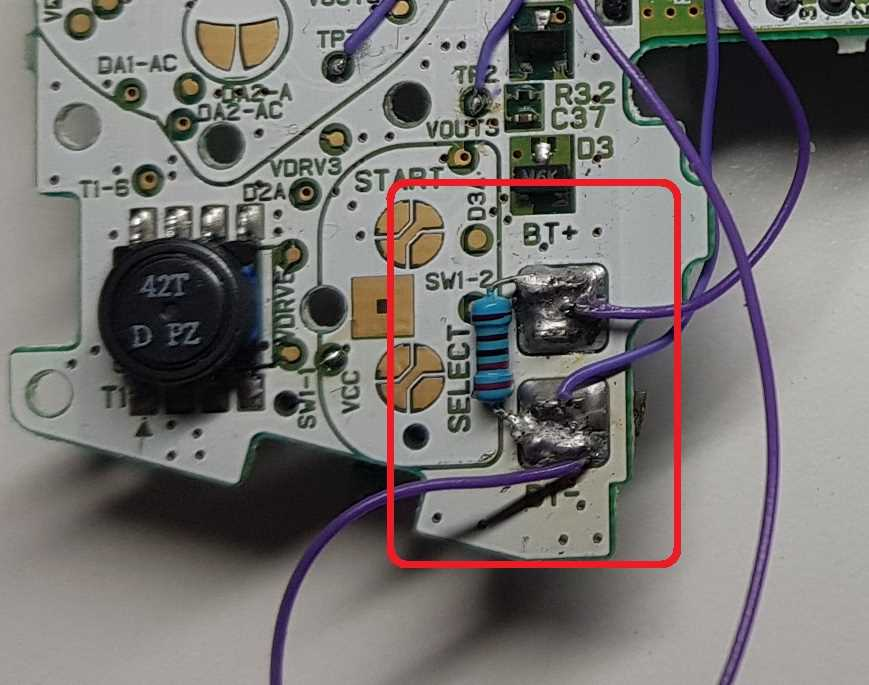
static/wiki/ogba_resistor_bat.JPG
