gbaHD/GBAHD-Shield/static/wiki/ogba_vcc_gnd_.jpg

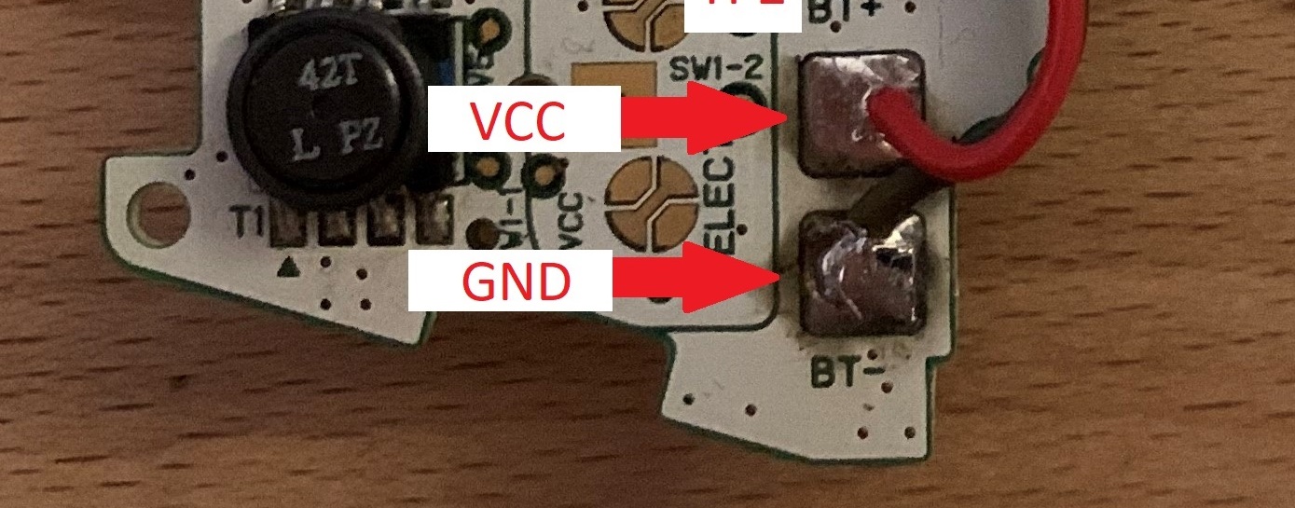
static/wiki/ogba_vcc_gnd_.jpg
