gbaHD/GBAHD-Shield/static/wiki/ogba_volume_fixed.jpg

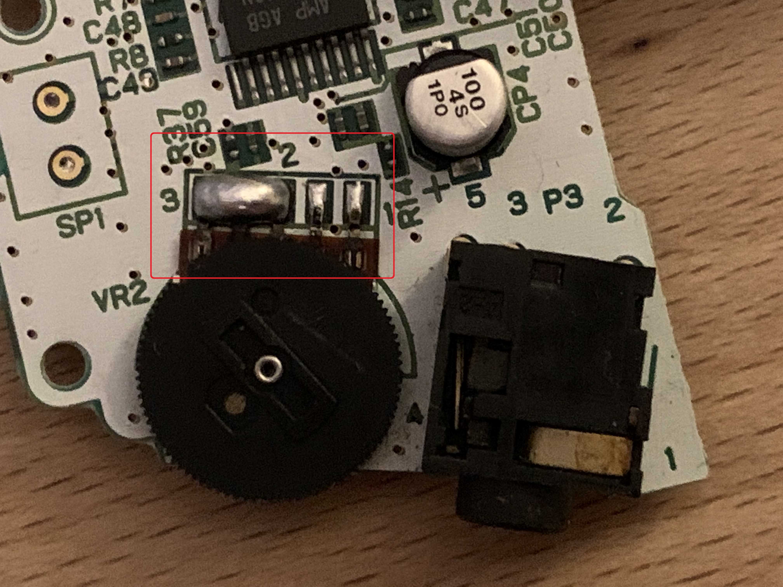
static/wiki/ogba_volume_fixed.jpg
