gbaHD/GBAHD-Shield/static/wiki/ogba_with_spartan_and_shield.jpg

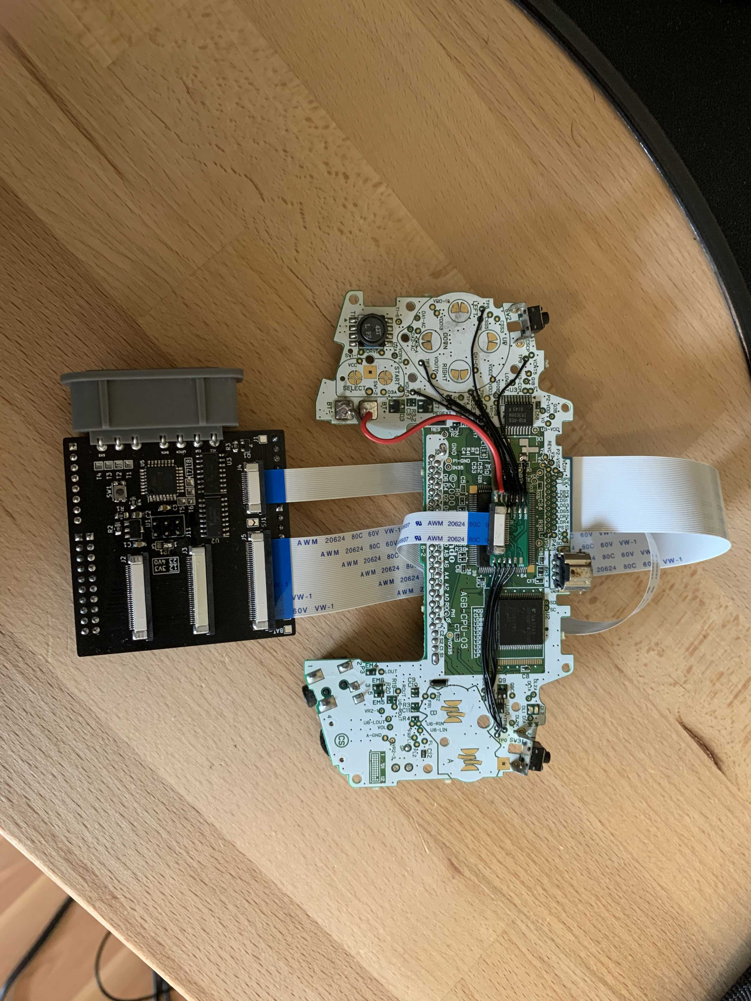
static/wiki/ogba_with_spartan_and_shield.jpg
