gbaHD/GBAHD-Shield/static/wiki/ogba_with_spartan_and_shield_1.jpg

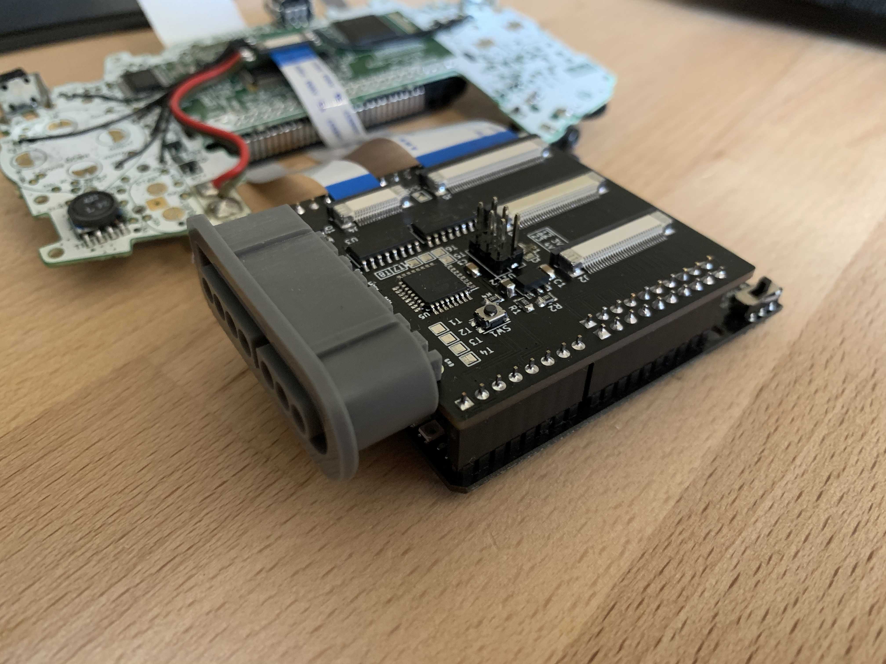
static/wiki/ogba_with_spartan_and_shield_1.jpg
