gbaHD/GBAHD-Shield/static/wiki/ota-update.png

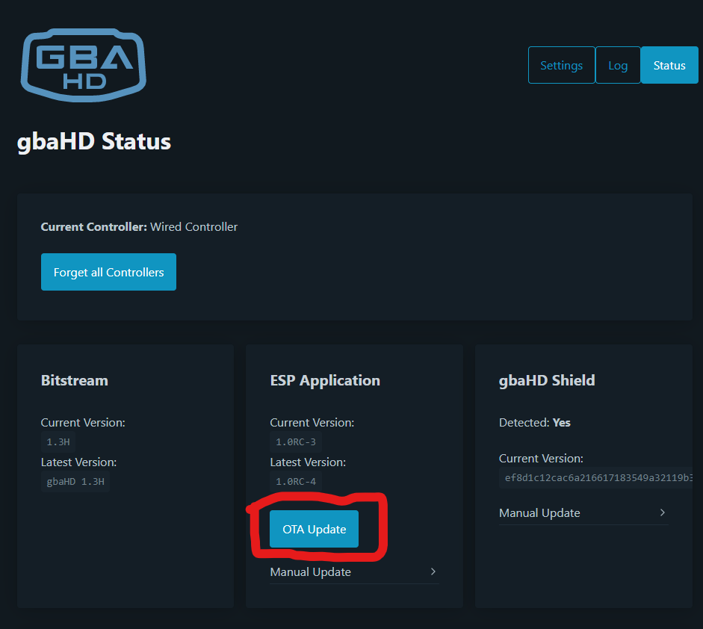
static/wiki/ota-update.png
