gbaHD/GBAHD-Shield/static/wiki/overlay1.JPG

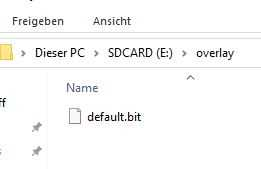
static/wiki/overlay1.JPG
