gbaHD/GBAHD-Shield/static/wiki/overlay.JPG

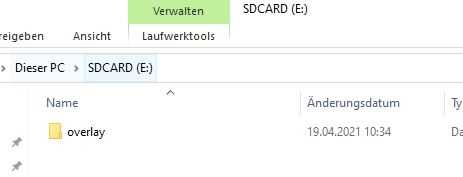
static/wiki/overlay.JPG
