gbaHD/GBAHD-Shield/static/wiki/SDCard.JPG

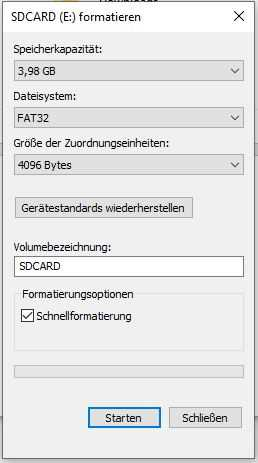
static/wiki/SDCard.JPG
