gbaHD/GBAHD-Shield/static/wiki/sdcard_wificfg.png

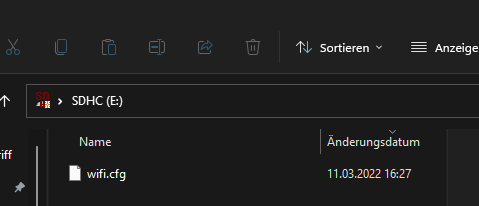
static/wiki/sdcard_wificfg.png
