gbaHD/GBAHD-Shield/static/wiki/sdcard_wificfg_1.png

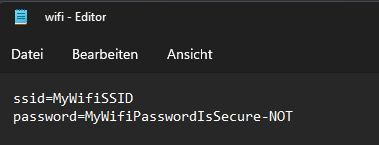
static/wiki/sdcard_wificfg_1.png
