gbaHD/GBAHD-Shield/static/wiki/sea_bootbutton.png

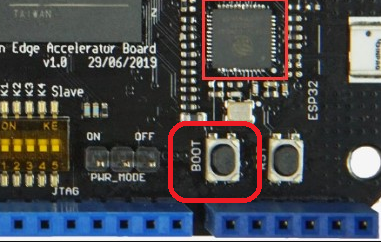
static/wiki/sea_bootbutton.png
