gbaHD/GBAHD-Shield/static/wiki/sea_rxd.jpg

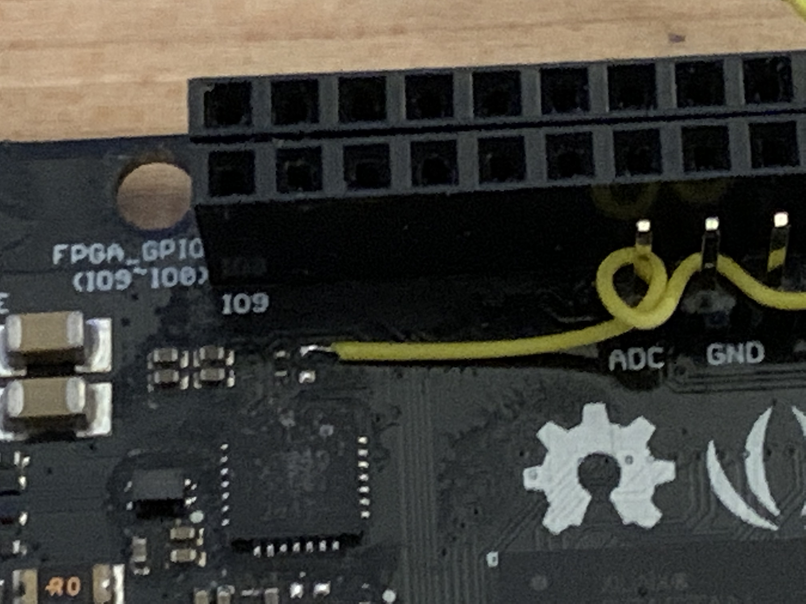
static/wiki/sea_rxd.jpg
