gbaHD/GBAHD-Shield/static/wiki/sea_txd.jpg

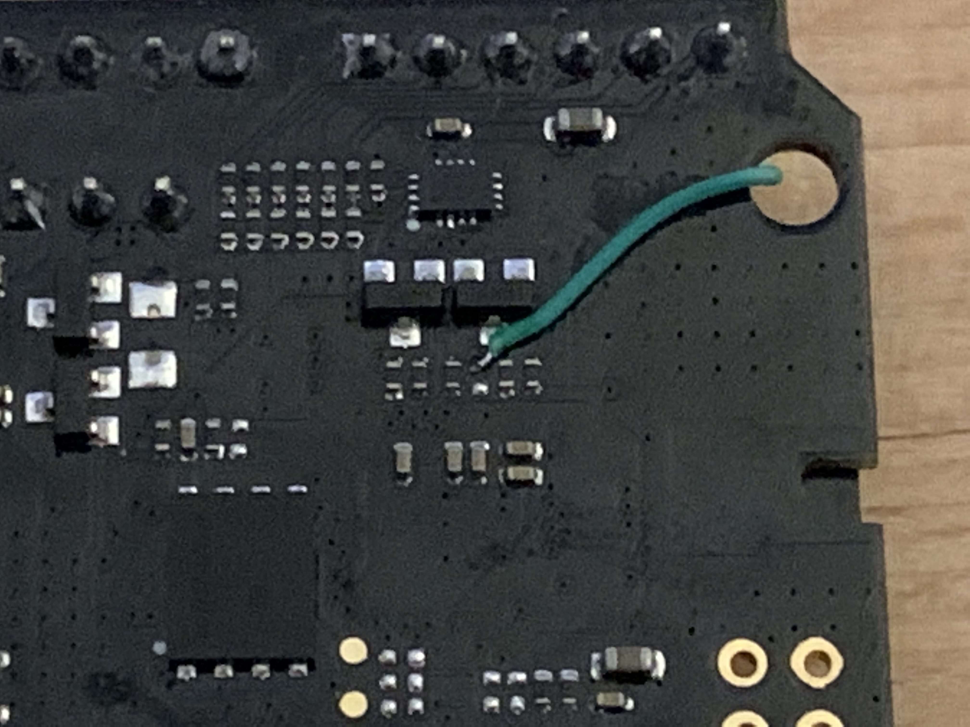
static/wiki/sea_txd.jpg
