gbaHD/GBAHD-Shield/static/wiki/shied_twi-wires_board.jpg

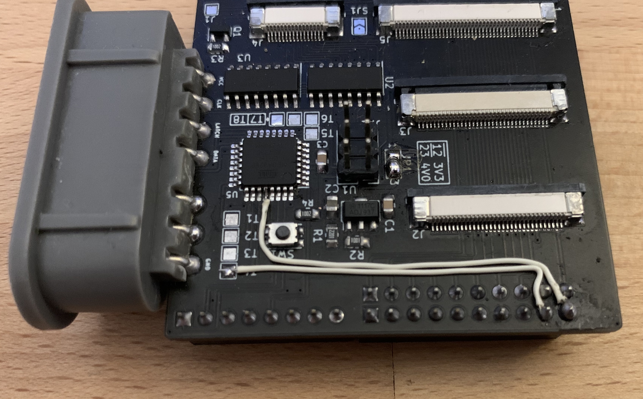
static/wiki/shied_twi-wires_board.jpg
