gbaHD/GBAHD-Shield/static/wiki/shied_twi_wires_kicad.png

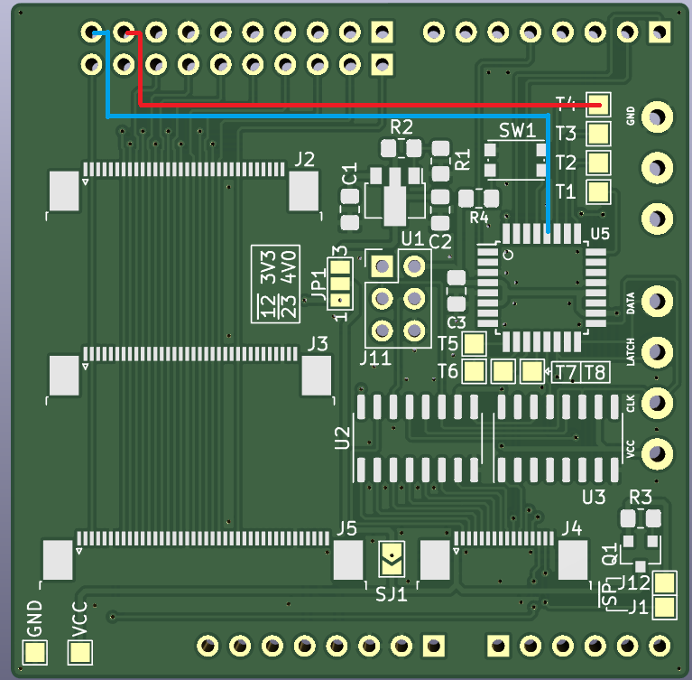
static/wiki/shied_twi_wires_kicad.png
