gbaHD/GBAHD-Shield/static/wiki/shield_flex-ori.jpg

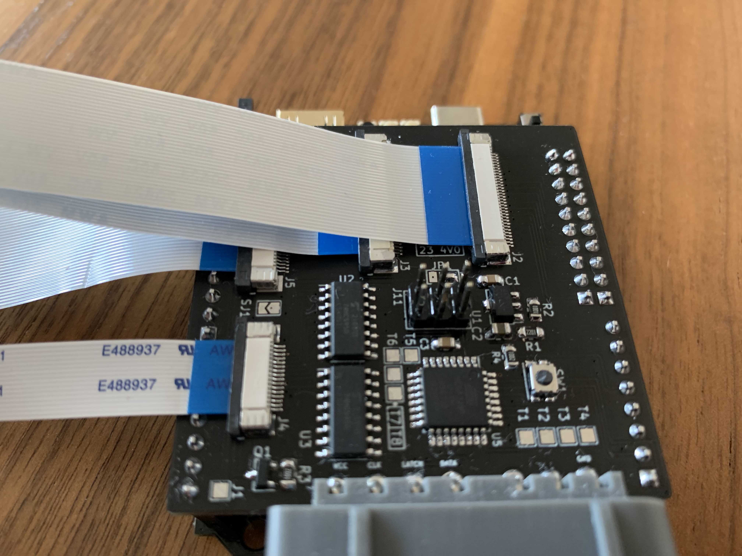
static/wiki/shield_flex-ori.jpg
