gbaHD/GBAHD-Shield/static/wiki/shield_power_jumpers.jpg

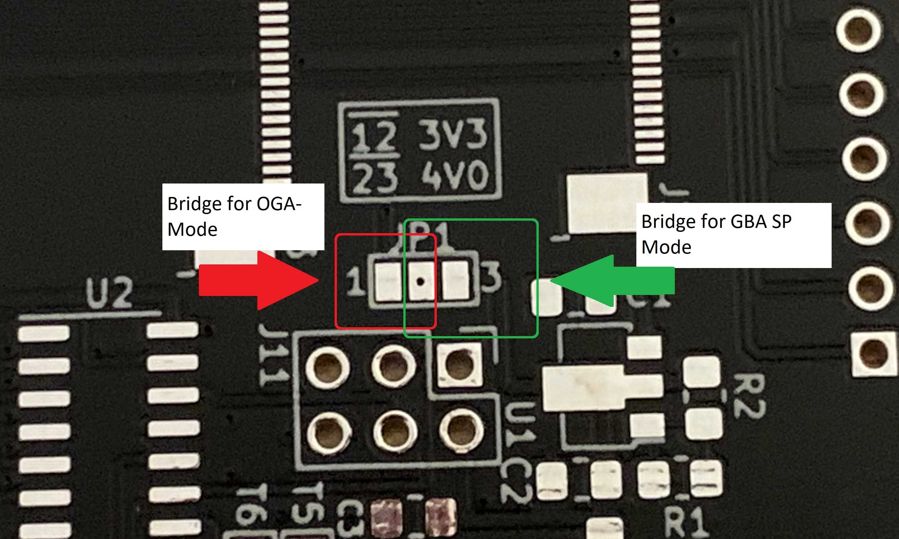
static/wiki/shield_power_jumpers.jpg
