gbaHD/GBAHD-Shield/static/wiki/shield_underside.jpg

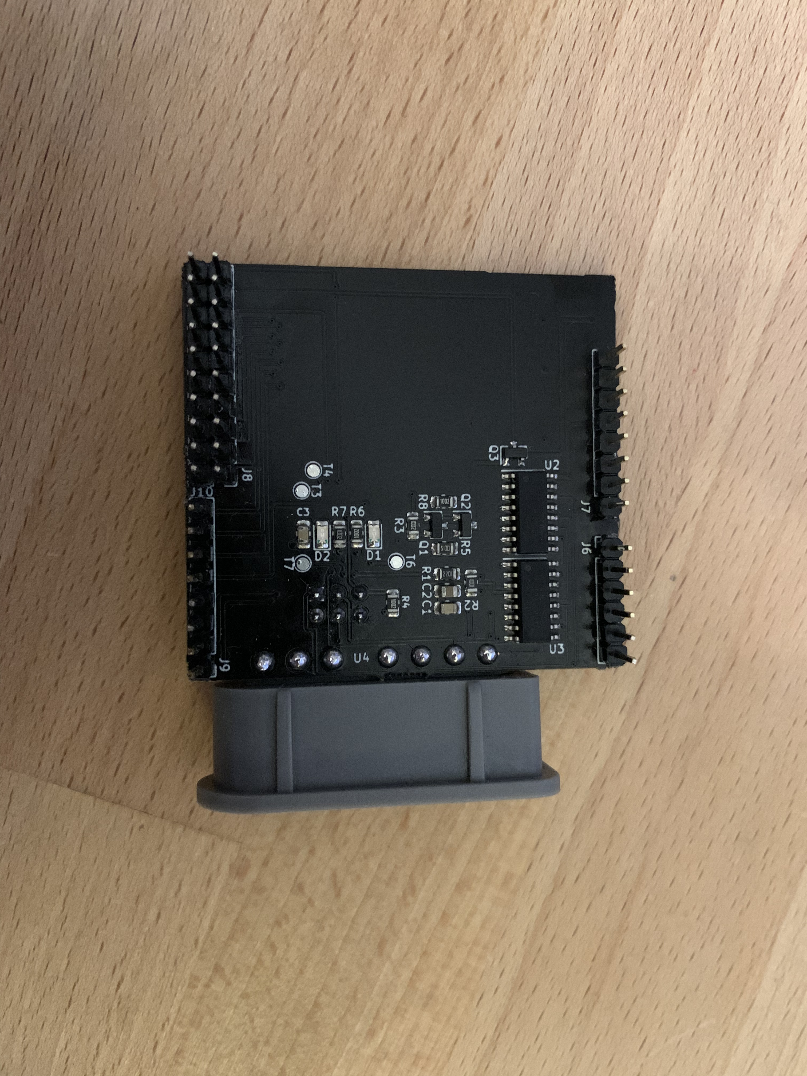
static/wiki/shield_underside.jpg
