gbaHD/GBAHD-Shield/static/wiki/shield_w_ffcdesc.jpg

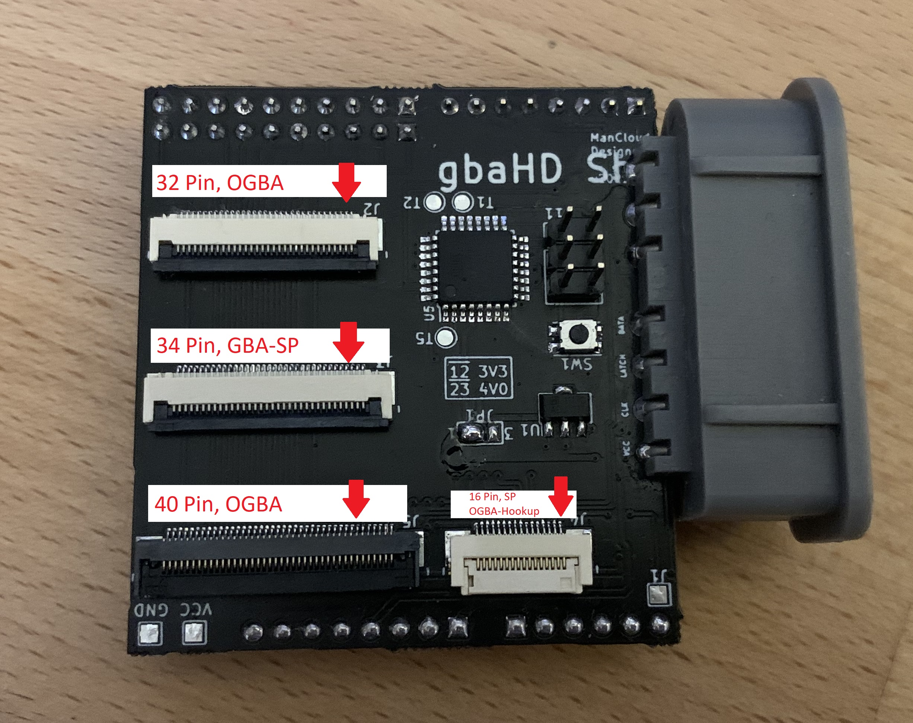
static/wiki/shield_w_ffcdesc.jpg
