gbaHD/GBAHD-Shield/static/wiki/shield_w_flex.jpg

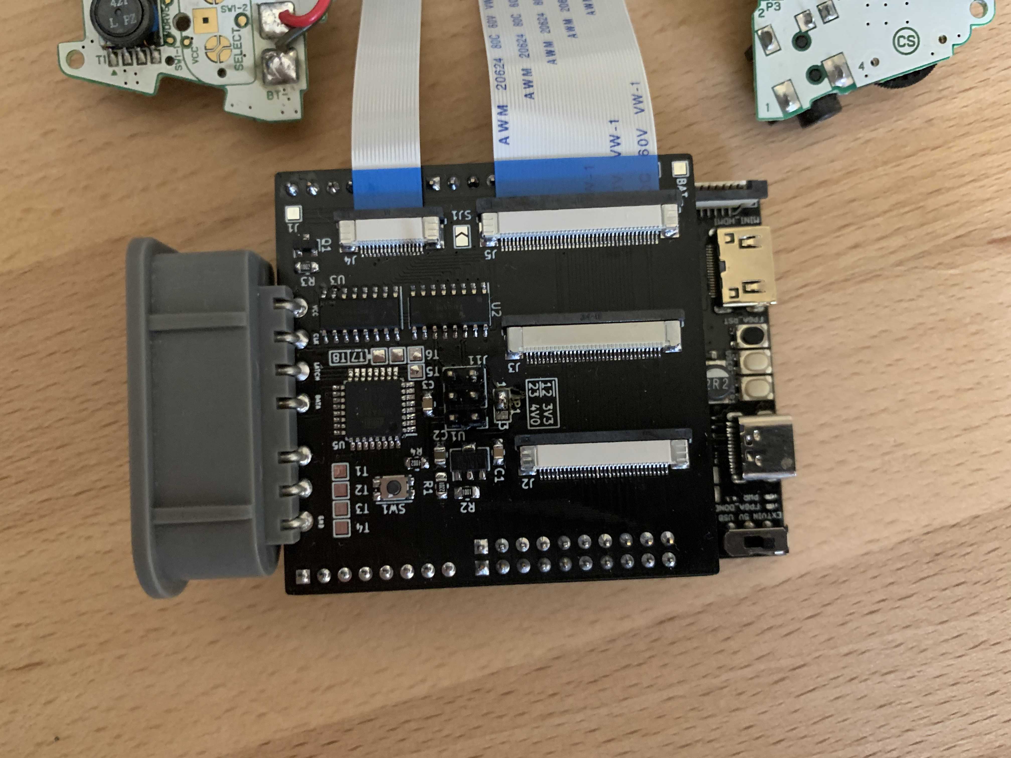
static/wiki/shield_w_flex.jpg
