gbaHD/GBAHD-Shield/static/wiki/shield_with_pins.jpg

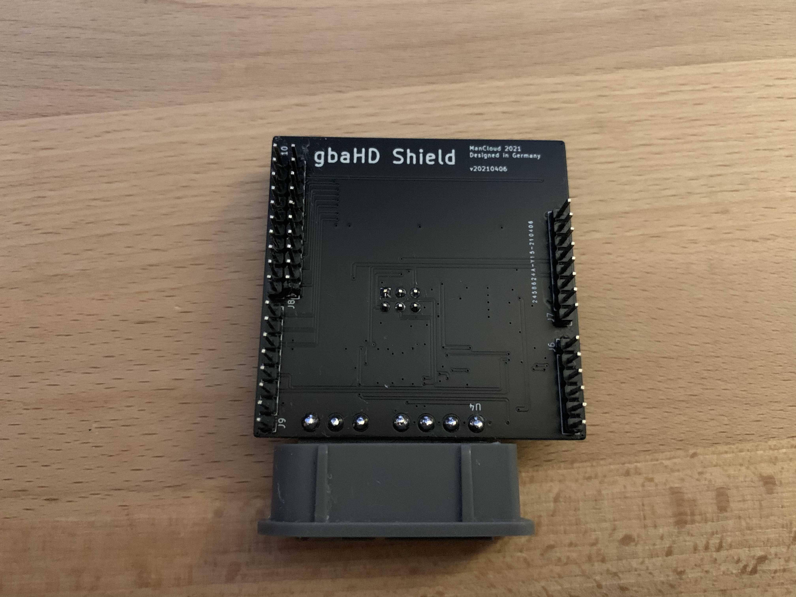
static/wiki/shield_with_pins.jpg
