gbaHD/GBAHD-Shield/static/wiki/sketch1.JPG

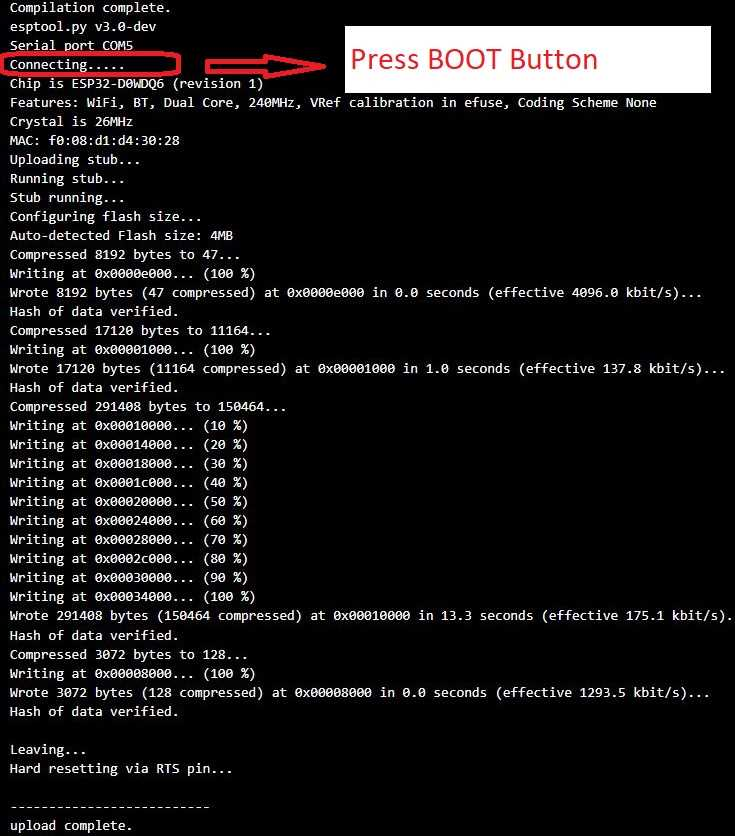
static/wiki/sketch1.JPG
