gbaHD/GBAHD-Shield/static/wiki/sketch2.JPG

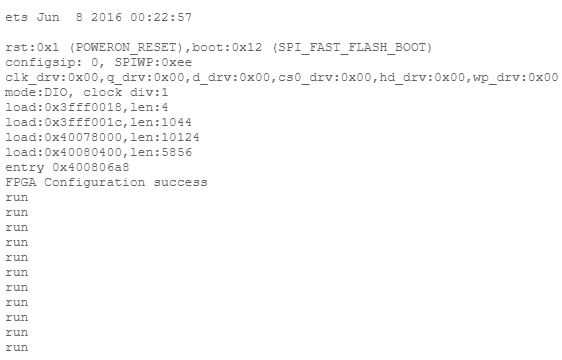
static/wiki/sketch2.JPG
