gbaHD/GBAHD-Shield/static/wiki/sp-flex_16pin.JPG

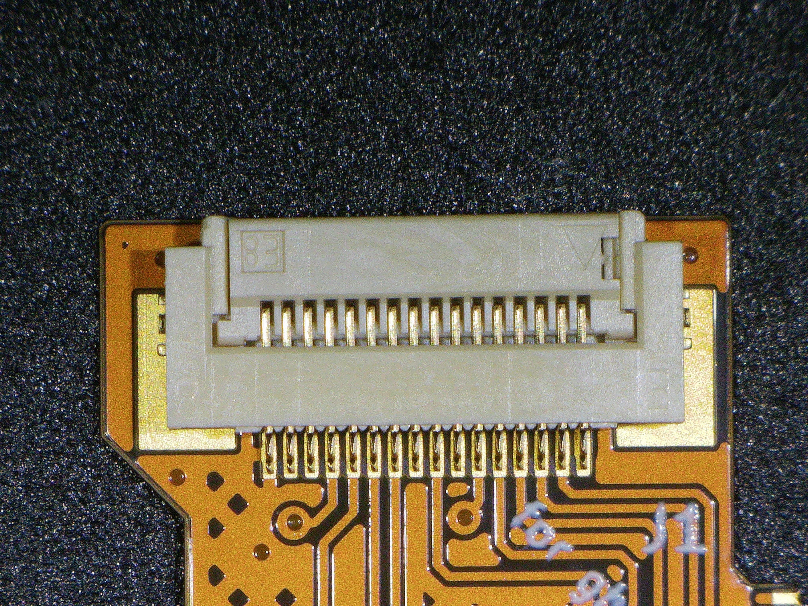
static/wiki/sp-flex_16pin.JPG
