gbaHD/GBAHD-Shield/static/wiki/sp-flex_aligned.jpg

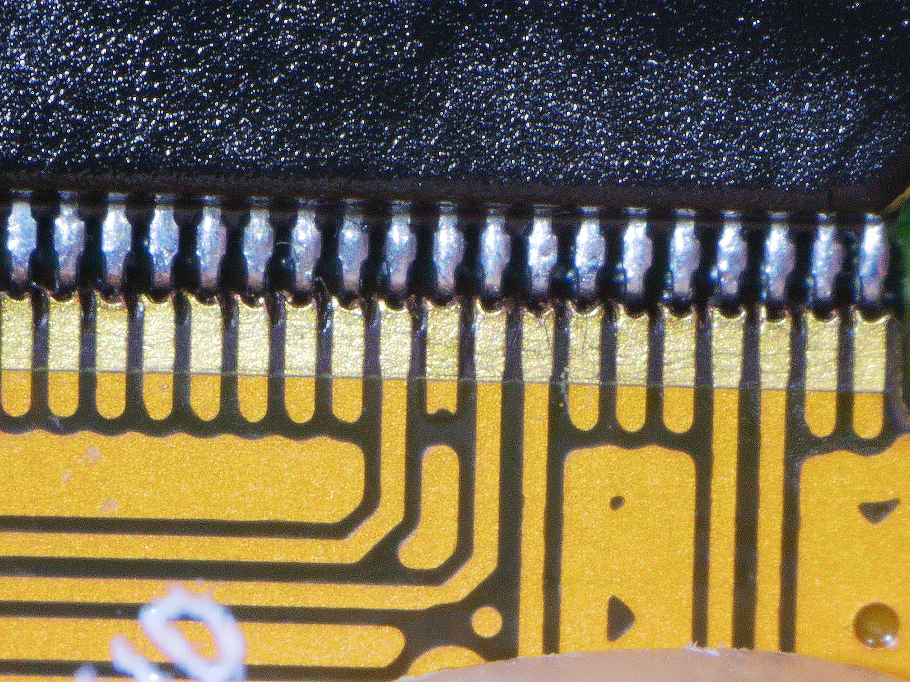
static/wiki/sp-flex_aligned.jpg
