gbaHD/GBAHD-Shield/static/wiki/sp_audiobridge2.jpg

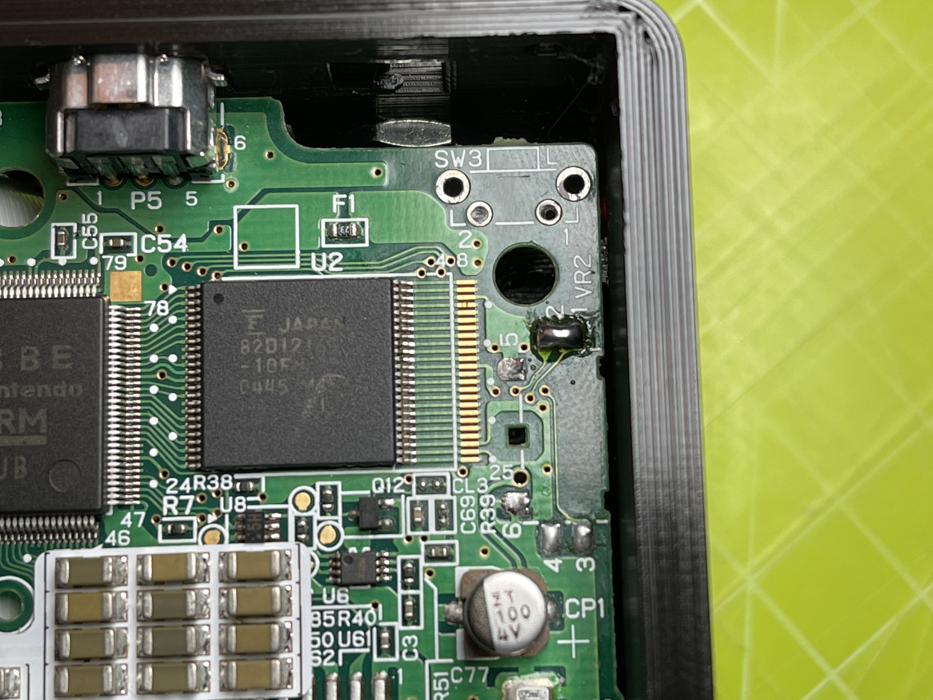
static/wiki/sp_audiobridge2.jpg
