gbaHD/GBAHD-Shield/static/wiki/sp_clock_removed.jpg

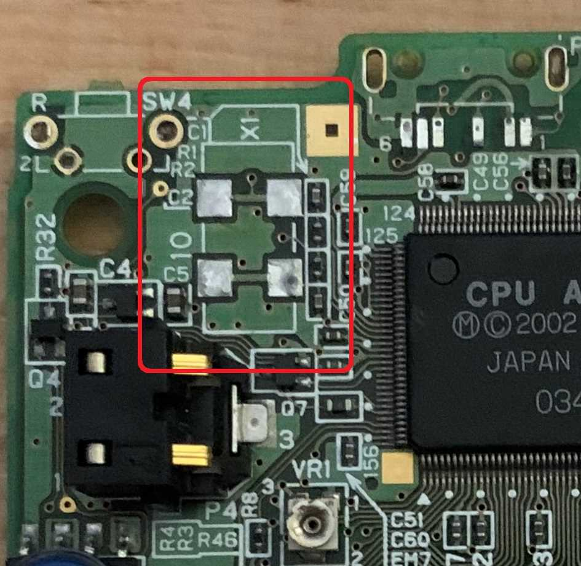
static/wiki/sp_clock_removed.jpg
