gbaHD/GBAHD-Shield/static/wiki/sp_flex-ori.jpg

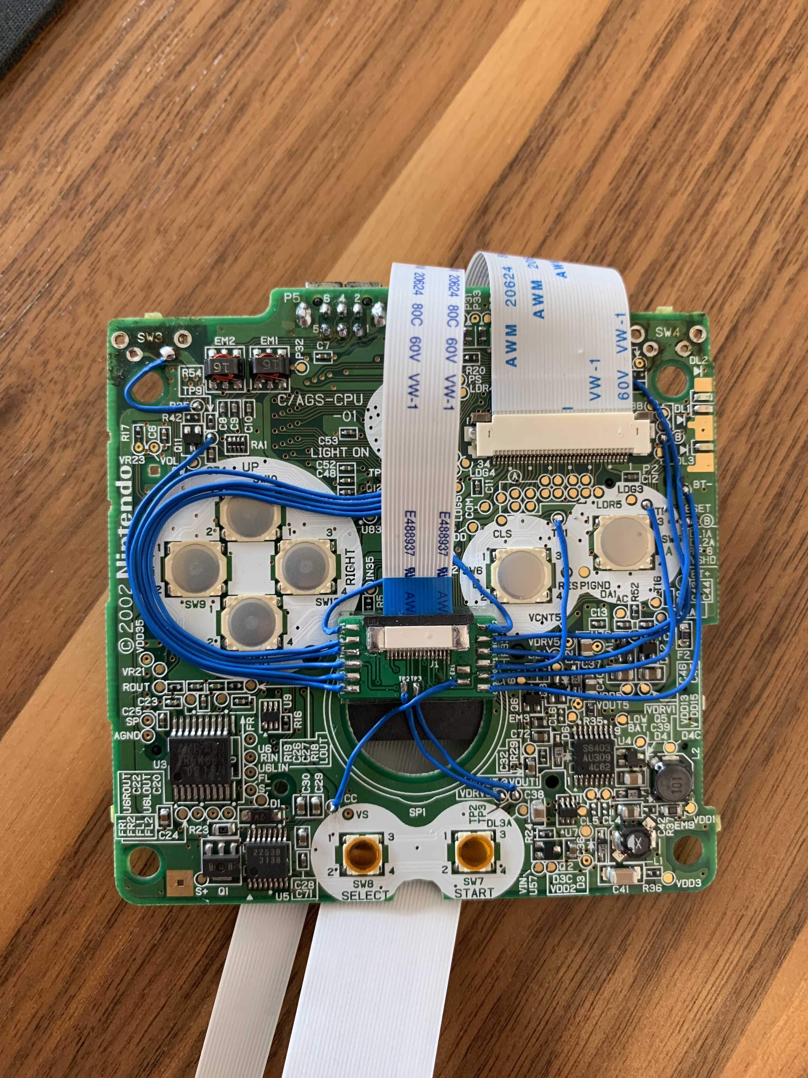
static/wiki/sp_flex-ori.jpg
