gbaHD/GBAHD-Shield/static/wiki/sp_flex.jpg

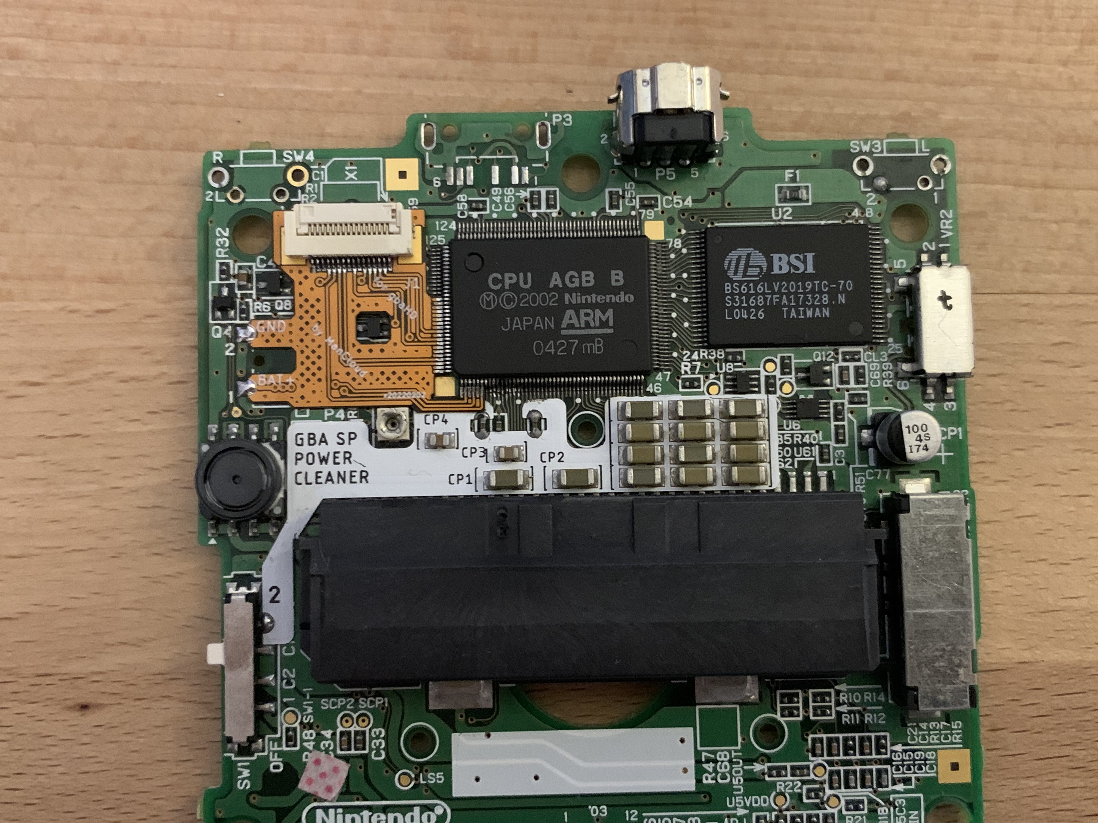
static/wiki/sp_flex.jpg
