gbaHD/GBAHD-Shield/static/wiki/sp_hookupboard.jpg

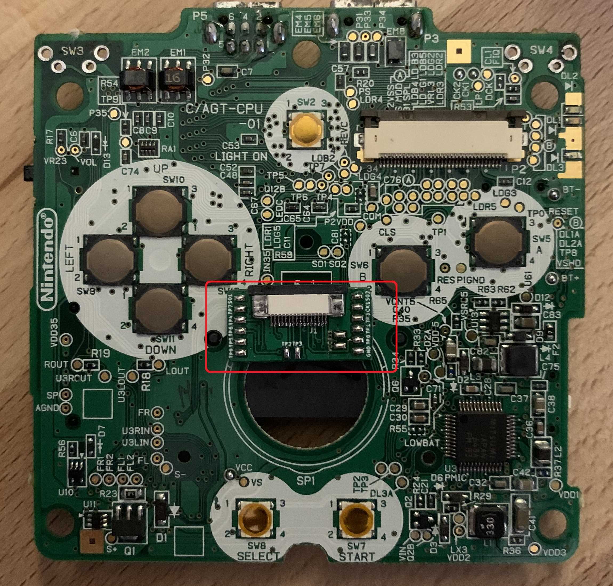
static/wiki/sp_hookupboard.jpg
