gbaHD/GBAHD-Shield/static/wiki/sp_l_r_removed.jpg

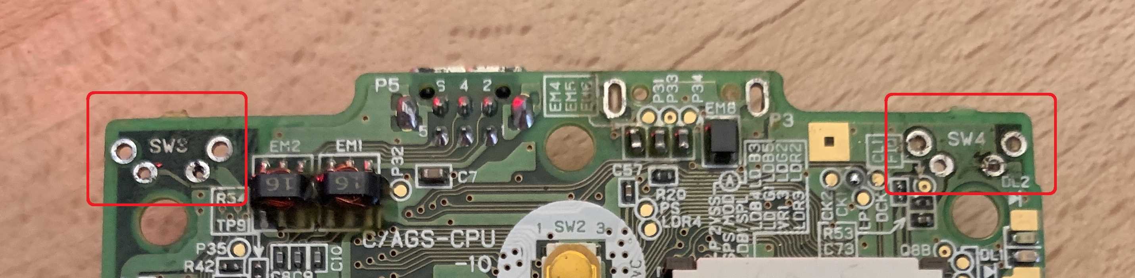
static/wiki/sp_l_r_removed.jpg
