gbaHD/GBAHD-Shield/static/wiki/sp_tp-points-marks.jpg

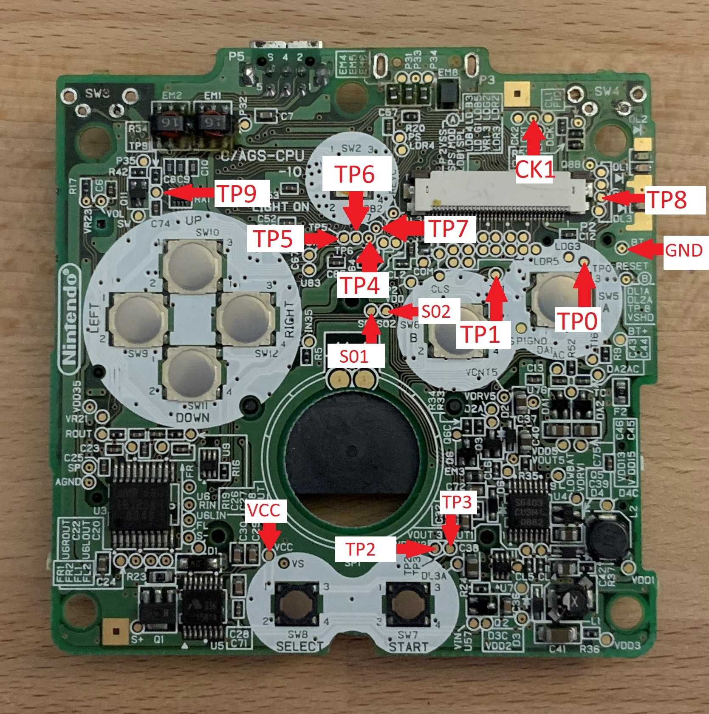
static/wiki/sp_tp-points-marks.jpg
