gbaHD/GBAHD-Shield/static/wiki/spartan_3v3_jumper_poplulated.jpg

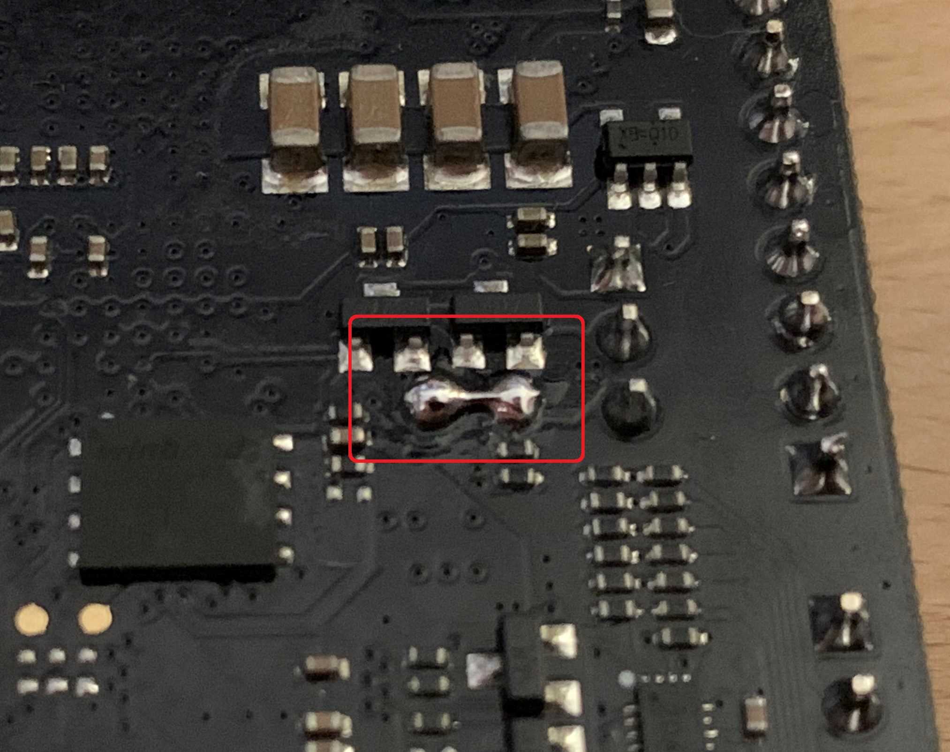
static/wiki/spartan_3v3_jumper_poplulated.jpg
