gbaHD/GBAHD-Shield/static/wiki/spartan_3v3_jumper_unpopulated.jpg

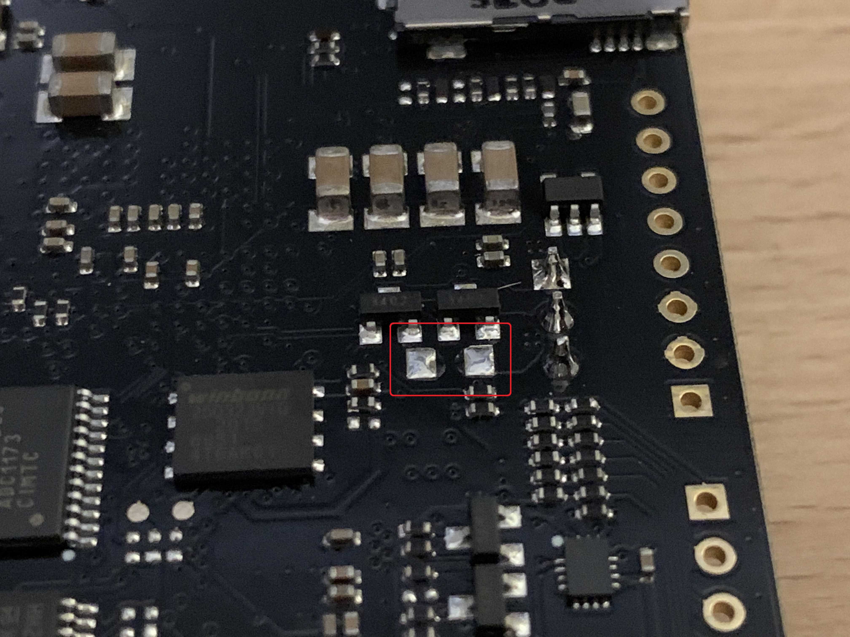
static/wiki/spartan_3v3_jumper_unpopulated.jpg
