gbaHD/GBAHD-Shield/static/wiki/spartan_pwr_mode_off.jpg

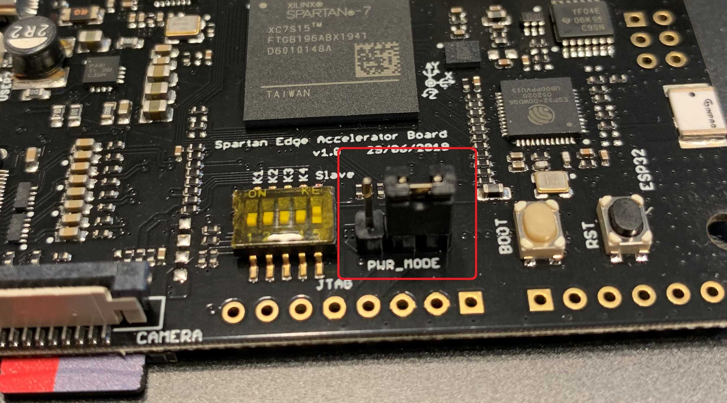
static/wiki/spartan_pwr_mode_off.jpg
