gbaHD/GBAHD-Shield/static/wiki/spartan_pwr_mode_on.jpg

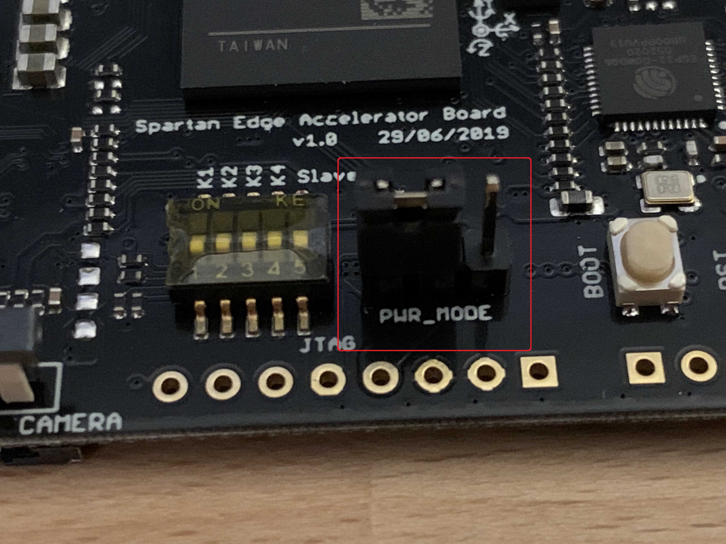
static/wiki/spartan_pwr_mode_on.jpg
