gbaHD/GBAHD-Shield/static/wiki/spartan_slave_jumper_on.jpg

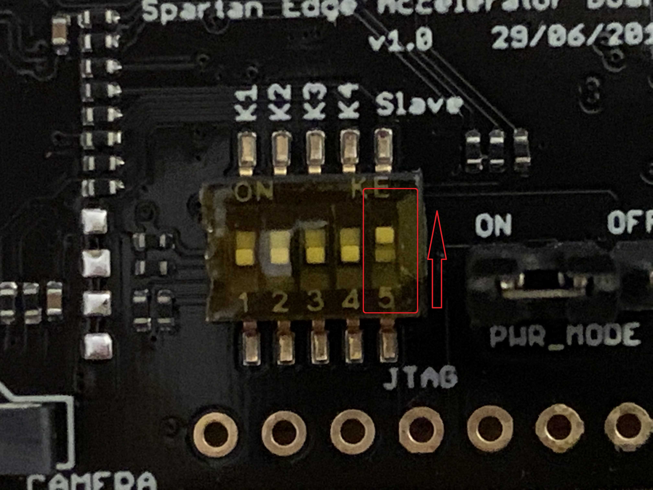
static/wiki/spartan_slave_jumper_on.jpg
