gbaHD/GBAHD-Shield/static/wiki/spartan_w_pins.jpg

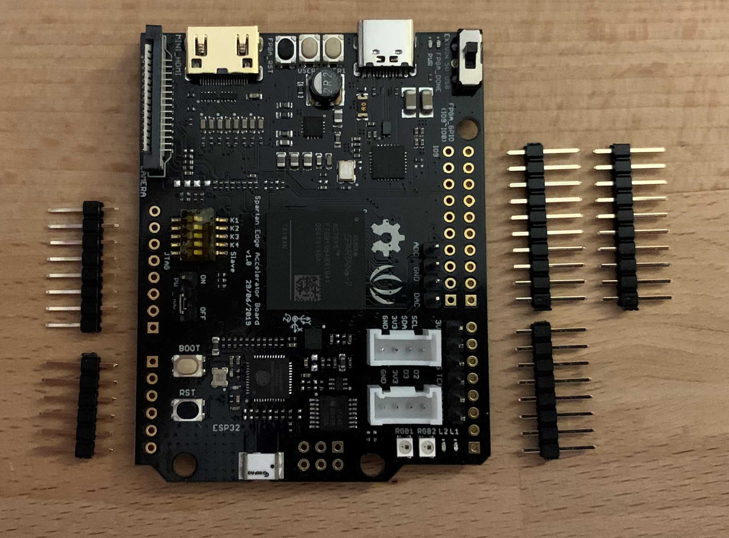
static/wiki/spartan_w_pins.jpg
