gbaHD/GBAHD-Shield/static/wiki/spartan_with_headers.jpg

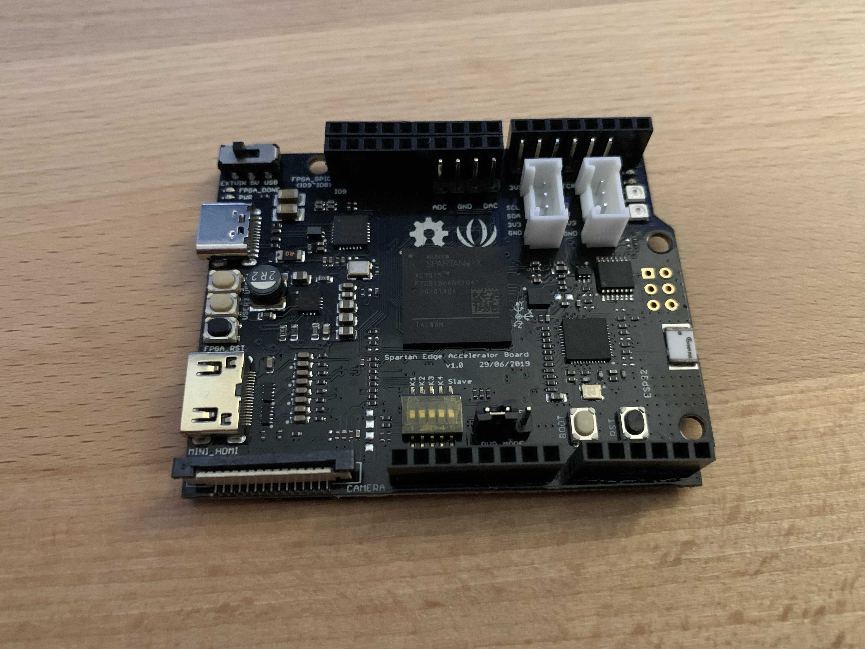
static/wiki/spartan_with_headers.jpg
