gbaHD/GBAHD-Shield/static/wiki/webui.png

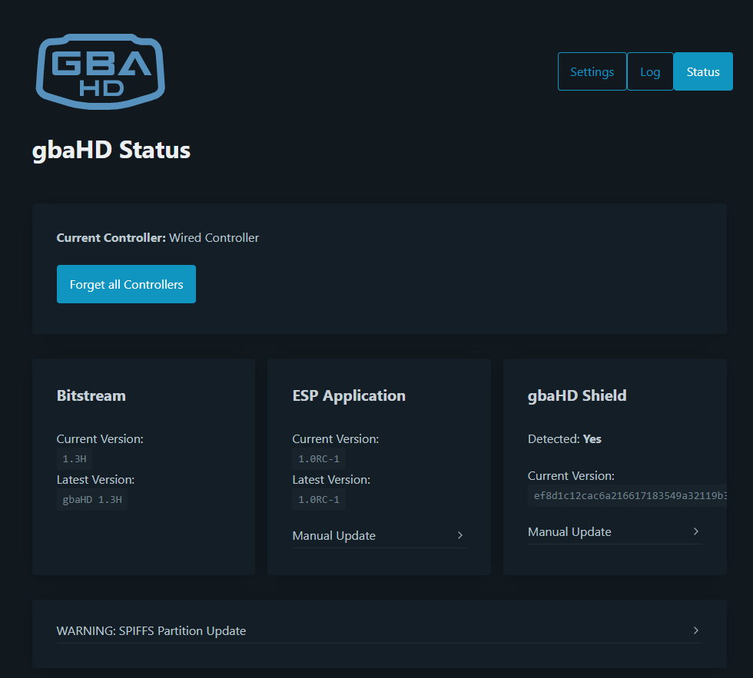
static/wiki/webui.png
