gbaHD/GBAHD-Shield/static/wiki/wificfg-example.png

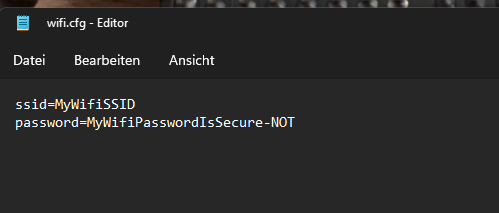
static/wiki/wificfg-example.png
