gbaHD/GBAHD-Shield/static/wiki/xtal.jpg

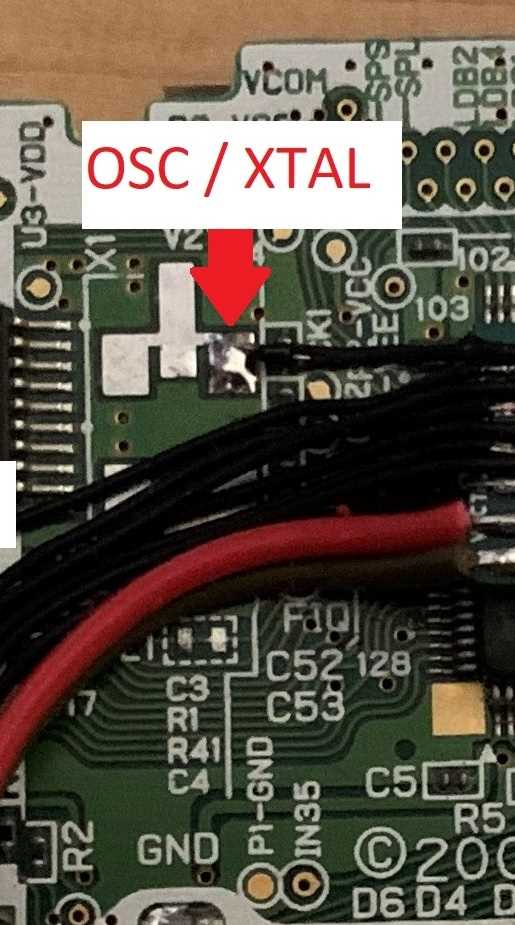
static/wiki/xtal.jpg
