gbaHD/GBAHD-Shield/static/wiki/case_ogba/35mm_solderpoints.jpg

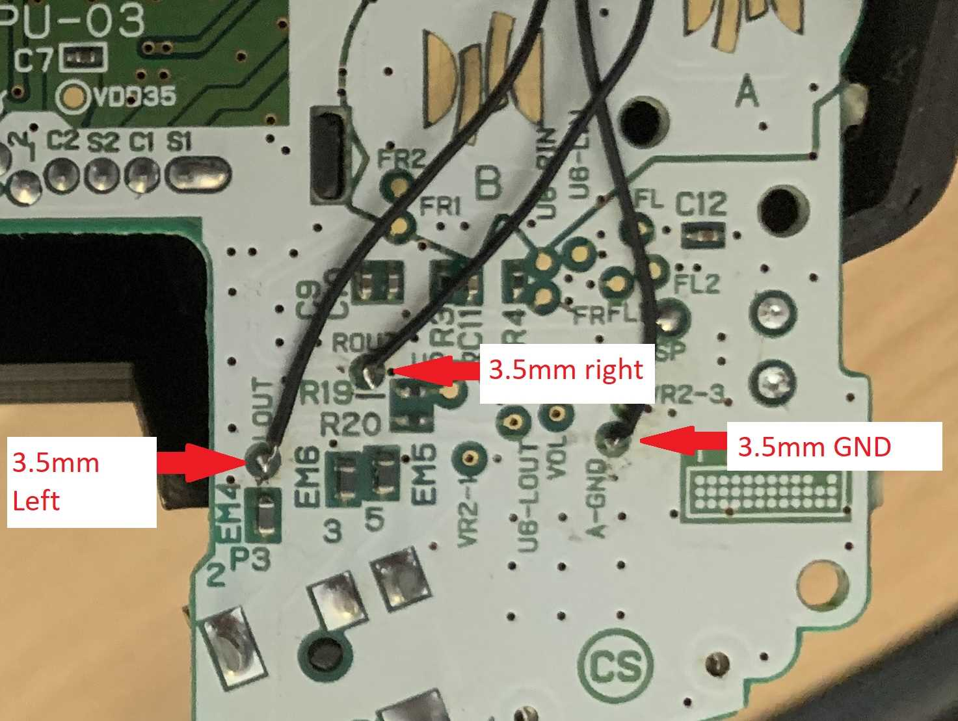
static/wiki/case_ogba/35mm_solderpoints.jpg
