gbaHD/GBAHD-Shield/static/wiki/case_ogba/ogba_case_soldered_wires_spartan.jpg

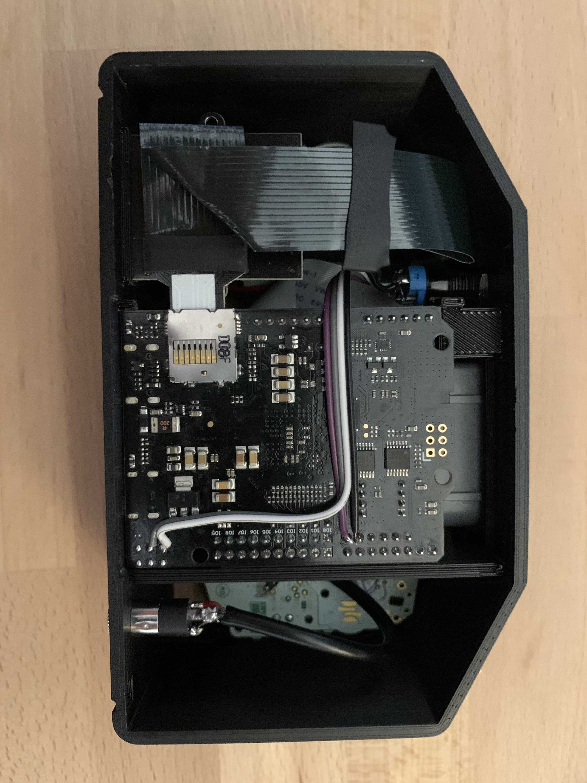
static/wiki/case_ogba/ogba_case_soldered_wires_spartan.jpg
