gbaHD/GBAHD-Shield/static/wiki/case_ogba/spartan_desoldered_switch.jpg

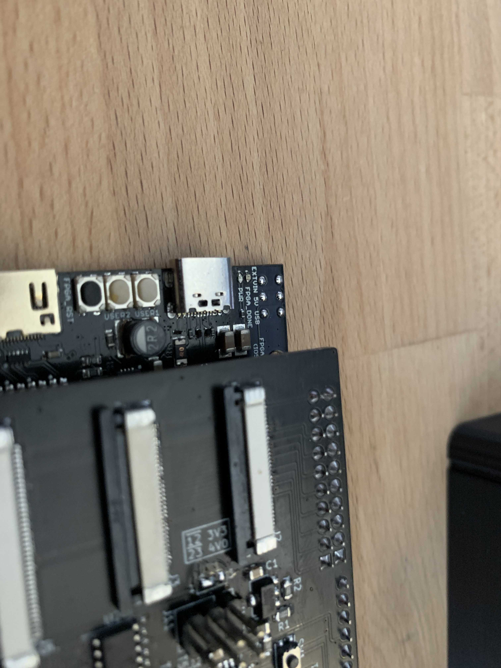
static/wiki/case_ogba/spartan_desoldered_switch.jpg
