gbaHD/GBAHD-Shield/static/wiki/case_sp/reset_solderpoints.jpg

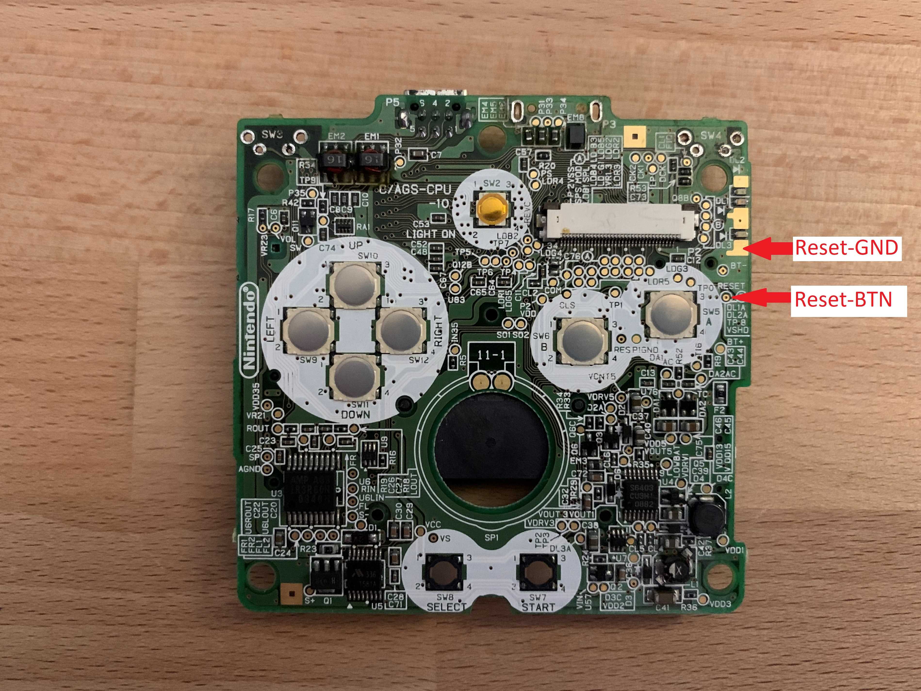
static/wiki/case_sp/reset_solderpoints.jpg
