gbaHD/GBAHD-Shield/static/wiki/ogba-flex_soldered.JPG

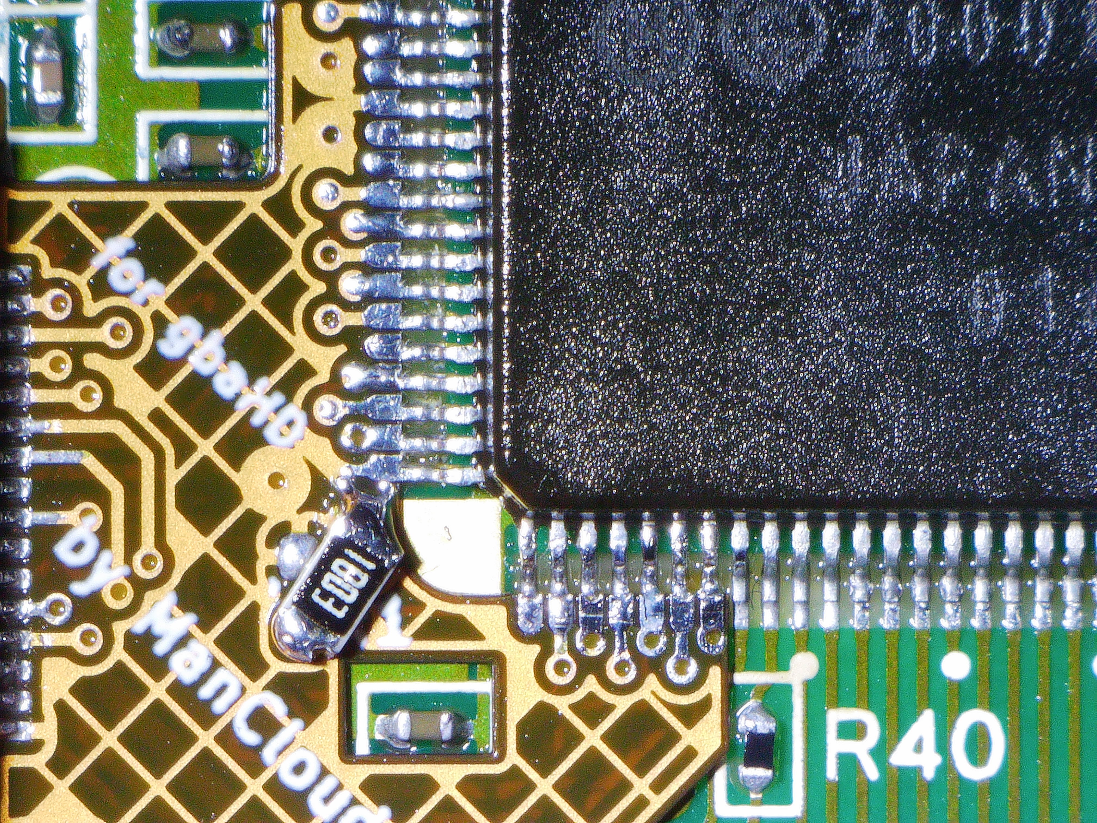
static/wiki/ogba-flex_soldered.JPG
