gbaHD/GBAHD-Shield/static/wiki/sp-flex_soldered.JPG

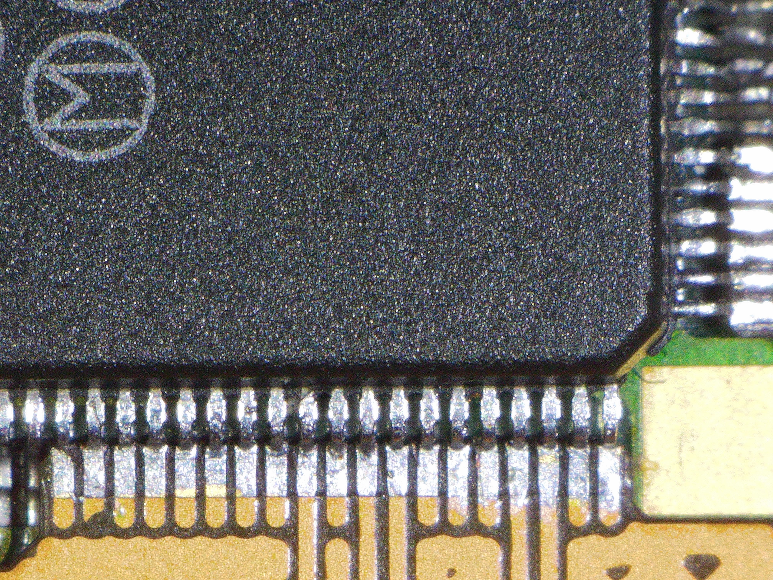
static/wiki/sp-flex_soldered.JPG
