gbaHD/GBAHD-Shield/static/wiki/ogba_testpoints.jpg

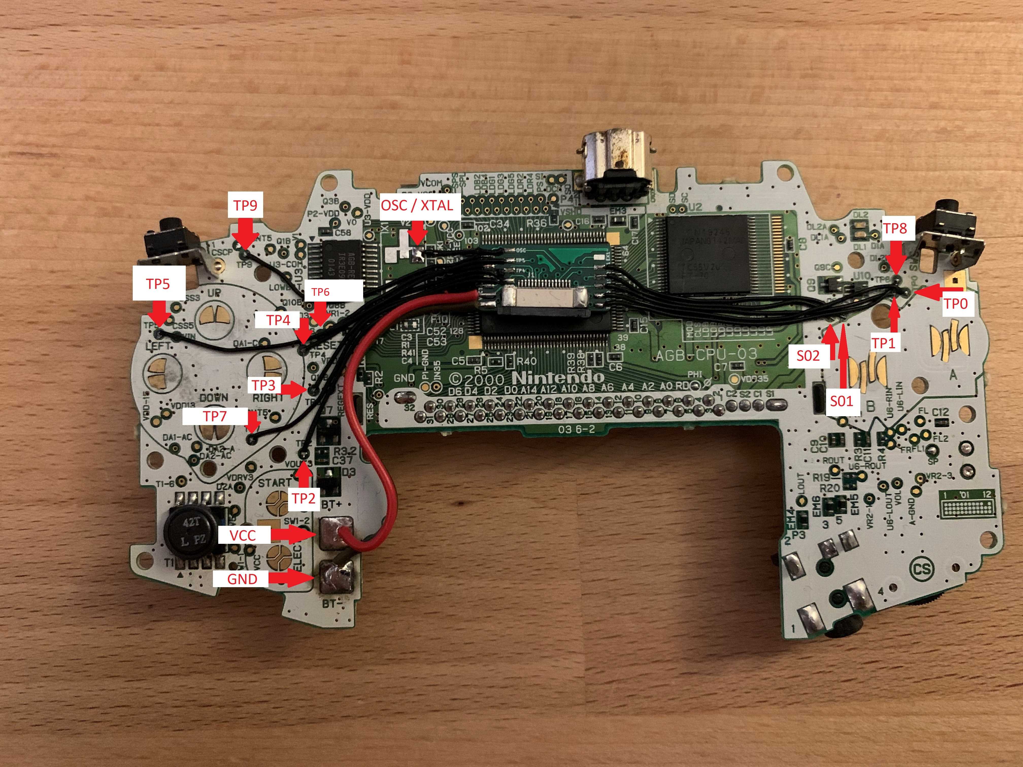
static/wiki/ogba_testpoints.jpg
