gbaHD/GBAHD-Shield/static/wiki/agb-cpu-03_fixes.jpg

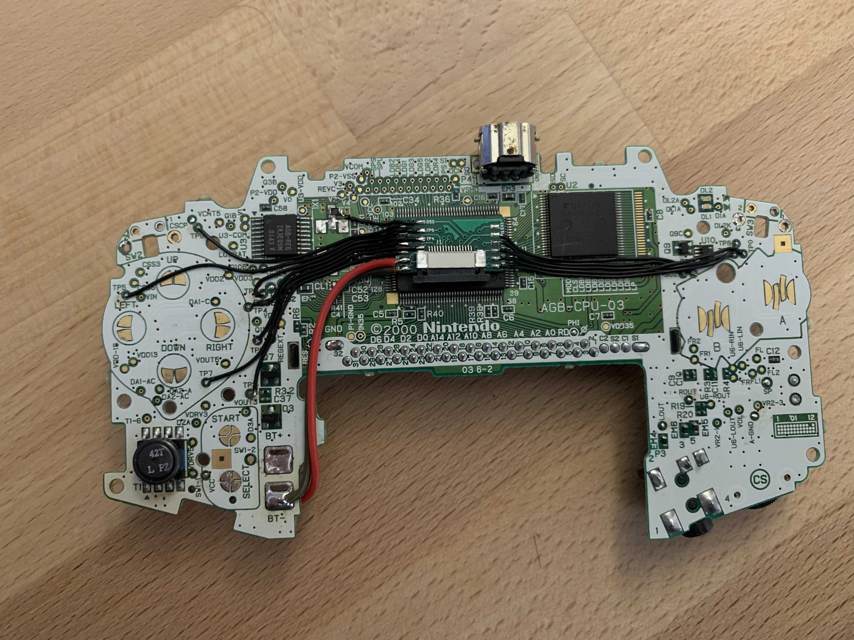
static/wiki/agb-cpu-03_fixes.jpg
