gbaHD/GBAHD-Shield/static/wiki/shield-ex1-fix.jpg

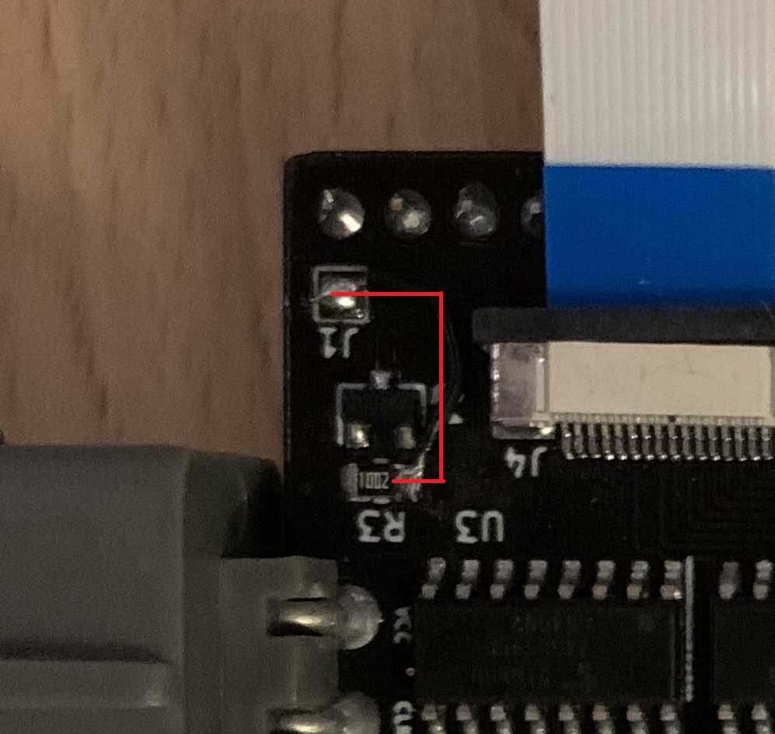
static/wiki/shield-ex1-fix.jpg
