gbaHD/GBAHD-Shield/firmware/esp32/main/wifi_handler.cpp

/*******************************************************************************
  ; -----------------------------------------------------------------------
   gbaHD-ESP32 for zwenergys gbaHD

   MIT License

   Copyright (c) 2021 Alexander Kreutz

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
 *******************************************************************************/

#include <Arduino.h>
#include <WiFi.h>

#include <SD_MMC.h>

#include "wifi_handler.h"
#include "log_handler.h"

#define WIFI_SSID_SIZE    ( 32U )  // 32 length
#define WIFI_PW_SIZE      ( 64U )     // 64 length
#define WIFI_CREDS_FILE    "/wifi.cfg"


void Wifi_Handler_Class::getSTACredentials(Wifi_Config& wifi_config)
{
    Preferences_Handler.getWifiCredentials(wifi_config);
    Log_Handler.println(wifi_config.ssid);

    if (SD_MMC.begin())
    {
        Wifi_Config new_wifi_config = wifi_config;

        File wifi_creds = SD_MMC.open(WIFI_CREDS_FILE, "r", true);

        if (wifi_creds)
        {
            Log_Handler.println("Found creds file...");
            String line = wifi_creds.readStringUntil(0xA);
            do {
                int idx = -1;
                line.replace("\r", "");
                idx = line.indexOf("=");
                if (idx != -1)
                {
                    String key, value;
                    key = line.substring(0, idx);
                    value = line.substring(idx + 1, line.length());
                    key.trim();
                    key.toLowerCase();
                    value.trim();
                    if (key == "ssid")
                    {
                        new_wifi_config.ssid = value;
                    }
                    else if (key == "password")
                    {
                        new_wifi_config.password = value;
                    }
                    else if (key == "hostname")
                    {
                        new_wifi_config.hostname = value;
                    }
                }
                line = wifi_creds.readStringUntil(0xA);
            } while (line.length() > 0);
            wifi_creds.close();
        }
        else
        {
            Log_Handler.println("Didn't find any Wifi Creds file on SD-Card. Skipping Update.");
        }

        if ((wifi_config.ssid != new_wifi_config.ssid) 
            || (wifi_config.password != new_wifi_config.password) 
            || (wifi_config.hostname != new_wifi_config.hostname) )
        {
            if ((new_wifi_config.ssid.length() < WIFI_SSID_SIZE) && (new_wifi_config.password.length() < WIFI_PW_SIZE))
            {
                Preferences_Handler.saveWifiCredentials(new_wifi_config);
                wifi_config = new_wifi_config;
            }
            else
            {
                Log_Handler.println("Error: Entered SSID or Password is too long and is potentially invalid.");
            }
        }
    }
    else
    {
        Log_Handler.println("Error: SD_MMC not available. Skip getting new Credentials...");
    }

    
}


void Wifi_Handler_Class::connectWifiSTA(Wifi_Config& wifi_config)
{
    WiFi.begin(wifi_config.ssid.c_str(), wifi_config.password.c_str());
}

void Wifi_Handler_Class::shutdown()
{
    WiFi.disconnect(true);
    WiFi.mode(WIFI_OFF);
}

void Wifi_Handler_Class::init()
{
    Wifi_Config wifi_config;

    getSTACredentials(wifi_config);

    WiFi.setHostname(wifi_config.hostname.c_str());

    connectWifiSTA(wifi_config);

}

void Wifi_Handler_Class::update()
{
    static wl_status_t old_status = WL_NO_SHIELD;
    wl_status_t new_status = WiFi.status();
    if (old_status != new_status)
    {
        switch(new_status)
        {
            case WL_IDLE_STATUS:
            case WL_CONNECTED:
                Log_Handler.println("Connection established.");
                Log_Handler.print("IP:\t");
                Log_Handler.println(WiFi.localIP());
                WiFi.setTxPower(WIFI_POWER_19_5dBm);
                break;
            case WL_NO_SSID_AVAIL:
            case WL_CONNECT_FAILED:
            case WL_CONNECTION_LOST:
                Log_Handler.println("Connection not available.");
                break;
            case WL_SCAN_COMPLETED:
            case WL_DISCONNECTED:
            default:
            break;
        }

        old_status = new_status;
    }
}



Wifi_Handler_Class Wifi_Handler;
