gbaHD/GBAHD-Shield/static/wiki/cases/ogba/obga-case_1.jpg

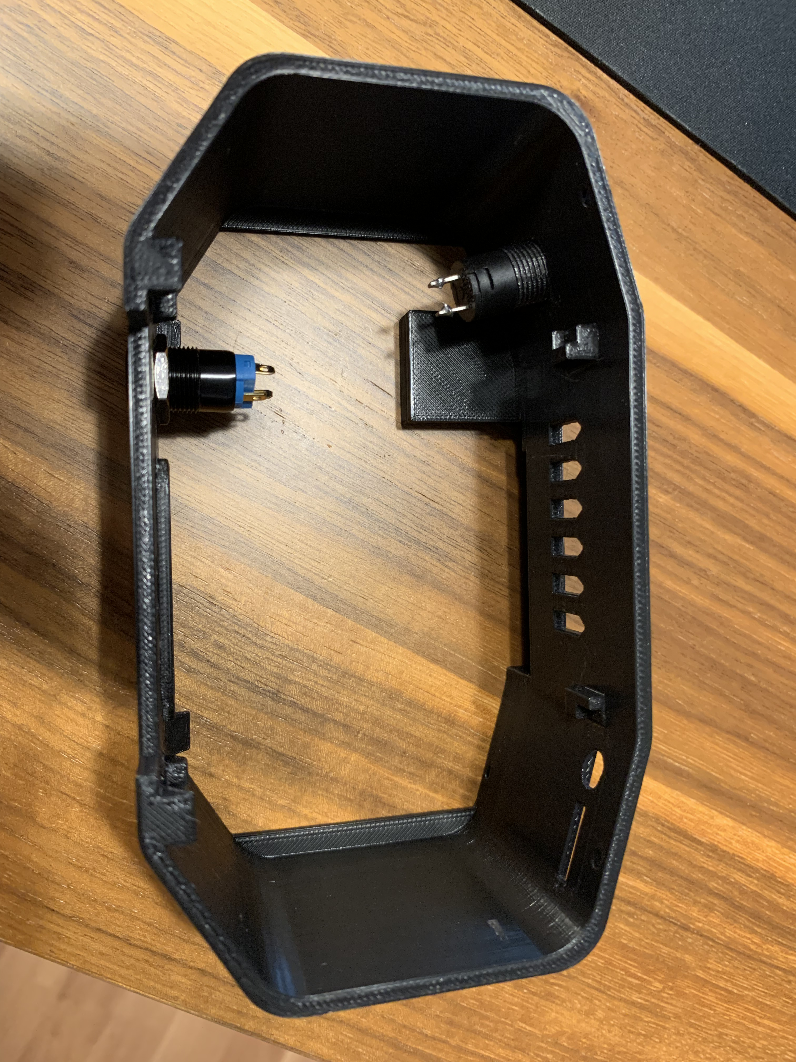
static/wiki/cases/ogba/obga-case_1.jpg
